Takazudo/zudo-case/engineering/two-way/tw-01/reference/hinge-user-photo.png

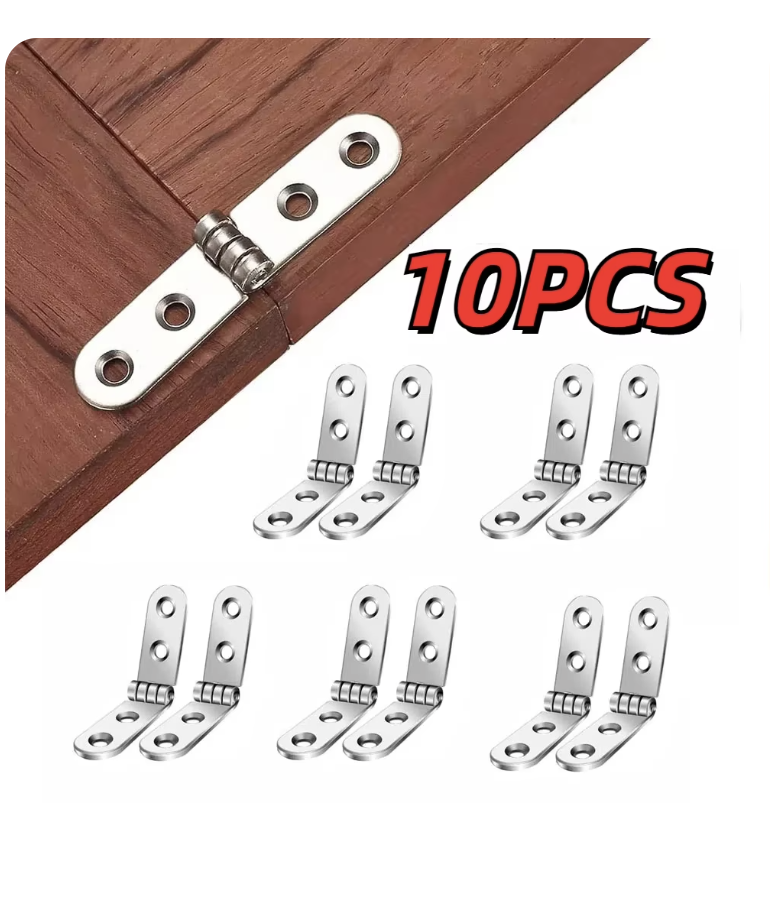
engineering/two-way/tw-01/reference/hinge-user-photo.png
