Takazudo/zudo-case/engineering/two-way/tw-01/previews/trunk-thumb.webp

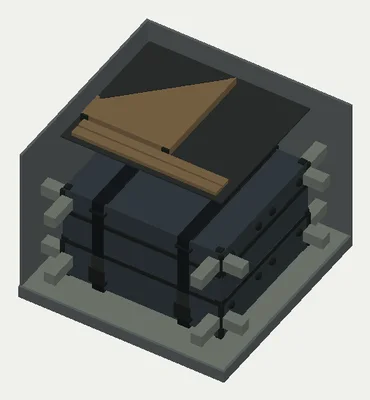
engineering/two-way/tw-01/previews/trunk-thumb.webp
