Takazudo/zudo-case/project/source-notes/user-decisions.md

# 会話中のユーザー指定・測定（抜粋）

これは会話全文のエクスポートではありません。発言順を保った関連抜粋です。個々の発言時刻は付与していません。サイト整理日は2026-09-24です。

## U01 — 製品の優先順位
「このケース考案のために重要な要素は価格と最低限の安全性。」
「可能であれば一枚板の組み合わせ＋ガードが利便性が高く、価格も抑えられそう」

## U02 — 外観、材料、在庫
「この商品自体が嗜好品であるため、ある程度の見た目の良さが必要」
「鉄板については、最初に提示してもらったものだとアルミが望ましい」
「アルマイト加工をした場合は黒にしたい」
「20x20x16 を大量にzudo-block用に所持しており、可能であればこれを使用したい」

## U03 — レールを独立させる
「エンクロージャとの間に5mm高のナイロンワッシャーを使用し、レールだけが分離出来る構造」
これは既存構造の説明。後のU06により新ケースのスペーサーは8mmへ変更。

## U04 — 積層・PCB厚
「3U fixer / 3U fixer padder / rail / 3U fixer padder / 3U fixer」
「PCB 1.6mm depth.」
ネジ頭は一度1mmで仮置きしたが、次の実測で更新。

## U05 — ネジ頭と金具の実測
「1.3-1.4mmであるため、1.4mmであると考慮」
「こちらは実測、2mm。ただしL字ブラケット自体が微妙に曲がってる可能性があるため2mm強ぐらいで考えた方が良い」

## U06 — 8mm案と３機種
「8mm案で。」
「3U3U1Uの40HP版、そして3U3U1Uの60HP版 も合わせて検討する」
「今回のケースで実は最も利便性が高いのは3U3U1U 40HPのケース」
「レールから前後パネルまでの余裕がありすぎること。ここはおそらく8mm程度で十分」

## U07 — 長穴の意図
「ネジ穴を正円としていないのは、穴位置の公差を考慮してのこと」
「ねじをしめるときの固定に頼って素材の誤差を吸収したい考え」
これは採用意図。R6ファイルが丸穴のままというデータ状態とは別。

## U08 — 薄型の本体ガード
「これらパーツはほぼ装飾用途と、ケース自体が他を傷つけないようにするため」
「この黒部分の幅も最低限継ぎ目を守れれば良い」
R3の1.2mm見積画面を提示し、「激安になった」。画面合計2,264円。

## U09 — 蓋は単純に
「our lid is the simple, original 10BOX style lid, but if the user want to take this to outdoors, they use that band things.」
「all right. so we'll do this plan. so, the final case lid style will be the simple original 10box style one.」
M3補助固定・回転ロック・スライドロックは最終案に含めない。

## U10 — 費用の対象
「レール部分は別途作っているのでこの計算に含める必要は無い」

## U11 — 引継ぎ
「zudo-doc based organized doc set」
「作ってもらったらあとはこっちでDLして整えるからその形でヨロシク」
