Takazudo/zudo-case/engineering/r9-fitfix-01/handoff/LOCAL-HANDOFF.md

# ローカルでの引継ぎ — R9-FITFIX-01

基準コミット `7f04c5bda0672ecf2cded79b6e1b48ad141e64b5`。
このセットは #99 / #100 / #101 の**修正コード＋実行済み候補CAD**です。レビュー文章だけのセットではありません。

## 何が終わり、何が残るか

| 作業 | 状態 |
|---|---|
| 下辺Lカバー、角の返しの修正 | 実装・クラウド生成済み |
| 壁厚と横方向の嵌合/接着すきまの分離 | 実装、BREPの厚さプローブで確認 |
| 実ガード上端から蓋座面・天板下面・段差を導出 | 実装・接触面積と公称着脱確認 |
| C1/C2修正＋C4/C5追加 | 生成・STL/STEP再読込済み |
| プレビュー | 同じ生成形状を内蔵。クラウドはWebGL不可のためCanvas簡易描画で操作検証 |
| Python3.12/CadQuery2.7系での再生成 | **ローカル待ち** |
| 現行R9の実DXFと本体穴パターン比較 | 比較ツール作成・合成fixtureテスト済み。実ファイル比較はローカル待ち |
| zudo-doc/current-spec/release-state/sync-r9-ledgerへの統合 | **未適用**。候補を混在させず版を分ける |
| GitHubへのpush、Issue close、製造承認、有償注文 | **未実施** |

## 最初のコマンド

まずzipを展開し、その中の`apply-overlay.py`を使います。既存ファイルは上書きしません。

```sh
python /path/to/zudo-case-fitfix-01/apply-overlay.py /path/to/zudo-case
# 内容・パスを確認後:
python /path/to/zudo-case-fitfix-01/apply-overlay.py /path/to/zudo-case --apply

cd /path/to/zudo-case/engineering/r9-fitfix-01
uv run --locked --project ../r9-prototype-01 python build.py
uv run --locked --project ../r9-prototype-01 python tests/test_geometry.py
uv run --locked --project ../r9-prototype-01 python tools/compare_r9_patterns.py
```

基準のGitHubコピーは接続済みGitHubツールで確認し、重要なR6入力６ファイルはGit blob SHA一致を確認済みです。ただしコンテナからGitHub/PyPI/npmへ直接接続できず、リポジトリ全体のclone・固定環境復元はしていません。cloud-outputのCADを、そのまま固定環境での再生成結果だと記録しないでください。

## 統合方針

`engineering/r9-fitfix-01`を独立した候補版として取り込む方法を推奨します。R9-PROTOTYPE-01の出力/台帳は履歴へ残し、同じ版名のまま差し替えません。別の候補名へ改名して取り込む場合は、ファイル・manifest・プレビュー・台帳の版を一括で合わせてください。

このコードの本体参照は、現在R9も継承している**保存R6の公称部品**を読み取り専用で再構築します。36本の長穴を含む本体５枚はR9の穴ルールで再作成しています。ローカルでは比較ツールで現行R9のDXF一致を確認し、必要なら本体参照を現在のR9ジェネレーターの実Part/配置インスタンスに置き換えてください。再構成した金具と実物の形が一致すると保証したものではありません。

1. 固定環境で生成し、修正前R9と新候補の本体３パターンを比較する。
2. 生成コードをレビューし、ガード主要部の実肉厚、屋根の直接着座、側面接着空間の解釈を確認する。
3. 新候補ディレクトリを読み込めるよう、`sync-r9-ledger`等のR9固定パスをパラメータ化、または新候補専用の入口へ分離する。古いR9のmanifestへ新しいhashだけを入れない。
4. 確認後の`tools/make_ledger_proposal.py --after-local-verification`をJSONへ保存し、candidate_filesの追加・蓋の現行候補指定に使う。候補と製造承認を混同しない。
5. docsの生成表/比較/BOM/プレビューの参照を新候補へ統一。publicのコピー後に公開資産ハッシュとサイズを検査し、旧画像との混在を防ぐ。
6. 既存CIのdocs/tables/ledger/assets/type/build/preview確認に加え、新しい11回帰テストと全体CAD生成を実行する。
7. ローカルで検証した新候補のoutを必要なファイルに絞ってGitへ追加し、コード差分と固定環境の結果をGitHubへ反映し、#99〜#101のコード課題としての完了可否を判断。G03/G04等の現物結果は別のまま。

## 重要な設計判断

**今回の支持面は金属との直接接触です。** 上端ガードの屋根下面はZ=91、本体上端へ載り、その屋根上面Z=92.2が蓋の座面です。以前の「全高93.4を上端Zと見なす」「蓋が0.5浮く」状態をなくしました。

側面の0.30mmの空きは、fit0.15＋adhesive0.15という候補配分です。これは「0.15mmテープを貼ればそのまま全て埋まる」という意味ではありません。実空間を充填して保持できる接着剤、またはテープ/当て材を選び、実測・試験で調整してください。上面/底面へ追加のテープを入れる場合はハードストップの高さが変わるため、パラメータとモデルを修正します。

**幅・奥行が各0.6mm増えます。** 金属本体寸法は変えず、外側ガードが片面0.3mm外へ増え、内側返しも実肉厚を確保します。蓋天板は基本案228.2×332.8×1.5mmです。1.0mm案の専用天板は227.8×332.4×1.5mmです。

部品を厚い旧形状へ戻す変更ではありません。基本案のガード総体積は約39.235cm³、蓋PA12枠は約84.378cm³です。価格は未取得。過去の2,264円は現在見積ではありません。

## 小型試験片を発注する前に

- C1-01〜05: 各１個。C1-06/07は同一形状を各２個として40mmの対を作る。
- C2-01の壁・ガード・天板は、C2-02/03へ再利用可能。比較用の蓋フレームは３種類。
- C4: 実際の床＋壁＋下辺Lカバー。
- C5: ２立板＋上端コーナー。
- PA12とアルミは別ZIP/別材質。`BOM.csv`のorder_quantityを優先し、0の再利用部材を重複発注しない。
- C3の座金受け面とネジ/工具アクセス、接着保持、実ノブ高さ、バンド/たわみは依然として未確認。

どの試験片も製造承認済みを意味しません。ただし試験片は未確定部分を調べるためのものです。全ての現物検証完了を試験片作成の前提にする循環にはしないでください。

## パッチ適用時の補足

`changes.patch`は16ファイルを新規追加するsource-only差分です。`git apply`時にベンダーThree.jsのGLSL文字列について末尾空白の警告が出ることがあります。元のライブラリ表現を保存しており、通常の適用は成功します。`apply-overlay.py`を使う場合はパッチも続けて適用しないでください。
