Takazudo/zudo-case/engineering/r9-prototype-01/out/DIFF-FROM-R6-R8.md

# R9-PROTOTYPE-01 / 7U40 — R6・R8との差分と梱包内容

**状態:** 製作候補・未承認。R6は本体形状の起点、R8は載せ蓋の表示用コンセプトです。ここに記すR9データも製作承認ではありません。

## R6本体からの変更

- R6由来の本体寸法をもとに、独立したアルミ板５枚を維持しています。板厚1.5 mm、A5052、黒アルマイトは候補です。
- ブラケット位置36か所を5.5 × 7.5 mm、±1.0 mm移動の長穴候補として出力しました。位置誤差を調整し、仮締め後に外形・直角を整えて本締めする狙いです。候補の長軸は折曲げ線に直交しますが、方向と移動量は製造確認が残ります。レール固定穴10か所はφ5.5 mmの丸穴を維持します。
- t1.2 mm・被覆5 mmのPA12-HPガードを主候補、t1.0 mmを比較候補として分離しました。ガードは保護用カバーで、構造接合には使いません。接着・保持・現物嵌合は未確認です。
- R6本体の穴位置は名目形状を引き継いでいます。ブラケット実物への照合、公差、ワッシャー、ねじと工具のアクセスは完了していません。

## R8蓋コンセプトからの変更

- 採用したロックなしの構成を具体化するため、直線的に載せて持ち上げる蓋と、アルミ蓋板＋４分割PA12位置決め枠を7U40候補形状として書き出しました。運搬時の保持は別体の外周バンドを想定します。
- R7のM3蓋・本体ロック、フック、回転、スライド、磁石は採用していません。蓋板とPA12枠の組立ねじは別部品ですが、仕様は暫定です。
- R8の表示用形状を製作用ファイルとして再利用したものではありません。R9ジェネレーターで出したSTEP/STL/DXFは候補データで、蓋とガードの実嵌合やノブ・ケーブル空間を検証していません。
- 蓋上がり30 mm、モジュール板2 mm＋ノブ25 mm、ケーブルを外す前提は表示上の仮定です。全モジュールのノブ高さ・配線条件を検証した値ではありません。

## 重要な未確認事項

- 長穴は36か所候補です。現在の10 mm外径ワッシャー案は壁側の複数位置で受け代が不足します。必要外径11.5 mm以上は試す候補で、選定済みではありません。
- ガード保持・接着、公差、黒染色条件、蓋枠の座面、工具アクセス、実ノブ高さ、バンド長・張力・蓋たわみが未確認です。
- 保存済みR9検証は名目CAD/データ整合の確認です。FEA、強度、材料適合、物理嵌合、落下、疲労、運搬試験を示しません。
- G01–G11 は未完了です。サプライヤーへの送付、発注、製造承認を行う状態ではありません。

## ZIPの範囲

- アルミ: ６枚の板のSTEP/DXF、穴テーブル、長穴チェック。
- PA12: ガードt1.2主候補、t1.0比較候補、蓋枠４部品のSTEP/STLと数量表。
- クーポン: C1、C2、C3のファイルと、ZIP内相対パスを記録したcoupon-manifest.json。
- 各ZIPは25 MiB未満で、`READ-BEFORE-ORDER.txt`とSHA-256付きpackage-manifest.jsonを含みます。

## 見積とサイズ

現在の材料・加工・印刷見積はありません。価格欄はnullです。既存在庫ブラケット18個だけは追加現金支出0円として扱い、製品原価は不明のままです。レール、fixer、padderの費用は依頼により除外しました。異寸法の過去R3ガード価格は流用していません。

新たにコミットするファイル別サイズと合計は `SIZE-INVENTORY.json` に記録します。`engineering/r9-prototype-01/.gitignore` が `out/` 全体を除外するため、CADの重複中間STL、hardware-envelope、アセンブリ検査物、プレビューmesh/断面画像はコミットせず、必要な6枚等を各候補ZIPにだけ収録します。
