Takazudo/zudo-case/engineering/r6-body/docs/family-final-review.md

# R6・3ケースの独立レビュー結果

`zudo-case-family-preview` の最終モデルを確認した。元レールSTL、PCB全輪郭、生成メッシュ、PCB STEP、穴配置、ガードカタログ、最終検証結果を照合し、以下の範囲に未解決の不整合は見つからなかった。

| 項目 | 3U60HP | 7U40HP | 7U60HP |
|---|---:|---:|---:|
| 金属外形W×D×H mm | 330.4×154×91 | 229.4×334×91 | 330.4×334×91 |
| 実レール長mm | 305 | 204 | 305 |
| レール本数 | 2 | 6 | 6 |
| fixer〜前後板内面の隙間mm | 8.23407 | 8.122772 | 8.122772 |
| Lブラケット個数 | 16 | 18 | 18 |
| 接合穴のブラケット同軸確認 | 32穴一致 | 36穴一致 | 36穴一致 |
| ケースへのレール固定 | 片側2点 | 片側5点 | 片側5点 |
| ガード個数／種類 | 12個／4種類 | 16個／6種類 | 16個／6種類 |
| t1.2ガードの最大部品寸法mm | 166.4 | 168.2 | 168.2 |

## 元形状と配置

- 元レールの全592三角形を保持している。各変換は回転・移動だけで、逆変換後の頂点最大誤差は7.1×10⁻¹⁵mm以下。
- fixer／padderの元輪郭・切り抜きの全頂点を生成メッシュへ照合した。最大座標誤差は5.7×10⁻¹⁴mm以下。板厚1.6mmと、7Uの各padderの外形基準による配置が維持されている。
- 7Uの6本は、各行で前後の外リップが外側へ向く交互配置。隣接行のレール本体同士にはY方向で**0.330246mm／0.365509mm**の正の隙間がある。元STL全頂点の外接範囲がY方向で分離しているため、本体同士が交差していないことを確認できる。
- 7Uの片側5点のM5取付ボルトを頭径9mm・高さ1.4mmとして独立に再構成し、出力PCB STEPと比較した。全固定点でPCBとの交差体積は0mm³。左側は同じYZ配置と積層の鏡像である。
- 7Uのfixer下端から底部L金具上端までの垂直包絡差は**7.984619mm**。

## 頭径の追加検討を区別

生成側の検証では、実厚2mmのL、内側の接合ネジ頭、ケース固定用頭、ガード、PCBの実体交差はない。L占有厚2.2mm・レール端頭径12mmの追加検討でも、ブラケット側との交差はない。

一方、7Uの隣接するレール端頭を両方D12と仮定すると、軸間11.9960175mmの組で約0.004mmの径方向包絡重複が生じる。この値はケース隙間とは別の、既存レールユニット内の関係。模式表示D9の頭同士は交差しない。D12は現物の保証上限ではなく、追加の検討用寸法として分けて記録されている。

## 底板と脚

底板の8点／10点だけはネジ頭を外側に向け、ワッシャー・ナットを内側へ移している。側面のfixer固定の向きは変更していない。

各ケースの脚は仮のD10×高さ3mmを4個、中心を各外縁から20mm内側に配置。脚と底ネジ中心の最短距離は約22.192mmで、両者は重ならない。

- 脚下面：Z−3mm。
- 底板ネジ頭の最下面：Z−1.4mm。
- 接地面から底ネジ頭までの公称余裕：**1.6mm**。
- 全パーツの最下面は脚のZ−3mmで、それより下へ出るネジ・ナットはない。
- 脚込みの高さはt1.2ガード時**95.2mm**、t1.0時**95.0mm**。ガードだけを含めた外形高さとは異なる。

脚は既製貼付ゴム脚を想定する模式部品で、JLCガードSTLやガード体積には含めていない。

## データの範囲

ガードは全32種類のSTLについて、生成検証で閉じたメッシュ・正の体積・CAD体積との一致が確認されている。各モデルのガード数量と最大寸法は独立にカタログと照合した。

ブラケットの穴中心と曲げ部、模式表示の頭径・ネジ長・ナット、脚の製品選定、ガードの保持方法と嵌合公差には設計前提が残る。上記は公称寸法と配置の確認で、製造公差や荷重を含む完成品の試験ではない。

機械読取用記録：`family-core-independent-checks.json`、`family-final-foot-checks.json`、`expected-7u-rail-gaps.json`。
