Takazudo/zudo-case/engineering/two-way/tw-01/reference/PROVENANCE.md

# TW-01 provenance

Derivative of the verified original F5 source archived at `../../f5-reference/`.
Original ZIP SHA-256: 2060f83d75c93c7e5a29e6fe0751ac1fae101dccba8c7bf08d2a43080f7b4e58.
TW-01 is not byte-identical F5. Historical source receipts belong to F5 only.

Maintained frame data consumes canonical R6 saved rail meshes, PCB outer/cutout vertices and placement records. Input hashes and Shapely/GEOS version are embedded in `source/frame-data.js`.
No geometric fitting or rail topology repair. The display triangles are not a manufacturing definition.
Hardware, strap/stand/hinge envelopes remain provisional. The user's hinge drawing is retained unchanged; its dimensions provide no load rating or mounted folding proof.
