Takazudo/zudo-case/src/content/docs/two-way/rail-frame.mdx

---
title: "元レール・PCBフレーム"
description: "元形状、配置基準、8mm積層、Cの70mm蓋と表示用三角形の範囲。"
sidebar_position: 20
---

import { TwoWayFrameTable } from '../../../components/two-way-table.jsx';

## 両トレーに元のユニット

Aは元の3U/60HPを1組ずつ、Bは同じ3U/60HPを**1 mm離して2組ずつ**使います。B用に6Uの側板を新設・伸長しません。Cは7U fixerを全体のまま、3U＋3U＋1Uの行別padderと使います。

<TwoWayFrameTable />

数量は各トレー分で、2トレーにはその2倍を使います。これは元フレームの数量であり、ケース全体のBOMではありません。

## 固定と座標基準

レールは40HPが204 mm、60HPが305 mm。元の全頂点と全インデックスを保持し、剛体変換だけを適用します。元の重複・非多様体面を勝手に修復しません。

積層は **padder 1.6 + fixer 1.6 + 側面スペーサー8 + 外側座金1 mm**。皿頭高さ1.4 mmの検討値を保持します。実ねじ・ナット・穴加工・工具アクセスの成立は別途確認します。レール付近の隙間を常設ベゼルで埋めません。

正規ソースは `engineering/r6-body/source-data/`。7Uは元Xが奥行V、元Yが列方向Uです。わずかな外形段差・穴中心・padderのずれを維持します。配置は保存済み `placements.json`、空の3Uケース固定軸だけはR6 `build_geometry.py` の明示組立規則を使用します。近い穴や対称位置を推測しません。

## Cの48 mmと70 mm

元7Uフレームは前面から約61.950925 mm後方まで届きます。板厚1.5 mmでは、蓋48 mmの背板余裕は **−15.450925 mm**、蓋70 mmは **＋6.549075 mm**。TW-01のCの初期値は70 mmです。

ビューアーで48 mmを入力すると、フレームを切り縮めず干渉警告を出します。正の数値もモジュール適合や工具アクセスを保証しません。モジュール後方の余裕・元フレーム後端・局所の補強材やバス基板は分けて表示します。

## F5とTW-01の違い

F5のレールは元メッシュそのままですが、PCBの丸穴・長穴は表示用近似でした。TW-01は保存済みの外周と切欠きの全ポリゴン頂点を読み、固定版の変換環境で三角形化します。元KiCadとソース輪郭、表示三角形、仮金具は異なる精度区分です。

[資源とマニフェスト](./resources.mdx)には入力・出力ハッシュと単位を記録します。GLBを製造データとして発注しないでください。
