Takazudo/zudo-case/src/content/docs/handoff/tasks.mdx

---
title: "次に行う作業"
description: "7U40から試作へ進め、共通構造を３機種へ展開する。"
sidebar_position: 20
---

R9-PROTOTYPE-01の[未承認候補](../design/r9-prototype-01.mdx)と[試験手順](../verification/fit-test.mdx)が用意された。次は[空欄の現物測定](../verification/measurements.mdx)を必要な範囲で埋め、C1→C2→C3の判定条件を先に決め、有償試作をユーザー判断で進める。座金受け面（仮OD10mmで壁26穴不適合）、接着保持、実ノブ、バンド荷重、天板たわみが残る。見積文は[未送信RFQ](../manufacturing/r9-rfq-draft.mdx)。下記の表は当初の工程案として読む。

## まず7U40で共通部を詰める

ユーザーが持ち運びで重視している7U40を最初の確認対象とする。ただし共通部の変更は3U60・7U60にも追従させる。これは進行案であり、発注数量を確定したものではない。

| 順番 | 作業 | 成果物 |
|---|---|---|
| 1 | R9候補の版・ハッシュ・警告を確認 | 同一版のCAD、プレビュー、数量表 |
| 2 | 手持ち金具・ネジ・座金を確認 | 代表寸法、長穴が吸収すべき範囲 |
| 3 | R9の短い本体ガードをC1で確認 | PA12・アルミ端・接着層の記録 |
| 4 | R9の上端ガードと蓋をC2で確認 | 段差と天板の現物記録 |
| 5 | 実金具と長穴をC3で確認 | 座金受け面、締結アクセス、CAD修正 |
| 6 | ケース１台を組み、バンドを試す | 実モジュール・ノブ・リュックでの確認 |
| 7 | 最新データで業者比較 | 機種別・数量別・税込税抜が明確な見積 |
| 8 | 検査条件と承認資料を確定 | 承認manifest、製作ZIP |

## ローカルのAIエージェントへの引継ぎ文

```text
AGENTS.md、project/current-spec.json、project/open-issues.jsonを最初に読んでください。
現行方針は真上へ外す載せ蓋＋外周バンドです。
R9-PROTOTYPE-01は7U40の未承認候補。file-table.jsonとvalidation.jsonを確認してください。
座金受け面、ガード接着、蓋と実ノブ、バンド荷重をC1→C2→C3から確認します。
R7のM3補助固定、回転/スライドロック、奥フックは復活させないでください。
ユーザー確認済み寸法を守り、表示上の仮値は現物確認済みと扱わないでください。
7U40の実測と小片の結果を記録し、承認前に発注しないでください。
```

## 作業を引き継ぐ際の境界

今回の依頼はドキュメント作成であり、注文操作や新CADの製作承認は含まない。次の担当が自動的に発注へ進めないよう、リリース状態をfalseのまま残している。

`engineering/r6-body`と`engineering/r8-preview`の元ファイルは保存する。変更は新しい作業ディレクトリーと版で行い、元データとの差分を残す。
