Takazudo/zudo-case/src/content/docs/models/7u60.mdx

---
title: "3U＋3U＋1U・60HP"
description: "本体はR6の名目CAD、載せ蓋はR8プレビュー。7u60の寸法と数量。"
sidebar_position: 30
---

{/* GENERATED: node scripts/sync-reference-tables.mjs / project/current-spec.json */}

## この機種

３機種に共通する金属平板と独立レールの構造を使う。 3U＋3U＋1Uは同じ平面に並ぶ。上下二段のケースではない。

R6の組立形状

## 寸法と数量

| 項目 | 値 |
|---|---|
| 本体アルミ外形 W×D×H | **330.4 × 334 × 91mm** |
| 1.2mmガード込み（脚・外側金具を除く） | 332.8 × 336.4 × 93.4mm |
| ガードと仮脚込み（外側金具を除く） | 332.8 × 336.4 × 95.2mm |
| 実レール長 | 305mm |
| レールユニット外幅 | 311.4mm |
| 全ユニットの前後包絡 | 314.754456mm |
| 前後板の内面までの片側余白 | 8.122772mm |
| 上端ガードまでの片側余白 | 7.122772mm |
| レール本数 | 6 |
| ブラケット | 18 |
| レールと外箱のM5締結 | 10点 |
| 内側8mmスペーサー／外側1mm座金 | 各10個 |
| 板の穴合計 | 46（R6の丸穴。長穴未反映） |

## アルミ本体５枚

| 部品 | サイズmm | 枚数 | 穴数/枚 |
|---|---|---:|---:|
| 底板 | 330.4 × 334 × 1.5 | 1 | 10 |
| 前後板 | 327.4 × 89.5 × 1.5 | 2 | 6 |
| 左右板 | 334 × 89.5 × 1.5 | 2 | 12 |

材質候補A5052、t1.5、黒アルマイト。外形・板厚は現在の名目値。長穴、穴中心、公差、表面の許容状態を確定してから製作承認する。

## ガード1.2mmの内訳

| 部品 | 数量 | 単体の外接寸法mm | 単体体積cm³ |
|---|---:|---|---:|
| 上端L字ガード A | 2 | 166.4 × 168.2 × 6.2 | 3.458 |
| 上端L字ガード B | 2 | 166.4 × 168.2 × 6.2 | 3.458 |
| 前後下辺・半分 | 4 | 166.4 × 6.2 × 6.2 | 2.231 |
| 左右下辺・半分 A | 2 | 6.2 × 167 × 6.2 | 2.202 |
| 左右下辺・半分 B | 2 | 6.2 × 167 × 6.2 | 2.202 |
| 縦辺コーナーガード | 4 | 6.2 × 6.2 × 81 | 1.086 |

合計**16個、35.906cm³**。1.0mm版は**29.297cm³**。STLは１個ずつ、数量を注文画面へ指定する。

<PreviewLink path="/downloads/reference/7u60-r6-guards-t1p2-NOT-RELEASED.zip">1.2mm STL一式</PreviewLink> ／ <PreviewLink path="/downloads/reference/7u60-r6-guards-t1p0-NOT-RELEASED.zip">1.0mm STL一式</PreviewLink> ／ <PreviewLink path="/downloads/reference/7u60-r6-aluminum-NOT-RELEASED.zip">アルミ参考データ</PreviewLink>

## 蓋はR8の表示寸法

天板：**328.6 × 332.2 × 1.5mm**。蓋の外周：332.8 × 336.4mm。蓋付き高さは脚・模式ねじ頭まで**128.8mm**。バンド・側面ナットの突出は別。

前後の段差を差し込み、真上へ外す。30mmのノブ用高さ、2mm厚の段差、差し込み12mm、片側0.7mmの隙間は現在のプレビュー条件で、実物のフィットを保証しない。

バンド一周の幾何概算：**923.2mm**。バックルと重なり代は含めていない。

**この載せ蓋の製作用CADは未更新。** R7のロック用枠・前後M3穴を発注しない。[R8プレビュー](../resources/current-preview.mdx)と[発注前ゲート](../verification/before-order.mdx)を確認する。

## 根拠

R6の engineering/r6-body/engineering/7u60/model-summary.json と [本体サマリー](/evidence/r6-family-summary.json)、[ガードmanifest](/evidence/7u60-t1p2-r6-guard-manifest.json)、[R8パラメータ](/evidence/r8-preview-parameters.json)から表を生成した。今回、新しいCADを検証した値ではない。
