Takazudo/zudo-case/src/content/docs/resources/body-preview.mdx

---
title: "R6・本体とレールのプレビュー"
description: "８mmスペーサーと３機種の名目寸法を確認する。"
sidebar_position: 20
---

## 本体だけ詳しく見る

**<PreviewLink path="/previews/r6-body.html">R6本体プレビューを別タブで開く</PreviewLink>**。約33MBの単一HTML。大きいためここでは自動埋め込みしない。

<PreviewSource />

R6のレール脱着表示

３機種、ガード1.2/1.0mm、分解、レール脱着、識別色、透過、断面、部品選択、STL保存がある。R6に内蔵されている保存用STLはR6形状であり、最終保持公差を入れた新リリースではない。

## このプレビューでは分からないこと

最終の長穴化、ガード保持、R8載せ蓋の製作形状、バンドの実物、電源/配線の最終収まりは未反映。ねじやナットの一部は模式値。

R8を見ると完成形の意図、R6を見ると本体の構造を確認できる。どちらか一方だけを最終発注の根拠にしない。[ファイル対応表](./files.mdx)を参照する。
