Takazudo/zudo-case/src/content/docs/overview/index.mdx

---
title: "はじめに"
description: "現在地と、製作へ進むための読み順。"
sidebar_position: 10
---

現在地と、製作へ進むための読み順。

<CategoryNav category="overview" />
