Takazudo/zudo-case/engineering/r9-fitfix-01/handoff/FIT-RECORD.md

# R9-FITFIX-01 小型試験片の結果記入用

これは未記入の記録用紙です。結果や承認は含みません。先に固定環境での再生成・ファイル比較を済ませ、実際に使った部品IDとファイルSHA-256を記録します。

## 試作ロット

| 項目 | 記入欄 |
|---|---|
| 実施日・担当 | |
| 候補版・ファイルSHA-256 | |
| 造形サービス・材質・黒染め・造形条件 | |
| 金属材質・実板厚・表面処理 | |
| 接着剤／テープ／当て材の品番・実測厚・処理・養生条件 | |
| 使用した締結材の品番 | |

## 試験片別

| 試験片 | 確かめる点 | 観察・測定 | 判定・次の変更 |
|---|---|---|---|
| C1-01〜05 | 側面すきま、屋根の着座、実肉厚、保持方法、比較条件 | | |
| C1-06/07 | ２片の継ぎ目、段差、接触する金属端 | | |
| C2-01〜03 | 蓋の差し込みと抜き差し、支持面、M3組立、0.5/0.7/0.9の比較 | | |
| C4-01 | 底板＋立板に対し下辺Lガードが収まる、接着・固定、金属端の露出 | | |
| C5-01 | ２立板が交わる角にガードが収まる、側面／屋根の当たり、端の安全性 | | |

0.30mmの側面空間は、fit0.15＋adhesive0.15という候補配分です。単に0.15mmテープを貼るだけで固定できるとは扱いません。実際に空間を埋めて保持できる方法を記録してください。上面/下面へテープを追加する場合は座面高さが変わるので、モデルへ戻して修正します。

## １台試作時の追加事項

小型片の成功だけでは、長い部品の反り、全体の組立、長穴/座金、実ノブ/スイッチ高さ、脚の圧縮、バンド締付時の天板たわみ、運搬を確認したことになりません。実荷重・操作回数・試験条件と判定基準を定め、その記録は別途残します。
