Takazudo/zudo-case/src/content/docs/models/index.mdx

---
title: "３機種の仕様"
description: "共通寸法から生成したモデル別の寸法・数量。"
sidebar_position: 20
---

共通寸法から生成したモデル別の寸法・数量。

<CategoryNav category="models" />

## 独立した2WAYの実験設計

[2WAY / TW-01](../two-way/index.mdx)は2つのモジュール入りトレーを使う別系列です。現行R9製作候補や既存3機種の仕様は変更しません。
