Takazudo/zudo-case/src/content/docs/two-way/preview.mdx

---
title: "TW-01 ワークベンチ"
description: "オフラインでも使える日本語の2WAY寸法・姿勢検討ビューアー。"
sidebar_position: 30
---

import { PreviewLink, PreviewFrame, PreviewSource } from '../../../components/preview-links.jsx';

**TW-01 / 実験設計。実機嵌合・強度・運搬・製造は未承認です。** [元資料F5との差分](./rail-frame.mdx)を確認してください。

<PreviewLink path="/previews/two-way/tw-01.html">TW-01を直接開く（別タブで使う場合もこのリンク）</PreviewLink>

<PreviewSource />

<PreviewFrame path="/previews/two-way/tw-01.html" title="TW-01 2WAY実験設計ワークベンチ" height={920} />

## 操作

A/B/Cを選び、演奏・収納・レール・接合部・トランクを切り替えます。「その他の検討姿勢」にスタンド収納・カラー部品・蝶番があります。姿勢の変更は入力した物理寸法を初期化しません。

ドラッグまたは矢印キーで回転、ホイールまたは＋−でズーム、Rで全体表示。「拡大」からEscapeで戻り、操作元へフォーカスが戻ります。PNGは選択姿勢・版・描画方式付きで保存します。

設定はTW-01の独立schemaで保存します。元F5 schema-5も明示変換して読み込みます。入力全体を検査してから置換し、破損・不正・未知schemaでは前状態を保ちます。取り込んだ派生寸法・承認フラグ・外部URLは信用しません。F4は構造が異なるため非対応です。

## 表示の限界

WebGLを使えない場合はSoftware 3Dへ切り替わります。描画方式はビューアー上部に表示します。モードやスクリーンショットは物理検証の証明ではありません。前面72/58 mmは配線プロファイルの仮定です。

収納包絡とトランク内寸、元フレーム後端とモジュール深さを区別してください。正の隙間も耐荷重・安全な閉鎖・連続開閉を保証しません。Cの48 mm蓋など干渉する入力も元形状を保持して表示します。
