Takazudo/zudo-case/src/content/docs/models/comparison.mdx

---
title: "３機種の比較"
description: "共通値と、機種によって増える板・金具・ガードを一覧にする。"
sidebar_position: 40
---

{/* GENERATED: node scripts/sync-reference-tables.mjs / project/current-spec.json */}

## 本体比較（7U40は現行候補）

| 機種 | アルミ外形mm | ガード込みmm | 金具 | ケース固定M5 | ガード個数 | 1.2mm体積cm³ | R9候補 |
|---|---|---|---:|---:|---:|---:|---|
| 3U・60HP | 330.4 × 154 × 91 | 332.8 × 156.4 × 93.4 | 16 | 4 | 12 | 27.333 | — |
| 3U＋3U＋1U・40HP | 229.4 × 334 × 91 | 232.4 × 337 × 93.4 | 18 | 10 | 16 | 39.235 | R9-FITFIX-01・未承認 |
| 3U＋3U＋1U・60HP | 330.4 × 334 × 91 | 332.8 × 336.4 × 93.4 | 18 | 10 | 16 | 35.906 | — |

7u40の現行候補は[R9-FITFIX-01](../design/r9-fitfix-01.mdx)です。上表の7U40ガード寸法・体積は同候補の生成値です。現物の嵌合・保持・運搬確認と製造判断が残り、未承認です。3u60と7u60の数値はR6/R8基準です。

単位mm。ガード込みは脚・外側ナット・蓋・バンドを除く。３機種ともアルミの高さは91mm、レールの側面離隔は8mm、前後の全ユニットからの余白は約8mm。

## 共通部と差分

40HPは実STL長204mm、60HPは305mm。HPの比で引き延ばしていない。3U→7Uは前後方向を長くし、fixerを7Uへ交換、3U padder２個と1U padder１個を各側へ配置する。

3Uは16個の金具と４点の外箱固定、7Uは18個と10点。長い左右板の底辺には中央金具を追加する。ガードの分割数も12→16個へ変わる。

[3U60](./3u60.mdx) ／ [7U40](./7u40.mdx) ／ [7U60](./7u60.mdx)

## 蓋と運搬

全機種でR8の載せ蓋＋バンド２本を採用。蓋高さ30mm、閉じたモデルの高さ128.8mmは共通の表示条件だが、ノブ高さ・締付時の天板のたわみを確認して最終化する。

R8の天板サイズは各機種ページに示した。機種間で同じ部品として注文できるかは、完成したCADのファイルと数量を照合して決める。似た外形だけで同一品へまとめない。

出典：[R6サマリー](/evidence/r6-family-summary.json)、[R8パラメータ](/evidence/r8-preview-parameters.json)。
