Takazudo/zudo-case/src/content/docs/decisions/index.mdx

---
title: "判断履歴"
description: "採用・不採用と、変更理由を残す。"
sidebar_position: 70
---

採用・不採用と、変更理由を残す。

<CategoryNav category="decisions" />
