Takazudo/zudo-case/src/content/docs/handoff/index.mdx

---
title: "ローカルへの引継ぎ"
description: "zudo-docの初期化、更新手順、次の作業。"
sidebar_position: 80
---

zudo-docの初期化、更新手順、次の作業。

<CategoryNav category="handoff" />
