Takazudo/zudo-case/src/content/docs/resources/index.mdx

---
title: "データとプレビュー"
description: "現行プレビュー、版別のCAD、根拠ファイル。"
sidebar_position: 60
---

現行プレビュー、版別のCAD、根拠ファイル。

<CategoryNav category="resources" />
