Takazudo/zudo-case/engineering/r9-prototype-01/out/preview/sections/guards-adhesiveLayer.png

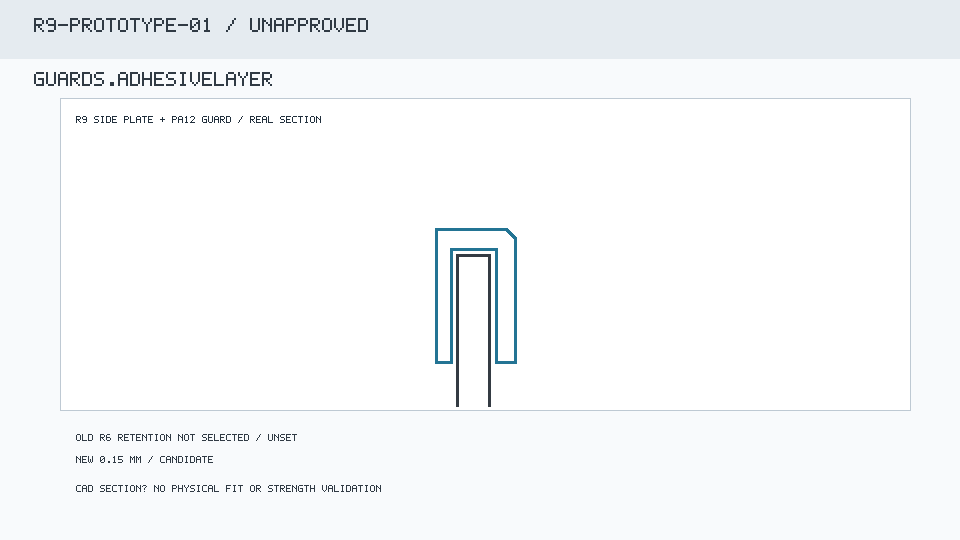
engineering/r9-prototype-01/out/preview/sections/guards-adhesiveLayer.png
