Takazudo/zudo-case/engineering/r9-prototype-01/out/preview/sections/lid-knob_envelope_height.png

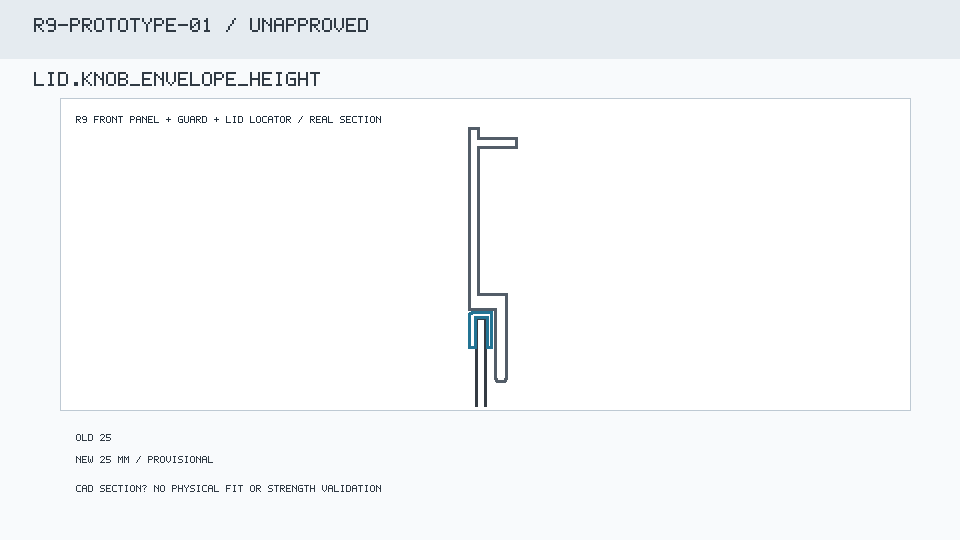
engineering/r9-prototype-01/out/preview/sections/lid-knob_envelope_height.png
