Takazudo/zudo-case/engineering/r9-prototype-01/out/preview/sections/slots-bearing_overlap.png

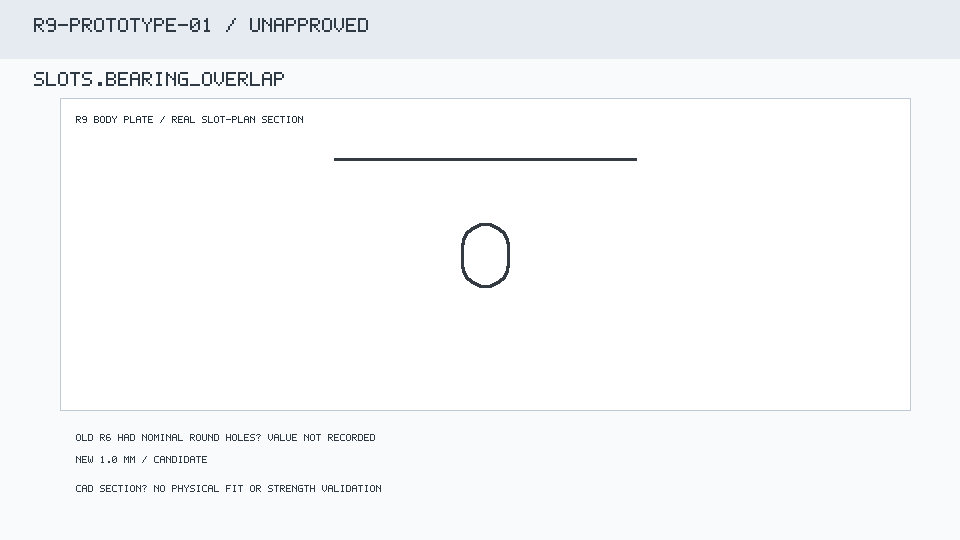
engineering/r9-prototype-01/out/preview/sections/slots-bearing_overlap.png
