Takazudo/zudo-case/engineering/r9-prototype-01/preview/shots/r9-prototype-01-daily.png

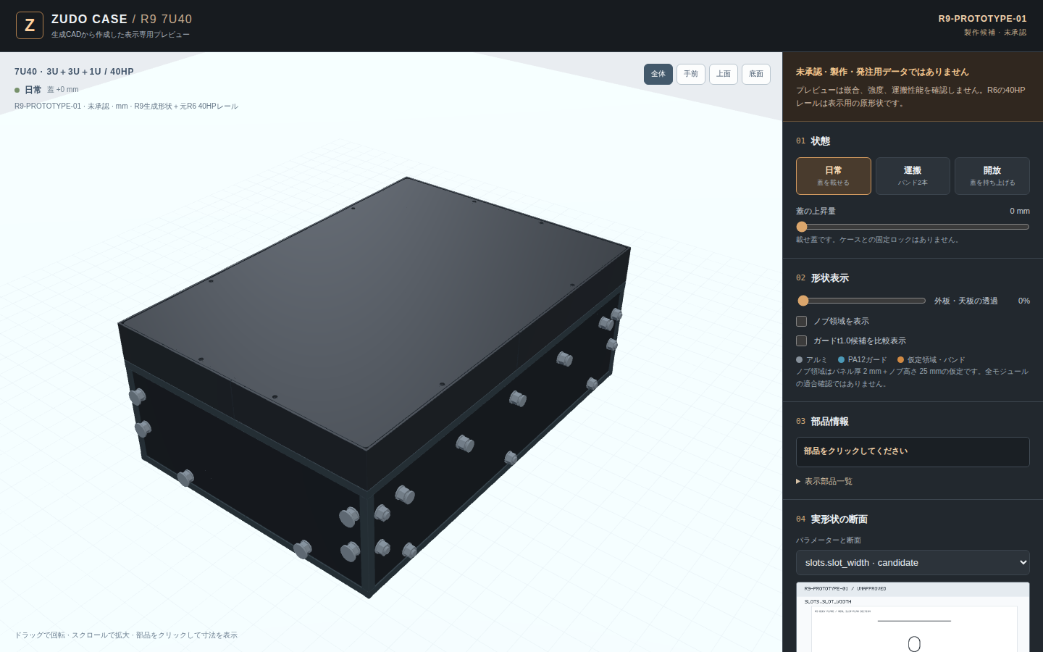
engineering/r9-prototype-01/preview/shots/r9-prototype-01-daily.png
