Takazudo/zudo-case/engineering/r9-prototype-01/preview/shots/r9-prototype-01-open-mobile.png

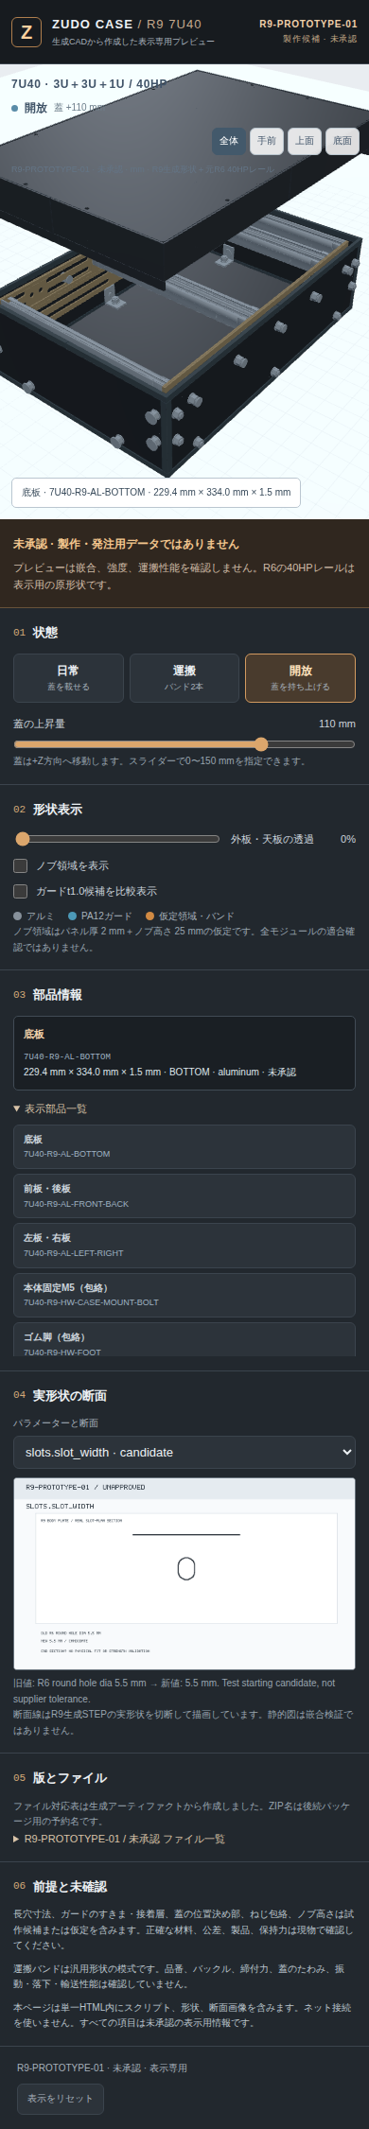
engineering/r9-prototype-01/preview/shots/r9-prototype-01-open-mobile.png
