Takazudo/zudo-case/engineering/two-way/f5-reference/previews/closed-thumb.webp

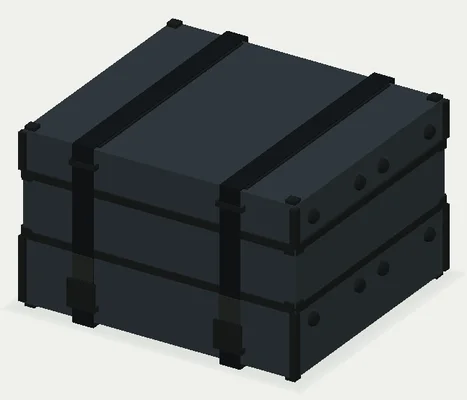
engineering/two-way/f5-reference/previews/closed-thumb.webp
