Takazudo/zudo-case/engineering/two-way/f5-reference/previews/frame-thumb.webp

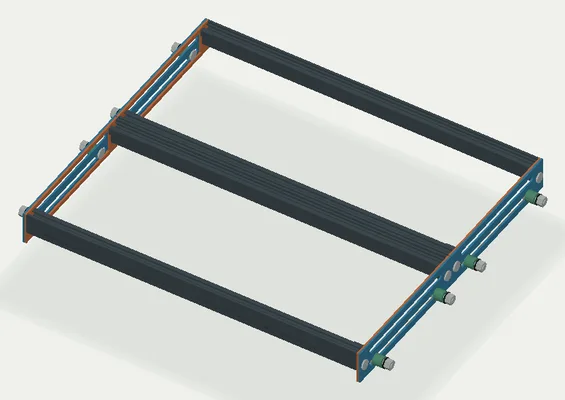
engineering/two-way/f5-reference/previews/frame-thumb.webp
