Takazudo/zudo-case/engineering/two-way/f5-reference/reference/hinge-user-dimensions.png

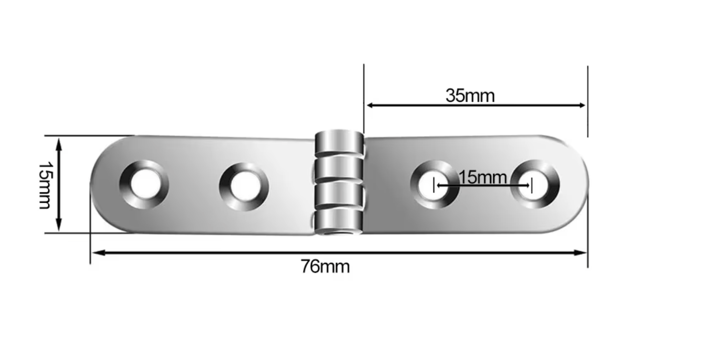
engineering/two-way/f5-reference/reference/hinge-user-dimensions.png
