Takazudo/zudo-case/engineering/two-way/tw-01/evidence/docs-390.png

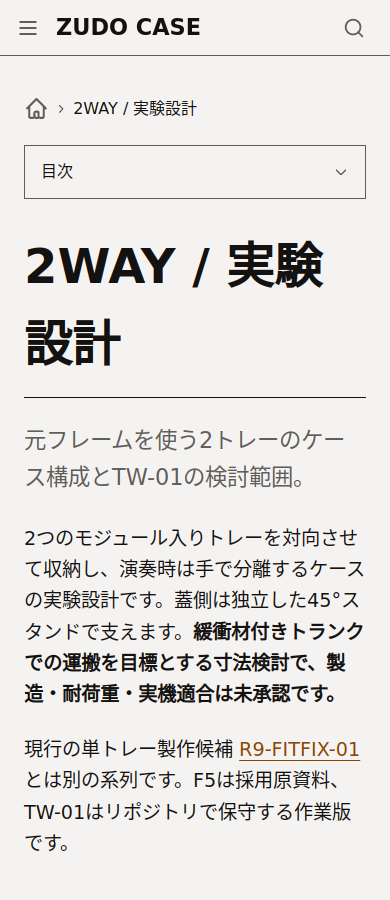
engineering/two-way/tw-01/evidence/docs-390.png
