Takazudo/zudo-case/engineering/two-way/tw-01/evidence/software-390.png

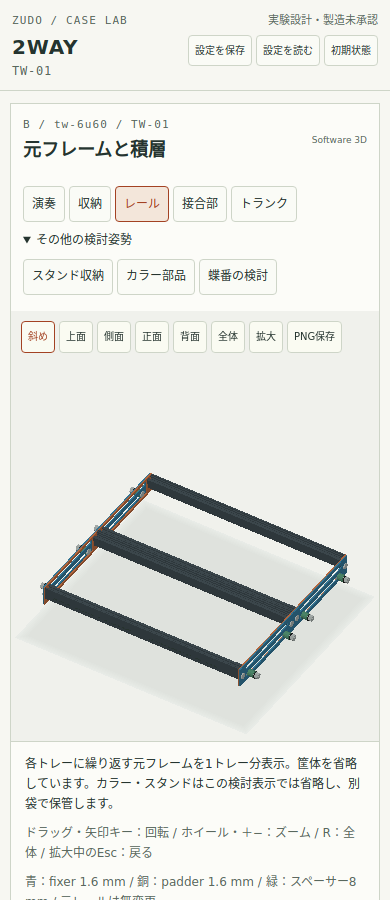
engineering/two-way/tw-01/evidence/software-390.png
