Takazudo/zudo-case/engineering/two-way/tw-01/evidence/webgl-B-play.png

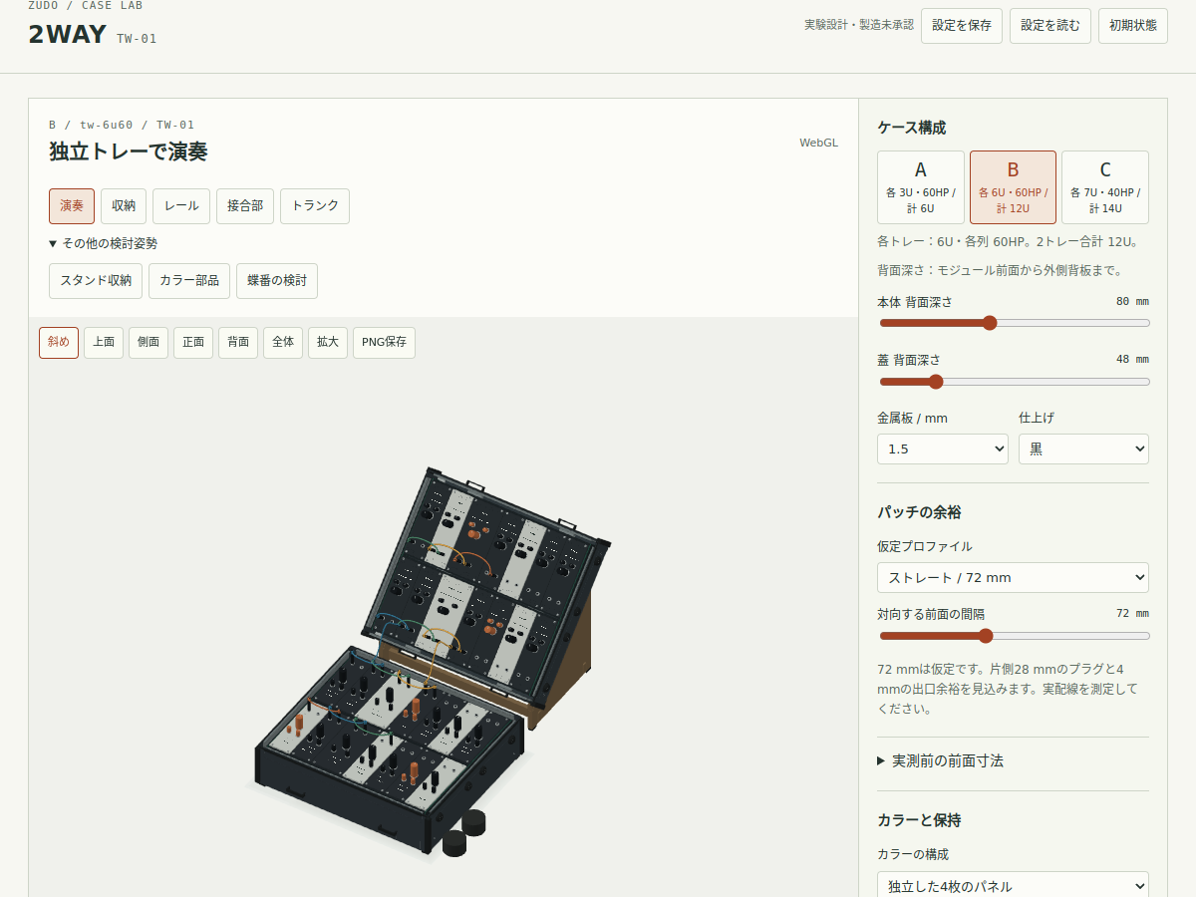
engineering/two-way/tw-01/evidence/webgl-B-play.png
