Takazudo/zudo-case/engineering/two-way/tw-01/evidence/webgl-C-invalid48.png

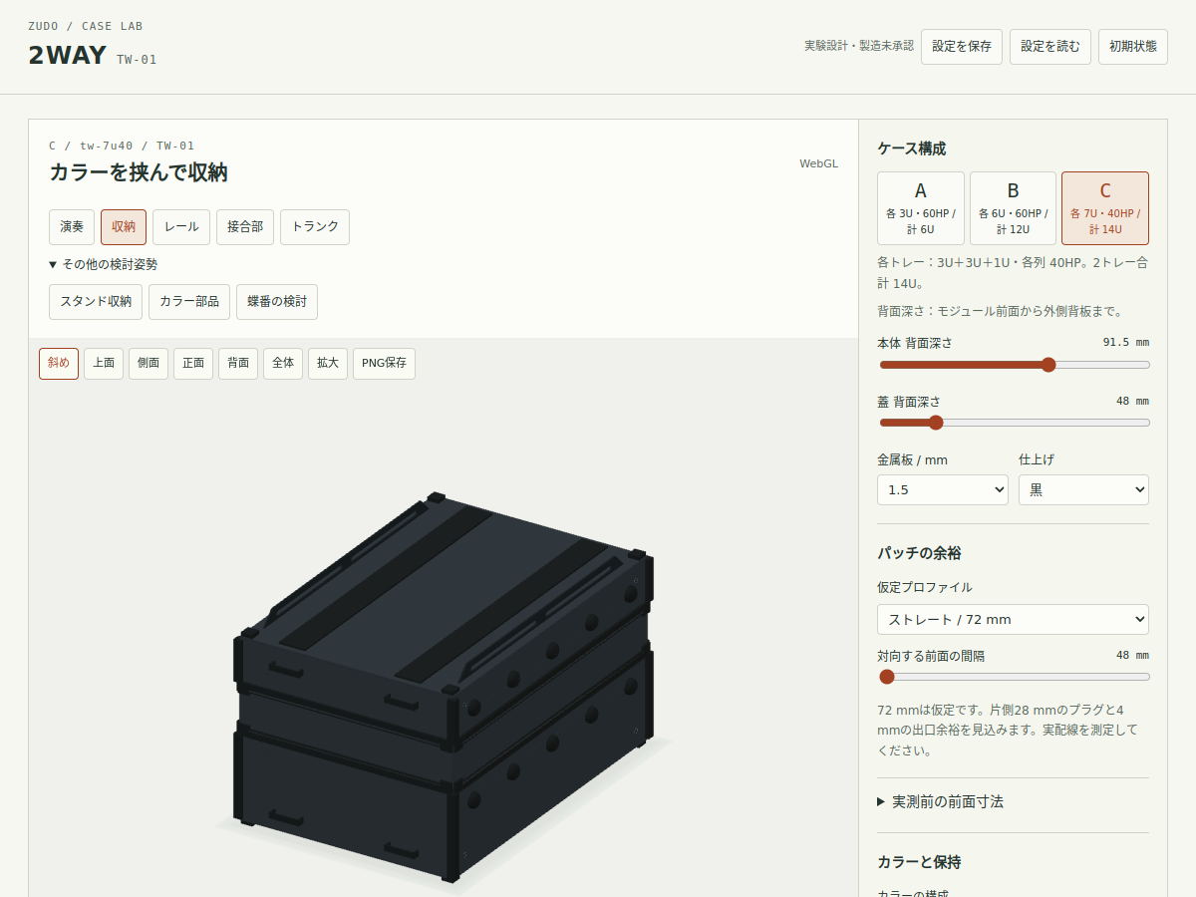
engineering/two-way/tw-01/evidence/webgl-C-invalid48.png
