Takazudo/zudo-case/public/assets/evidence/r2-jlc-quote-incomplete-quantity.png

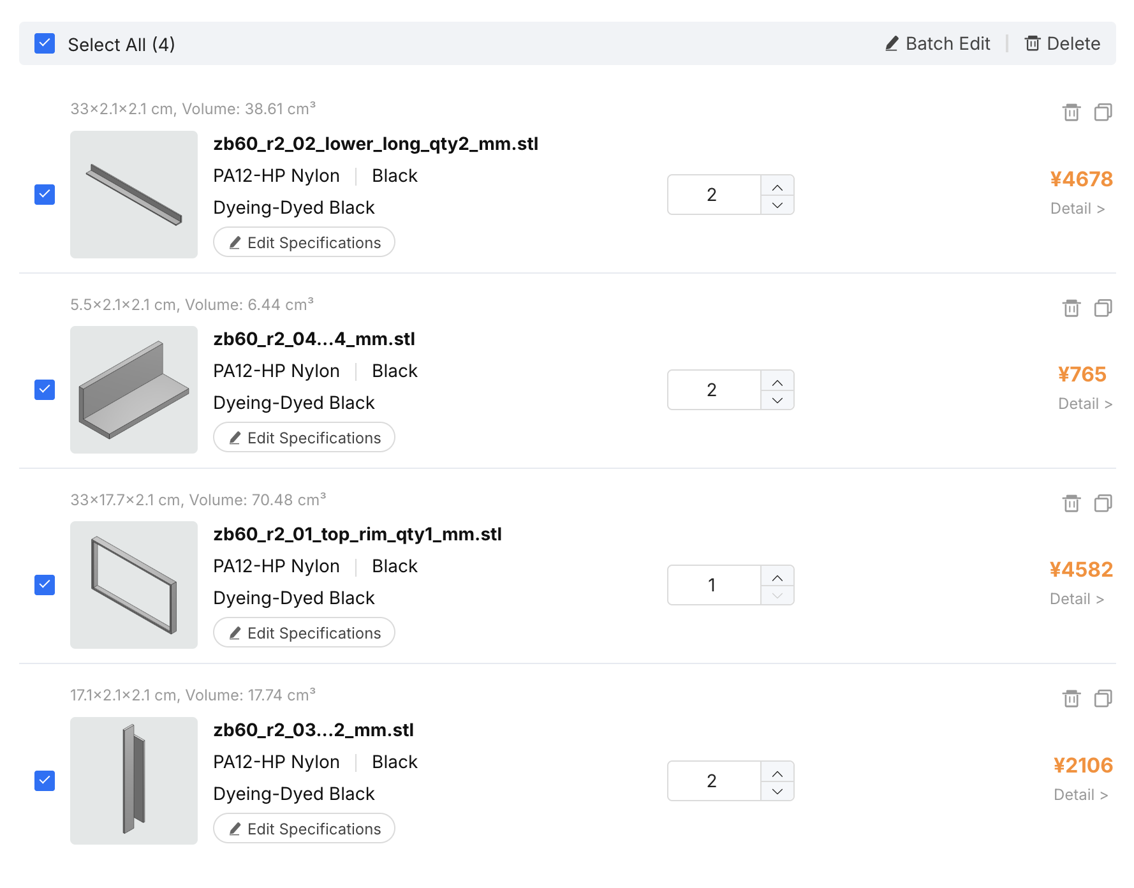
public/assets/evidence/r2-jlc-quote-incomplete-quantity.png
