Takazudo/zudo-case/public/assets/evidence/r3-jlc-quote.png

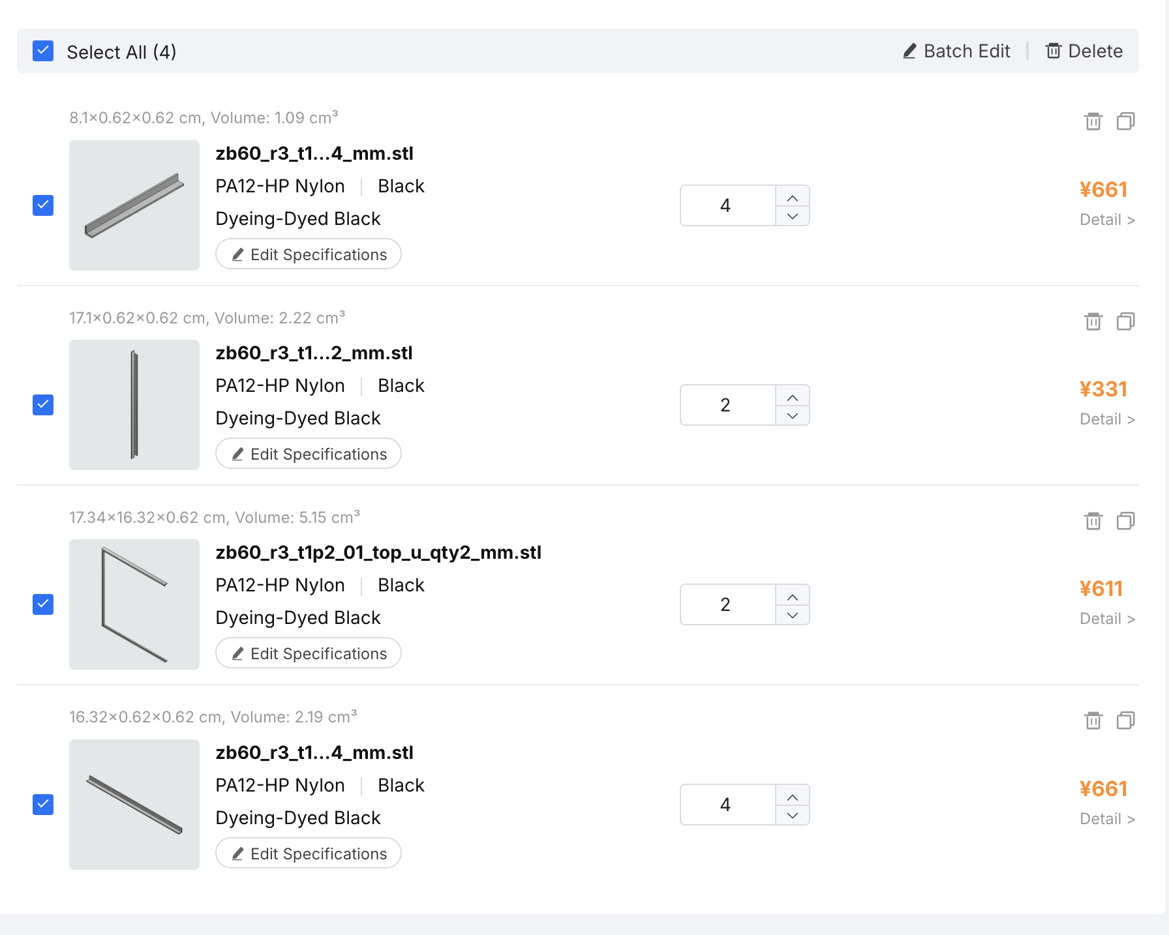
public/assets/evidence/r3-jlc-quote.png
