Takazudo/zudo-case/public/assets/images/r6/3u60-rail.png

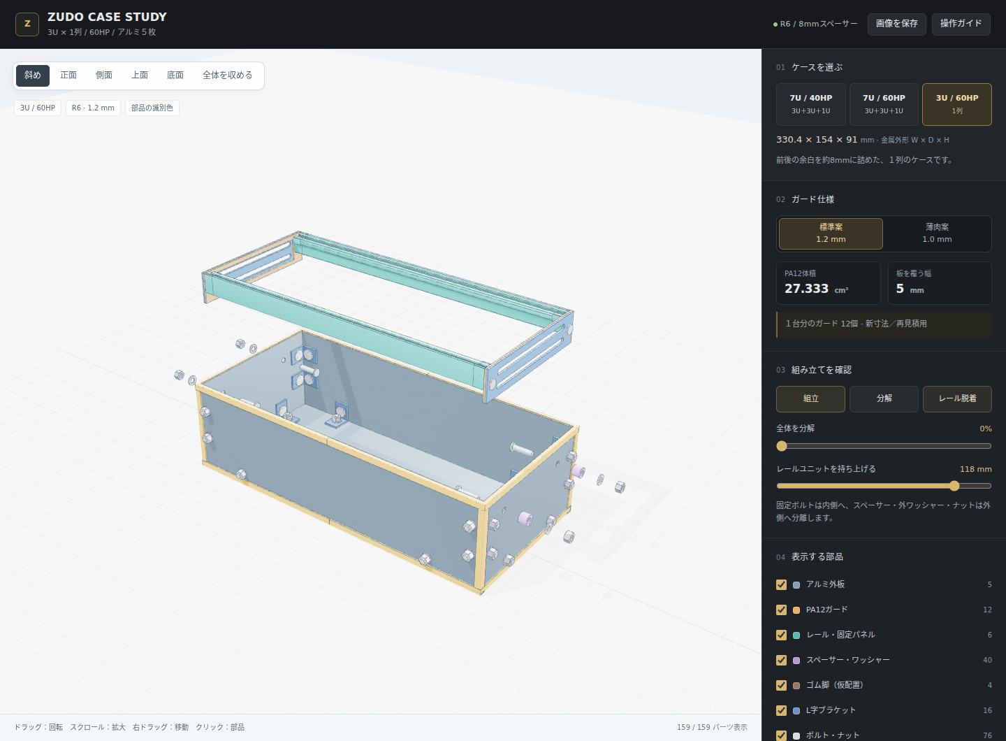
public/assets/images/r6/3u60-rail.png
