Takazudo/zudo-case/public/assets/images/r6/7u40-rail.png

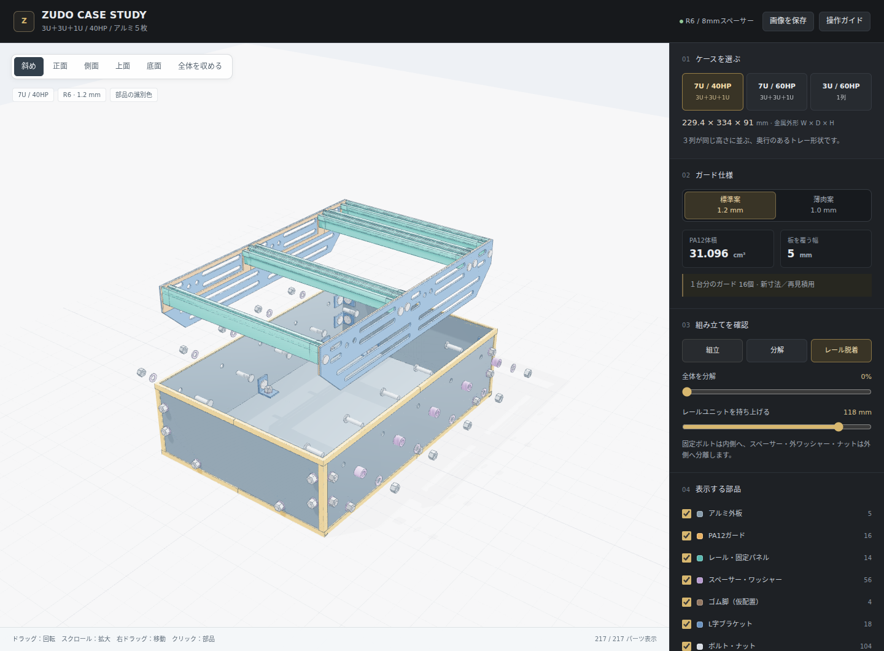
public/assets/images/r6/7u40-rail.png
