Takazudo/zudo-case/public/assets/images/r6/7u-layout.png

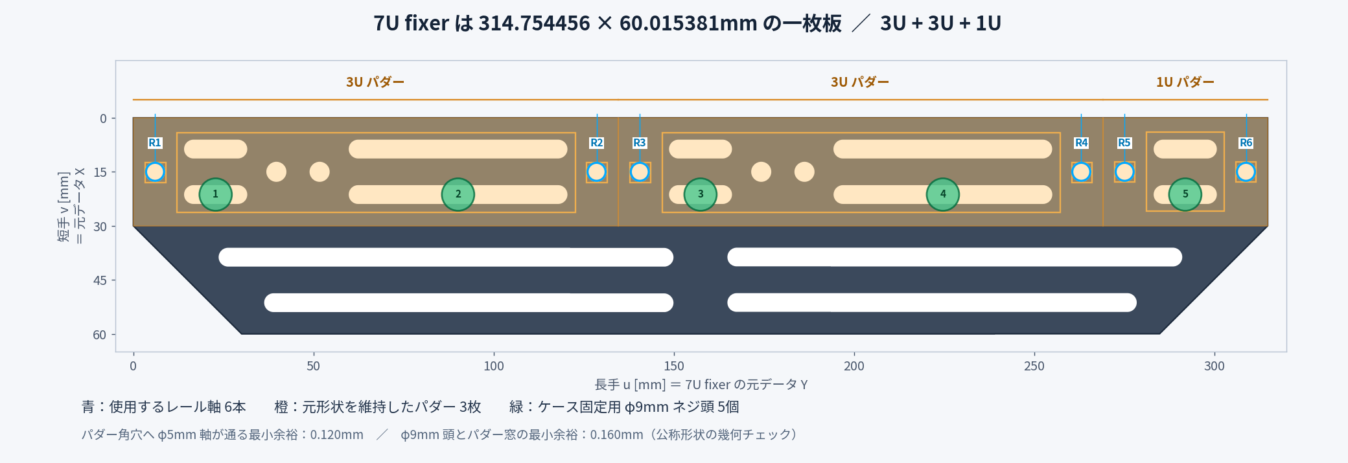
public/assets/images/r6/7u-layout.png
