Takazudo/zudo-case/public/assets/images/r8/7u40-daily.png

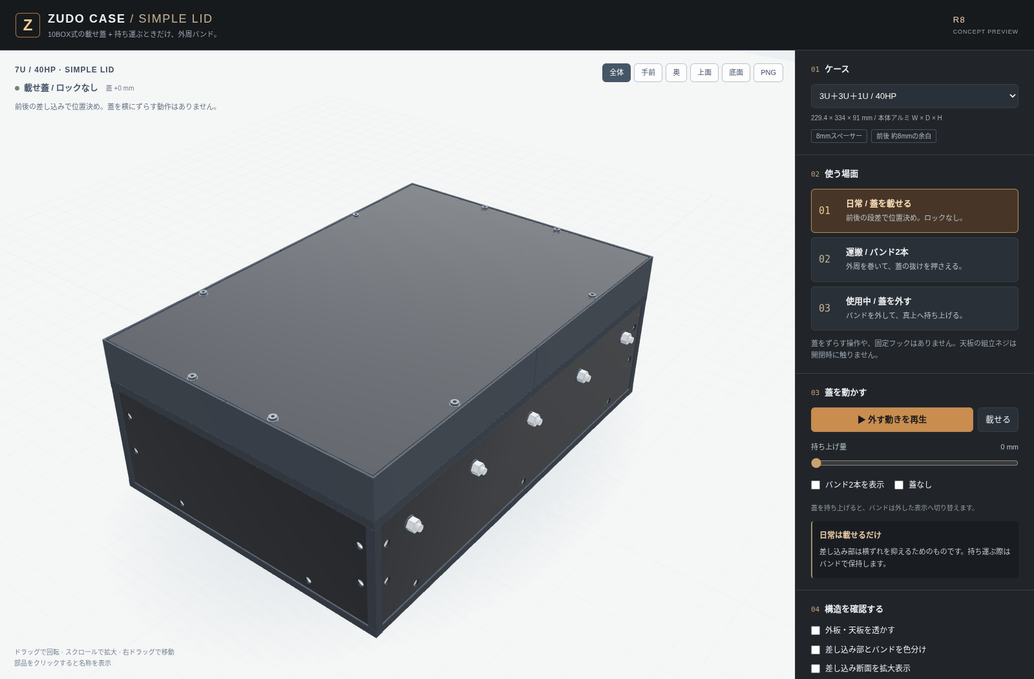
public/assets/images/r8/7u40-daily.png
