Takazudo/zudo-case/public/assets/images/r8/7u40-open.png

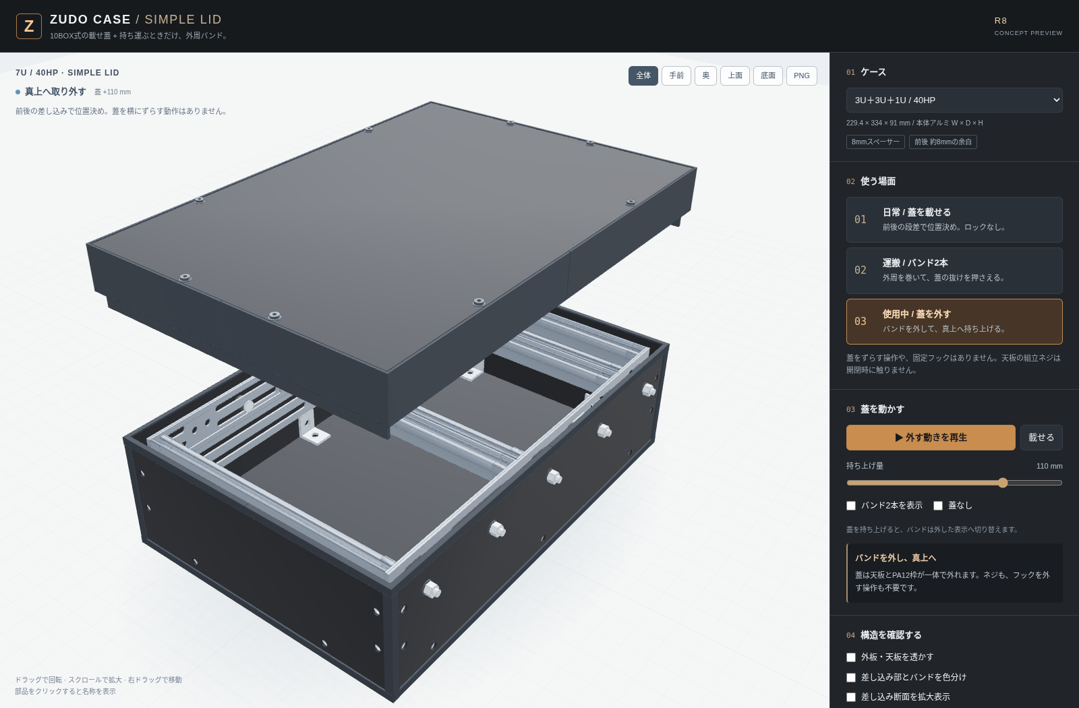
public/assets/images/r8/7u40-open.png
