Takazudo/zudo-case/public/assets/images/r8/locator-section.png

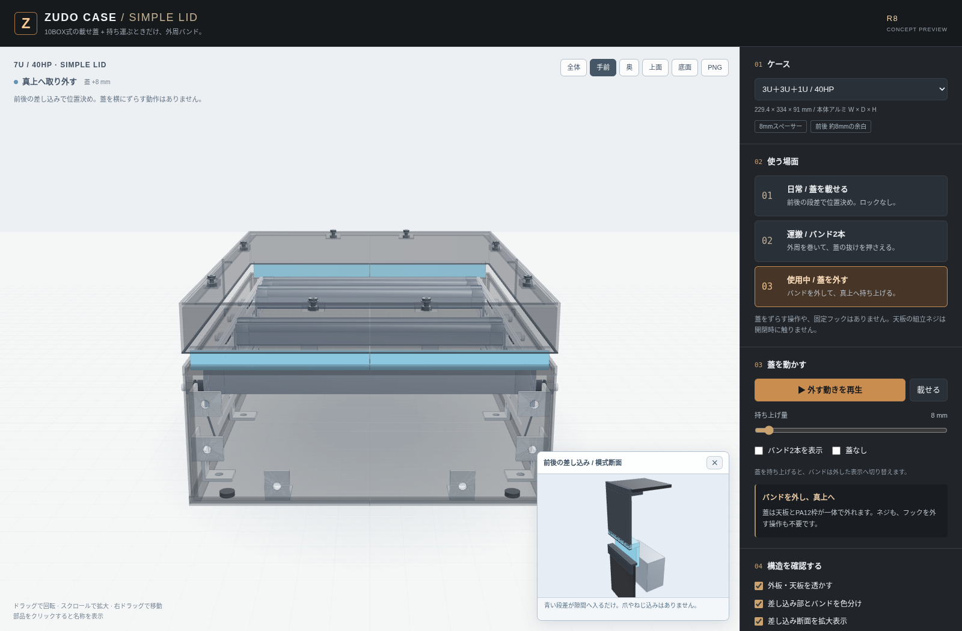
public/assets/images/r8/locator-section.png
