Takazudo/zudo-case/public/assets/images/r8/mobile.png

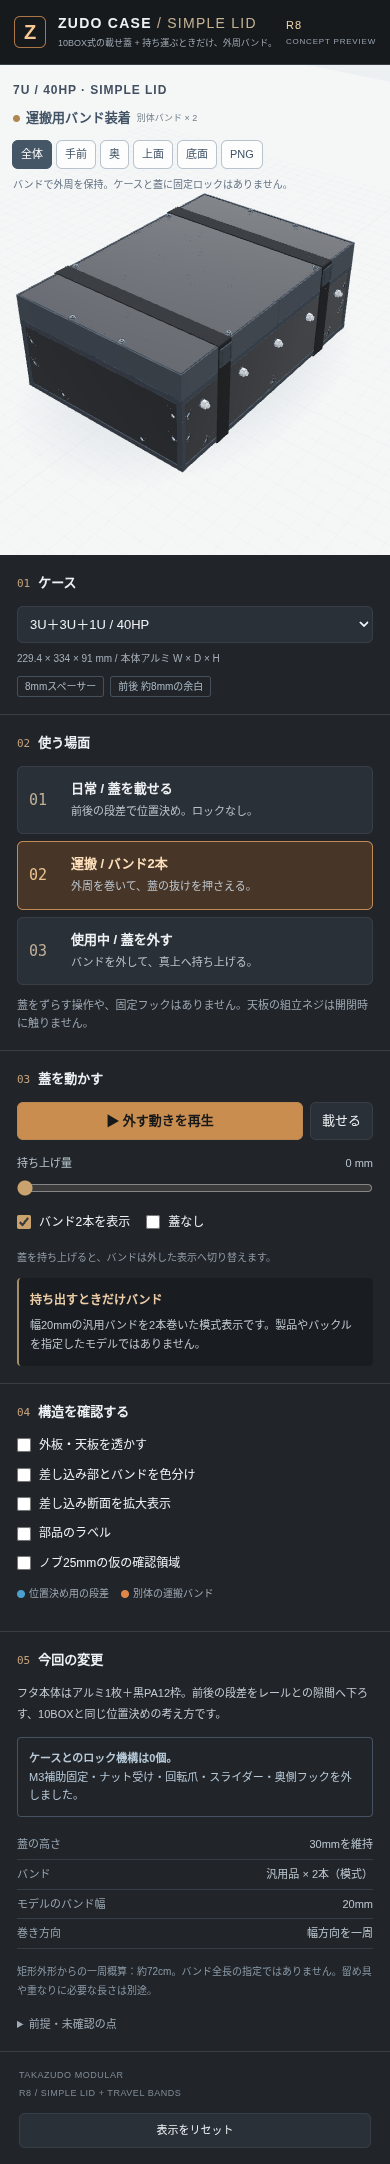
public/assets/images/r8/mobile.png
