Takazudo/zudo-case/src/content/docs/manufacturing/bom.mdx

---
title: "ケース側BOM"
description: "レールユニットの費用を除き、本体・蓋・バンドを分けて管理する。"
sidebar_position: 10
---

{/* GENERATED: node scripts/sync-reference-tables.mjs / project/current-spec.json */}

## ケース１台分の部品

以下の表はR6のhardwareCountsとR8の構成を基準に生成し、7u40のR9候補を注記したもの。予備率、破損、予備金具は含めていない。**発注承認済みBOMではなく、数量確認の起点**。

| 部品 | 3U60 | 7U40 | 7U60 | 仕様／状態 |
|---|---:|---:|---:|---|
| 本体アルミ板 | 5 | 5 | 5 | 3u60: t1.5、黒アルマイト候補；7u40: R9候補・未承認；7u60: t1.5、黒アルマイト候補 |
| L字ブラケット | 16 | 18 | 18 | 在庫20×20×16mm、厚2mm |
| 板接合用M5ネジ | 32 | 36 | 36 | 底面は頭を外向き |
| 板接合用ナット | 32 | 36 | 36 | 品番・必要ねじ長は別確認 |
| 板接合用座金 | 32 | 36 | 36 | モデル上の数量。実部品の厚さと受け面確認 |
| ユニット→ケースM5 | 4 | 10 | 10 | 頭1.4mm、軸長未確定 |
| 同ロックナット | 4 | 10 | 10 | 外側 |
| 内側8mmスペーサー | 4 | 10 | 10 | 内外径は模式値を含む |
| 外側1mmナイロン座金 | 4 | 10 | 10 | ユニット固定用 |
| ゴム脚 | 4 | 4 | 4 | φ10×高さ3mmは仮 |
| 本体PA12ガード | 12 | 16 | 16 | 3u60: 1.2mm基本、黒染め候補；7u40: R9の1.2mm候補あり。保持・黒染め未確認；7u60: 1.2mm基本、黒染め候補 |
| 蓋アルミ板 | 1 | 1 | 1 | 3u60: R8表示寸法、製作図未更新；7u40: R9で出力、嵌合未検証・未承認；7u60: R8表示寸法、製作図未更新 |
| 蓋PA12枠 | 4 | 4 | 4 | 3u60: R8の表示分割。発注数量は再CAD後に確定；7u40: R9で4部品を出力、保持未確認・未承認；7u60: R8の表示分割。発注数量は再CAD後に確定 |
| 天板の組立M3 | 8 | 8 | 8 | R7からの表示上の数量。長さ・ナット座を再確認 |
| 外周バンド | 2 | 2 | 2 | 品番未選定、開閉用のねじロックなし |

7U40の現行候補の材質別ZIP・試験片の数量は[R9-FITFIX-01](../design/r9-fitfix-01.mdx)を参照。1.2mm/1.0mmの蓋は専用で、C2の再利用部材（order_quantity=0）は重複発注しません。

## レール費用の除外

レール、fixer、padder、レール端固定ネジ、モジュール用ナット等のレールユニットの製作費は計算に入れない。数量の参考として、3Uはレール２本/fixer２枚/padder２枚、7Uはレール６本/fixer２枚/padder６枚をモデルに含む。

## まだ数量を確定しないもの

蓋組立用のナット・座金、ガード保持の接着材や爪、当たり材、バンド位置決め、梱包などは最終設計/品番が未確定。R7にあった蓋→本体のM3４本、ナット受けと圧縮スペーサー４個は最終方式には不要。

## 在庫と費用

手持ちL字金具は追加支払0円でも、製品原価には使用数×実仕入単価を入れる。その他の小物も画面上の形状から品番を推測して買わない。ケース側のM5で使う8mmスペーサーと外側座金はレール費用除外とは別に計上する。

出典：[R6サマリー](/evidence/r6-family-summary.json)、各機種のmodel-summary.json、<a href="/evidence/r8-original-readme.md">R8 README</a>。
