Takazudo/zudo-case/src/content/docs/manufacturing/fit-test-order.mdx

---
title: "小型試験片の見積・発注準備"
description: "R9-FITFIX-01の材質別数量、未送信文案、乾式試験の進め方。"
sidebar_position: 27
---

**小型試験片の見積用セットを準備済み。未送信・未発注。** ケース全体の製造承認とは別に、嵌合を調べる試験片の数量と添付をまとめた。

<PreviewLink path="/downloads/candidate/fit-test-order-pack-DRAFT.zip">見積準備セットをダウンロード（文案・数量・材質別CAD ZIP・試験手順）</PreviewLink>

## 用意した１セット

| 区分 | 依頼条件 | 種類 | 実際の個数 |
|---|---|---:|---:|
| C1/C2/C4/C5・PA12 | MJF PA12-HP、黒染め依頼 | 13 | 15 |
| 共用治具・対向板のアルミ | A5052、t1.5、バリ取り、黒アルマイト依頼 | 7 | 7 |
| C3の別見積オプション | 同じアルミ条件、底と壁を３組 | 6 | 6 |

C1-06/07だけPA12各２個、他は各１個。STLは１個の形状なので注文画面で数量を指定する。アルミのSTEP/DXFは同じ１枚の別形式で、重複注文しない。C2-02/03では01の壁・ガード・天板を使い回す。

C3は元のR9-PROTOTYPE-01からハッシュ照合して抽出した追加試験片。C3-01は5.5×7.5mm長穴、02は5.5×8.5mm長穴、03はφ5.5mm丸穴の対照。ガード修正版と同じ版名に付け替えず、別ZIP・別価格にした。丸穴を採用へ戻すものではない。

## 業者への依頼案

PA12の候補先はJLC3DP。アルミはJLCCNCまたは指定板金業者。ZIP内の英語文案は加工可否と見積の依頼用で、まだ送っていない。送り先を含む送料・税、納期、材質と仕上げの部品別受入確認、C3追加費用が必要。

2026-09-30に[JLC3DPの材質条件](https://jlc3dp.com/help/article/pa12-hp-nylon)でMJF、肉厚1mm、100mm以下で±0.3mmの掲載を確認した。これは個別部品の製造承認ではない。1.0mm比較片、細い識別文字、黒染めと寸法への影響を依頼文で確認する。

[JLCCNCの板金条件](https://jlccnc.com/sheet-metal-fabrication)には5052、1.5mm板、アルマイトが掲載される。一方、10.5×20mm等の小片の保持・バリ取り・黒アルマイトが可能かは業者回答待ち。キャリアや寸法変更が必要なら、形状を勝手に修正せず提案を受けて確認する。

既存の適合するアルミ端材があれば乾式予備試験に使える。ただし仕上げや板厚が異なる結果を、製品条件の嵌合・接着結果に読み替えない。

## 到着後に行うこと

まず全比較片を乾式で測定・着座・着脱する。C1の片側空間は0.15〜0.40mm、C2は0.5/0.7/0.9mmの候補なので、公開公差より小さい差がある。実測値と挙動を合わせて判断し、比較が不明瞭なら複製を追加する。公称寸法のID順だけで合否を決めない。

C4/C5は直角治具で金属板の実配置を保持して確認する。ガードを治具代わりに押し込んで板位置を変えない。C3では実在庫金具・実締結材・実工具を使い、可動範囲、座金受け面、締付後のずれを記録する。

接着は全ての乾式比較の後。実測空間を充填し、黒染めPA12とアルマイトの両面に適した製品を選ぶ。0.15mmテープを自動的に選定しない。M3/M5のねじ長・ナット・座金も実寸から選ぶ。複数接着剤での破壊試験用の追加個数は、このセットに含まない。

詳しい手順と未記入記録票をZIPに含めた。[試験片記録票](../verification/coupon-record.mdx)と[候補プレビュー](../design/r9-fitfix-01.mdx)を併用する。

## 支払前に残るもの

- 業者のファイル別加工可否、材質・仕上げ・最終公差の回答。
- 送り先に基づく税送料込み金額、納期、C3を追加するか。
- 対象ZIPと個数を含む、有償試験注文の承認。

接着剤の最終選定や全体の運搬試験の完了を、乾式試験片を作る前提にはしない。小型片の結果をもとに１台試作を検討し、長部品の反り・実ノブ・バンドと運搬はそこで確認する。
