Takazudo/zudo-case/src/content/docs/manufacturing/aluminum-order.mdx

---
title: "アルミ板の見積・発注条件"
description: "黒アルマイトまで材料込みで比較し、長穴と仕上げを図面へ結び付ける。"
sidebar_position: 20
---

7U40の現行候補は[未承認R9アルミZIP](../design/r9-prototype-01.mdx)。１/10/50セットの比較条件と送信前に埋める項目は[未送信RFQ文案](./r9-rfq-draft.mdx)にまとめた。現行の業者見積と製作承認はない。下記R6丸穴ZIPと古い送信文は履歴資料として読む。

## 調達候補

これまでの第一候補は**JLCCNCの板金加工へ、材料＋外形＋穴＋バリ処理＋黒アルマイトをまとめて依頼する**方法。比較先としてタカチB2Fと国内板金会社、素材価格の基準として横山テクノの切板を挙げていた。

ただし、この３機種の最終図に対する業者見積はまだない。候補のサービスページは[調達先一覧](./bands-suppliers.mdx)にまとめた。今回、新しい価格・納期・対応可能公差を取得していない。

## 同じ条件で見積もる項目

| 項目 | 現状の指定／確認事項 |
|---|---|
| 数量 | 試作１台、比較用10台／50台。各機種を分ける |
| 材質 | A5052が候補。A1100Pへの無断置換はしない |
| 厚さ | 1.5mm |
| 外形 | 機種別の底１、前後２、左右２。蓋は追加１ |
| 加工 | 直線外形、取付穴、長穴。曲げ加工なし |
| 穴 | M5は通し穴/長穴。タップ穴と区別 |
| 外観 | 黒アルマイト。黒PA12との組合せを現物確認 |
| 端面 | バリ取り。手が触れる端の仕上げ条件を合意 |
| 表面 | 許容傷、色差、吊り跡、切断面/穴内面の仕上がりを確認 |
| 費用 | 材料、加工、表面処理、送料、税、検査、梱包を分ける |

長穴はユーザーが公差吸収を目的に要求している。R6の丸穴DXFをそのまま最終図としない。またR7の蓋補助固定用M3穴は、最終載せ蓋方式には不要。

## 業者へ渡すパッケージの形

承認図の版番号、単位mm、板ごとの数量、部品名、STEP、DXF、説明PDF等を同じセットにする。STLは金属外形の唯一のマスターにしない。どの形式を業者が要求するかを確認する。

本資料の`reference/*-r6-aluminum-NOT-RELEASED.zip`は、**寸法と形状の相談用**。長穴・穴中心が未確定なので製作承認の指示は付けない。

## 送信文のたたき台

```text
添付は黒アルマイト仕上げの平板アルミケースの見積検討用です。
材質候補A5052、板厚1.5mm、曲げなしです。
部品ごとの必要数量と図面版は添付の部品表に記載しています。

外形切断、通し穴/長穴、バリ取り、黒アルマイト、梱包・送料について、
試作1台分と10台/50台分の単価・初期費用・納期を分けてご提示ください。
切断端・穴内面の仕上がり、表面の許容傷、公差の標準条件も確認したいです。

現段階は見積・製作性確認です。製造開始の承認は別途連絡します。
```

[発注前ゲート](../verification/before-order.mdx)と[見積の記録方法](./costs.mdx)を併用する。
