Takazudo/zudo-case/src/content/docs/manufacturing/costs.mdx

---
title: "見積・概算・未取得費用"
description: "実額を確認できるのは旧R3ガード。現在の総原価は未確定。"
sidebar_position: 40
---

## 実際の見積画面

R3・1.2mm、本体ガード12個をJLC3DPへ投入したユーザーの画面では、PA12-HP Nylon／黒染めで次の金額が表示された。

| 部品 | 数量 | 行の金額 |
|---|---:|---:|
| 縦辺 | 4 | 661円 |
| 左右下辺 | 2 | 331円 |
| 上端U字 | 2 | 611円 |
| 前後下辺・半分 | 4 | 661円 |
| **合計** | **12** | **2,264円** |

R3で数量を揃えた見積画面

この2,264円は旧形状の表示合計であり、R6の３機種、R8の蓋、運搬バンド、送料を含まない。税の扱いはこの画面だけでは確定できない。表示額を勝手に税込・税抜へ置き換えない。

[R2画面](/assets/evidence/r2-jlc-quote-incomplete-quantity.png)は縦辺が２個で不足していた。約12,131円という画面合計を、数量一致の比較に使わない。

## 過去に提示した切板価格

以下は**過去回答が報告した数値**で、業者見積書や保存済み注文HTMLが今回の資料にはない。旧324×171×91mm級の寸法、穴加工なし、送料別。新寸法や長穴加工込みの確定価格ではない。

| 仕様 | 1台分 | 10台時／台 | 50台時／台 |
|---|---:|---:|---:|
| A5052・無処理1.5mm切板５枚（横山テクノ） | 3,280円 | 約3,231円 | 約3,069円 |
| A1100P・黒アルマイト1.5mm５枚（タカチB2F） | 8,294円 | 7,007円 | 6,589円 |

過去回答では税込と記載していた。A5052とA1100Pは別材質であり、２行の差額を「同じ板のアルマイト工賃」としない。既出のアルマイト差額約1,600〜2,000円も、別商品仕様の比較である。

## 直近に提示された本体予算の履歴

| モデル | 過去回答の１台予算 |
|---|---:|
| 3U60 | 11,000〜13,000円 |
| 7U40 | 14,000〜17,000円 |
| 7U60 | 17,000〜21,000円 |

**これは過去の助手の予測で、見積ではない。** 面積比によるアルミ推定とガード体積比などを使い、穴加工込みという説明もあったが、穴加工の実額を取得していない。税・在庫金具・小物の扱いも再整理が必要なので、この範囲を発注上限や販売原価へ確定しない。

過去の10台／50台予測も、板単価の傾向を横展開したものであり、３機種の数量見積を取ったわけではない。

## 今回の最終方式で取り直す合計

`加工済み本体アルミ５枚 + 天板１枚 + 本体PA12 + 載せ蓋PA12 + 締結小物 + ゴム脚/当たり材 + バンド２本 + 送料・税等`

既存在庫のL字金具は追加支払では0円でも、製品原価では使用個数×仕入単価を足す。組立工賃、梱包、検査、失敗・予備率をどこまで含むかを明記する。レールユニットの製作費は依頼どおり除外する。

**R9 7U40の蓋候補CADはあるが現行見積がないため、蓋付き総原価は未確定。** 未取得費用を0円で集計しない。

## 価格台帳

機械可読な台帳は`project/quote-records.json`。値を更新する場合、版、数量、税送料、日時、画面/見積書、ファイルハッシュをセットで記録する。現段階の現在額（全体・蓋・バンド）は`null`。相見積を保存しても採用前は現在額を`null`にし、対応する範囲も`null`または省略とする。採用時は`current_*_scope`へ機種・版・数量・`price_basis`（１台あたりの`per_unit`／対象数量合計の`lot_total`）・税送料条件と`quote_ids`を記し、条件が一致する選択見積だけを合算する。条件の換算は行わず、異なる条件は別見積として比較する。複数選択には部品・数量の非重複を説明する`coverage_note`が必要。同じ`rows[].part`ラベルは拒否するが、意味上の非重複までは検査で証明できない。[登録と選択の手順](../handoff/maintenance.mdx)を参照する。

[見積依頼の条件](./aluminum-order.mdx)／[最新STL投入の方法](./print-order.mdx)。
