Takazudo/zudo-case/src/content/docs/verification/before-order.mdx

---
title: "発注前ゲート"
description: "発注の直前に、仕様・図面・実物の一致を確認する。"
sidebar_position: 10
---

## 現在の承認状態

**量産製作を承認したファイルは0件。** 見積依頼と製造開始の承認は分ける。試作のために未確定データを送る場合も、その範囲と目的を明記する。

| ID | 未完了の項目 | 完了の証拠 |
|---|---|---|
| G01 | R8載せ蓋の再CAD化 | 単純な段差のSTL/STEP、蓋板DXF、旧ロック部除去、版とハッシュ |
| G02 | 本体長穴 | 向き・寸法・基準穴・調整範囲、代表金具での組立結果 |
| G03 | 本体ガードの嵌合・保持 | 実材料の短い試験片と、採用したクリアランス/保持条件 |
| G04 | 蓋の差し込み・バンド | まっすぐ開閉でき、締付でノブに当たらず、ずれ・抜けを許容範囲に収める |
| G05 | 実際のノブ/スイッチの高さ | 搭載モジュールの最大高さと蓋下面の距離 |
| G06 | 締結材の品番・寸法 | 頭径、軸長、座金、ナットの整合。干渉と掛かりを確認 |
| G07 | 金属材・加工・黒仕上げ | 仕様付き見積、仕上げサンプル、確認した公差 |
| G08 | 脚・内装 | 圧縮時の接地、電源・配線・基板の金属接触対策 |
| G09 | バンド選定 | 使用可能長さ、２本の位置、バックル/横滑り/突出の確認 |
| G10 | 最新原価 | 同じ版・数量で取得したアルミ、樹脂、小物、バンド、税送料 |
| G11 | 組立・搬送・最終承認 | 試験条件、結果、確認者、承認日、製作パッケージ |

## 順序

まずG01〜G03で図と嵌合を決め、G05〜G07を合わせる。次に本体＋蓋＋実モジュールでG04/G08/G09を確認し、最終図でG10を取る。G11の承認前に「完成」「量産可」を表示しない。

これは進行の提案であり、各ゲートの実施日・担当者はまだ決めていない。`project/open-issues.json`に結果・担当・資料を追記して使う。

試作に進むときは[嵌合試験](./fit-test.mdx)、全体確認は[組立・運搬試験](./assemble-test.mdx)へ。
