Takazudo/zudo-case/engineering/order-map/verification/order-map-C1-390.png

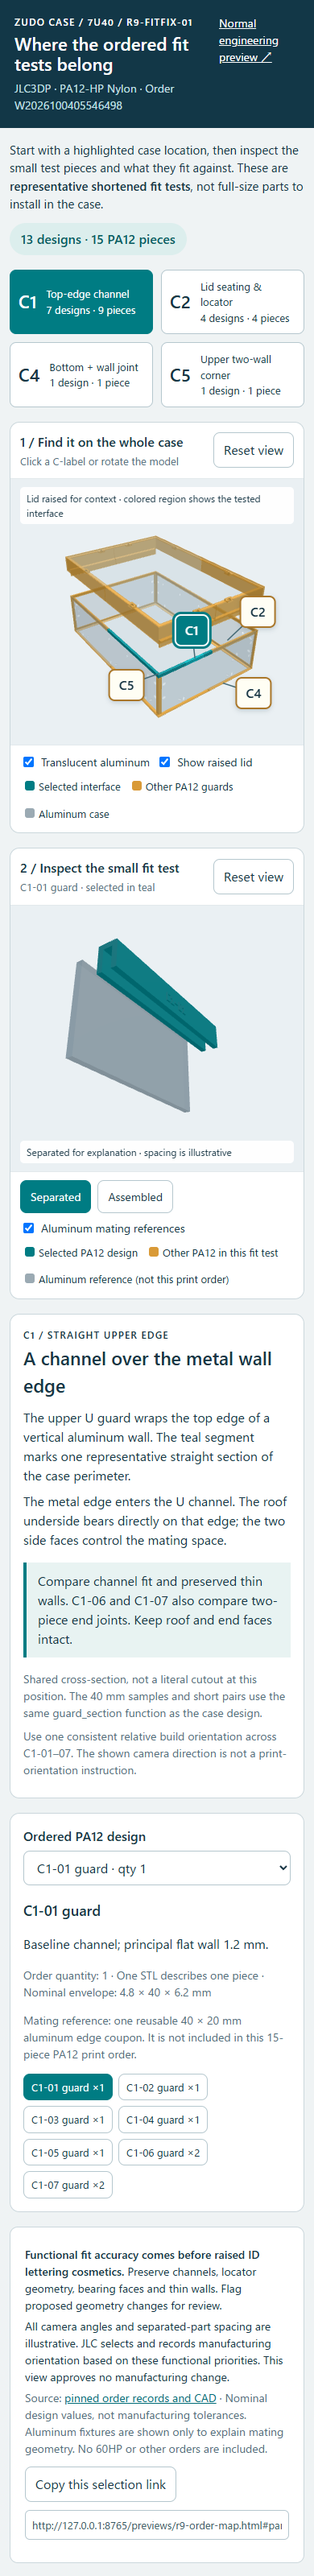
engineering/order-map/verification/order-map-C1-390.png
