Takazudo/zudo-case/engineering/order-map/verification/order-map-C1-1440.png

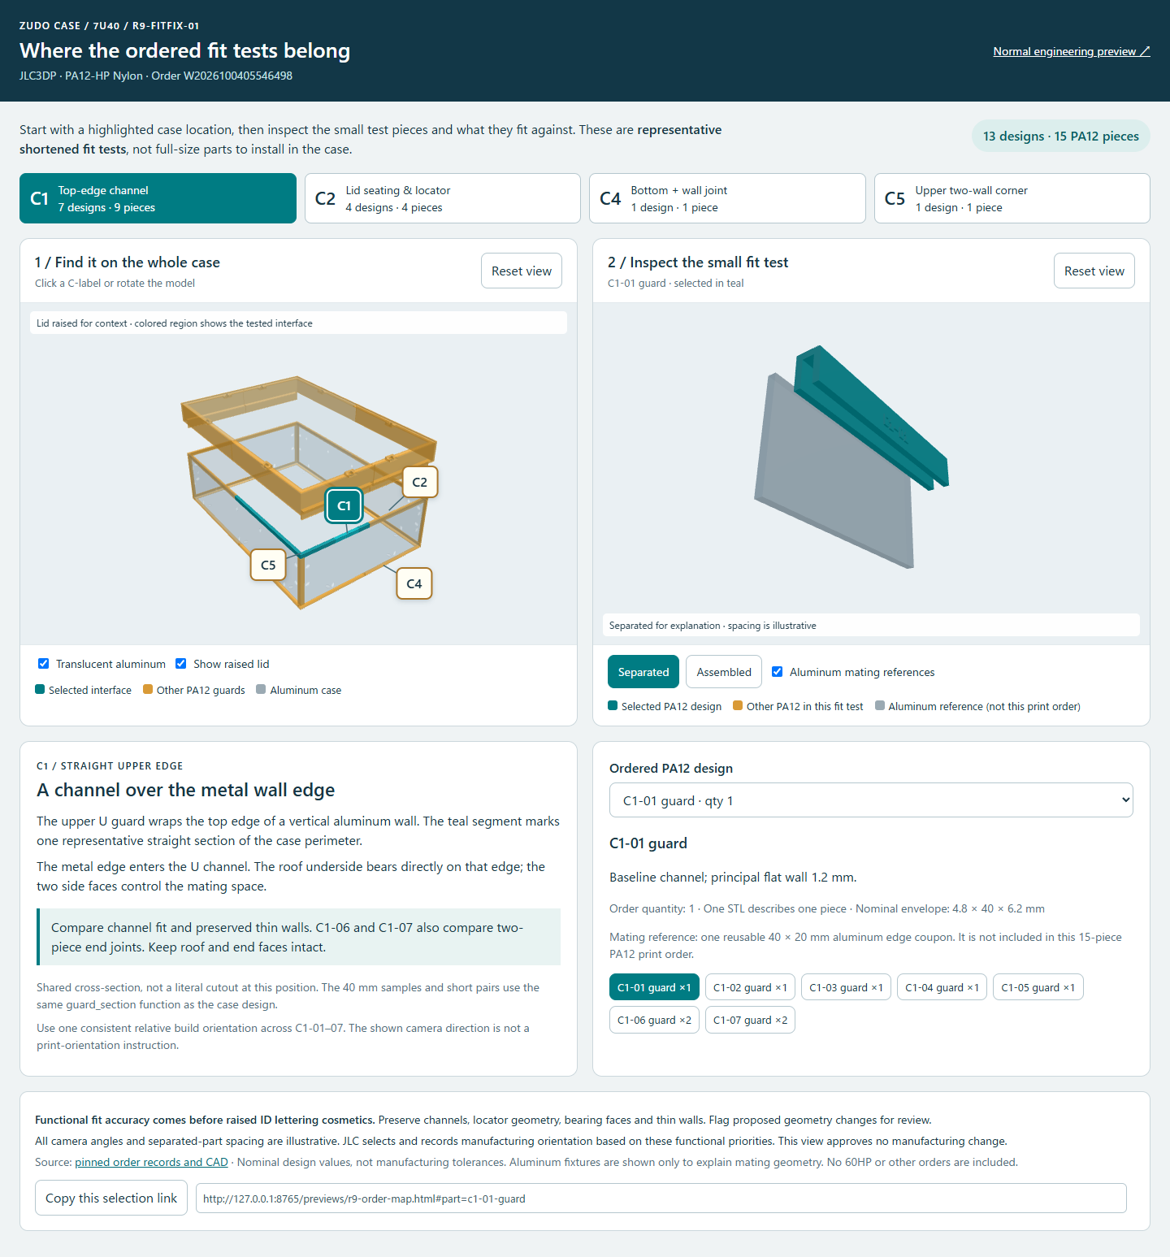
engineering/order-map/verification/order-map-C1-1440.png
