Takazudo/zudo-case/engineering/r6-body/engineering/7u60/guards/7u60_r6_t1p0_04_lower_depth_half_a_qty2_mm.step

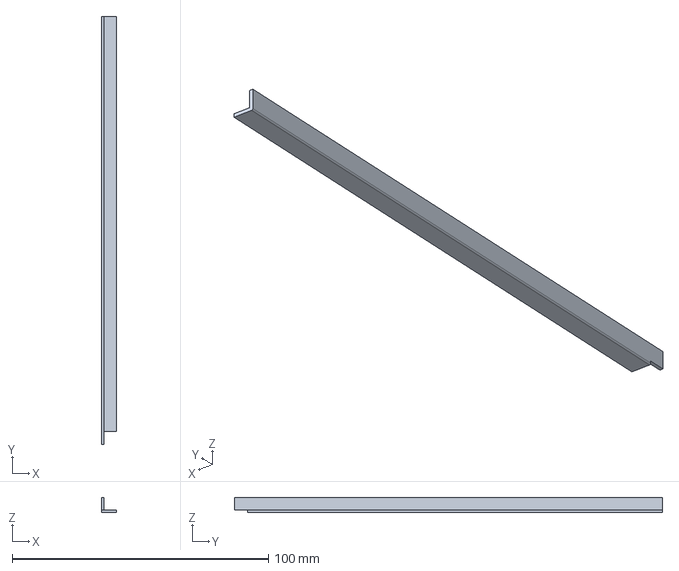
[picture p46: CAD file, 2026-09-24]
engineering/r6-body/engineering/7u60/guards/7u60_r6_t1p0_04_lower_depth_half_a_qty2_mm.step
6.00 x 167.0 x 6.00 mm
