Takazudo/zudo-case/engineering/r6-body/engineering/7u60/pcbs/7u60_r6_fixer-1_source_outline_mm.step

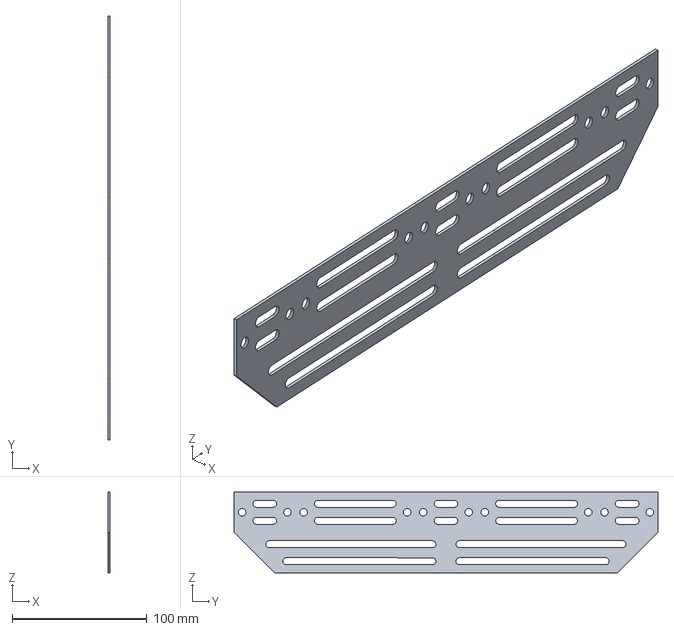
[picture p47: CAD file, 2026-09-24]
engineering/r6-body/engineering/7u60/pcbs/7u60_r6_fixer-1_source_outline_mm.step
1.60 x 314.8 x 60.0 mm
