Takazudo/zudo-case/engineering/r6-body/source-data/rail40/nuts-v2-40hp-single.stl

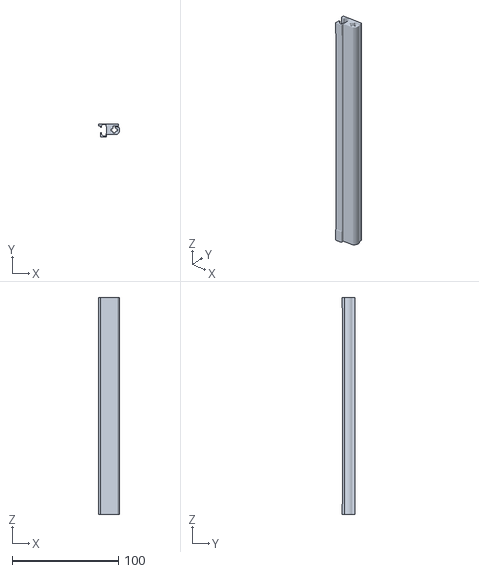
[picture p48: CAD file, 2026-09-24]
engineering/r6-body/source-data/rail40/nuts-v2-40hp-single.stl
20.1 x 12.6 x 204.0
