Takazudo/zudo-case/engineering/r6-body/source-data/rail60/nuts-v2-60hp-single.stl

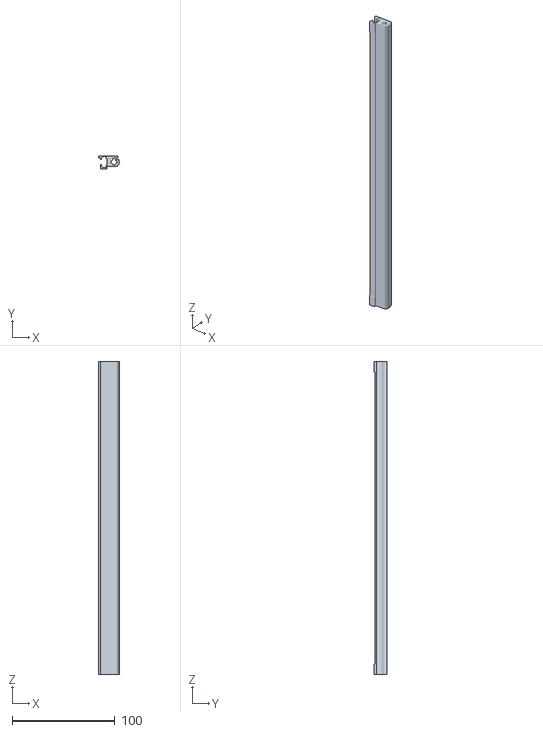
[picture p49: CAD file, 2026-09-24]
engineering/r6-body/source-data/rail60/nuts-v2-60hp-single.stl
20.1 x 12.6 x 305.0
