Takazudo/zudo-case/engineering/r6-body/stl/7u40/t1p0/7u40_r6_t1p0_02_top_corner_b_qty2_mm.stl

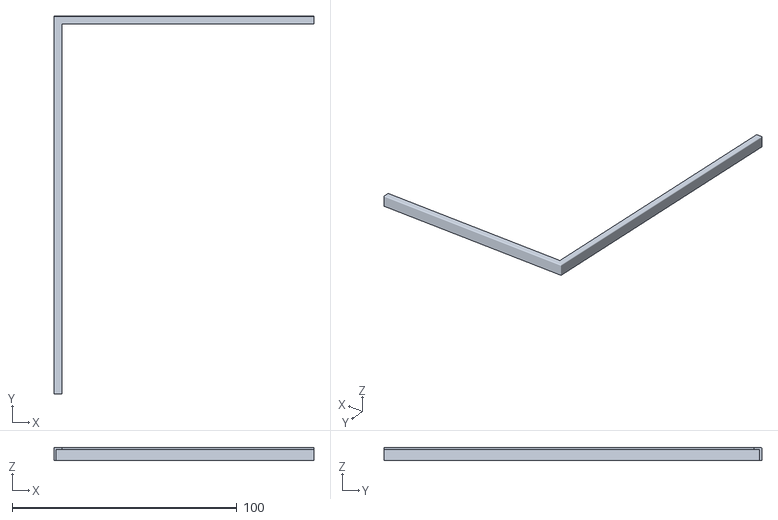
[picture p50: CAD file, 2026-09-24]
engineering/r6-body/stl/7u40/t1p0/7u40_r6_t1p0_02_top_corner_b_qty2_mm.stl
115.7 x 168.0 x 6.00
