Takazudo/zudo-case/engineering/r6-body/stl/7u40/t1p2/7u40_r6_t1p2_03_lower_width_half_qty4_mm.stl

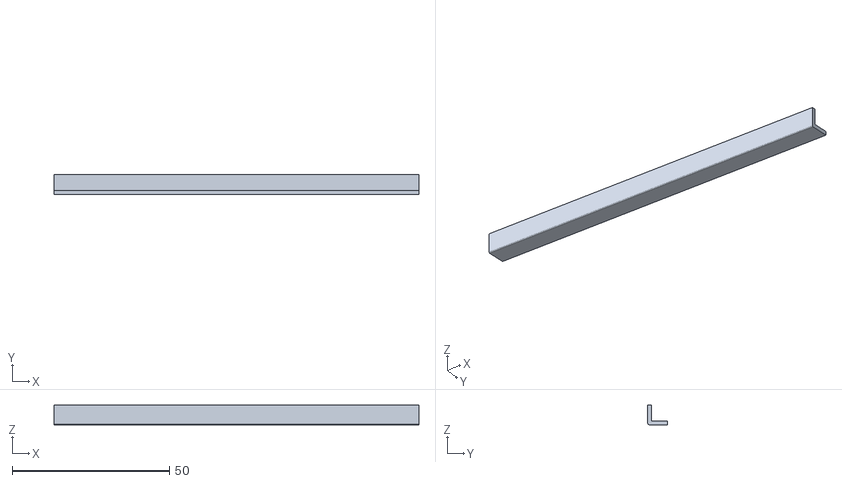
[picture p51: CAD file, 2026-09-24]
engineering/r6-body/stl/7u40/t1p2/7u40_r6_t1p2_03_lower_width_half_qty4_mm.stl
115.9 x 6.20 x 6.20
