Takazudo/zudo-case/engineering/r6-body/stl/7u60/t1p2/7u60_r6_t1p2_02_top_corner_b_qty2_mm.stl

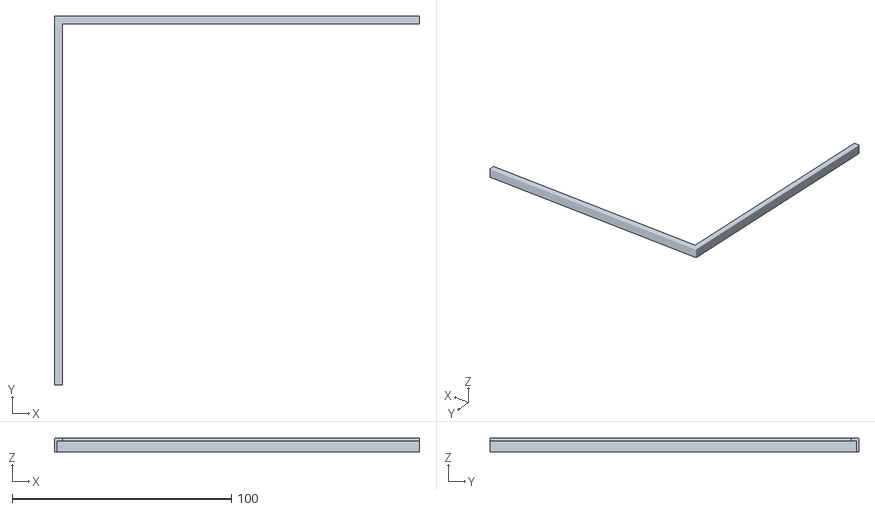
[picture p52: CAD file, 2026-09-24]
engineering/r6-body/stl/7u60/t1p2/7u60_r6_t1p2_02_top_corner_b_qty2_mm.stl
166.4 x 168.2 x 6.20
