Takazudo/zudo-case/engineering/r9-anodizing-01/out/reference-stl/7u40-r9a-c4-01-wall-qty1-mm.stl

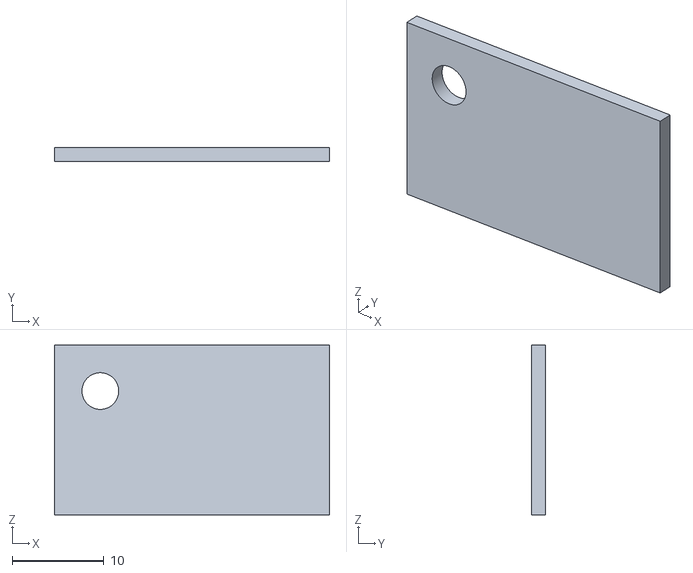
[picture p53: CAD file, 2026-10-06]
engineering/r9-anodizing-01/out/reference-stl/7u40-r9a-c4-01-wall-qty1-mm.stl
30.0 x 1.50 x 18.5
