Takazudo/zudo-case/engineering/r9-anodizing-01/out/step/7u40-r9a-c5-01-left-qty1-mm.step

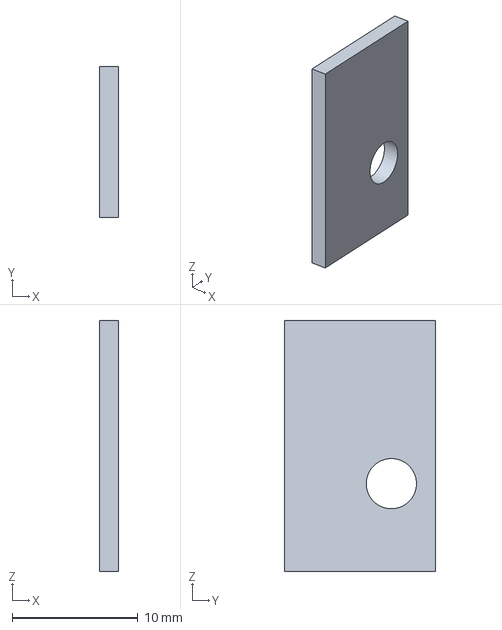
[picture p54: CAD file, 2026-10-06]
engineering/r9-anodizing-01/out/step/7u40-r9a-c5-01-left-qty1-mm.step
1.50 x 12.0 x 20.0 mm
