Takazudo/zudo-case/engineering/r9-fitfix-01/out/aluminum/t1p0/7u40-r9f-lid-plate-qty1-mm.step

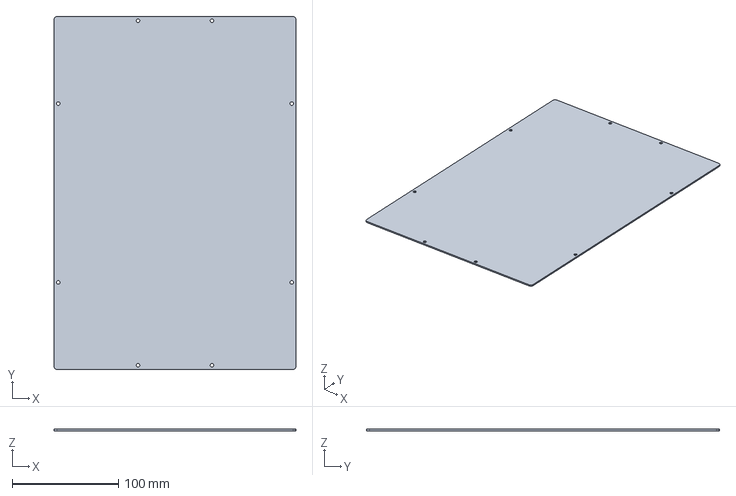
[picture p55: CAD file, 2026-09-30]
engineering/r9-fitfix-01/out/aluminum/t1p0/7u40-r9f-lid-plate-qty1-mm.step
227.8 x 332.4 x 1.50 mm
