Takazudo/zudo-case/engineering/r9-fitfix-01/out/coupons/c1-02/7u40-r9f-c1-02-guard-qty1-mm.step

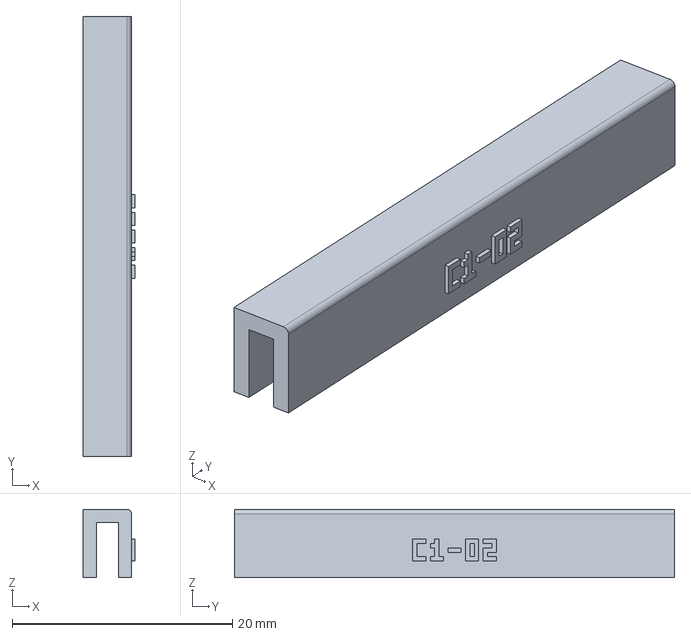
[picture p57: CAD file, 2026-09-30]
engineering/r9-fitfix-01/out/coupons/c1-02/7u40-r9f-c1-02-guard-qty1-mm.step
4.70 x 40.0 x 6.20 mm
