Takazudo/zudo-case/engineering/r9-fitfix-01/out/coupons/c1-03/7u40-r9f-c1-03-guard-qty1-mm.step

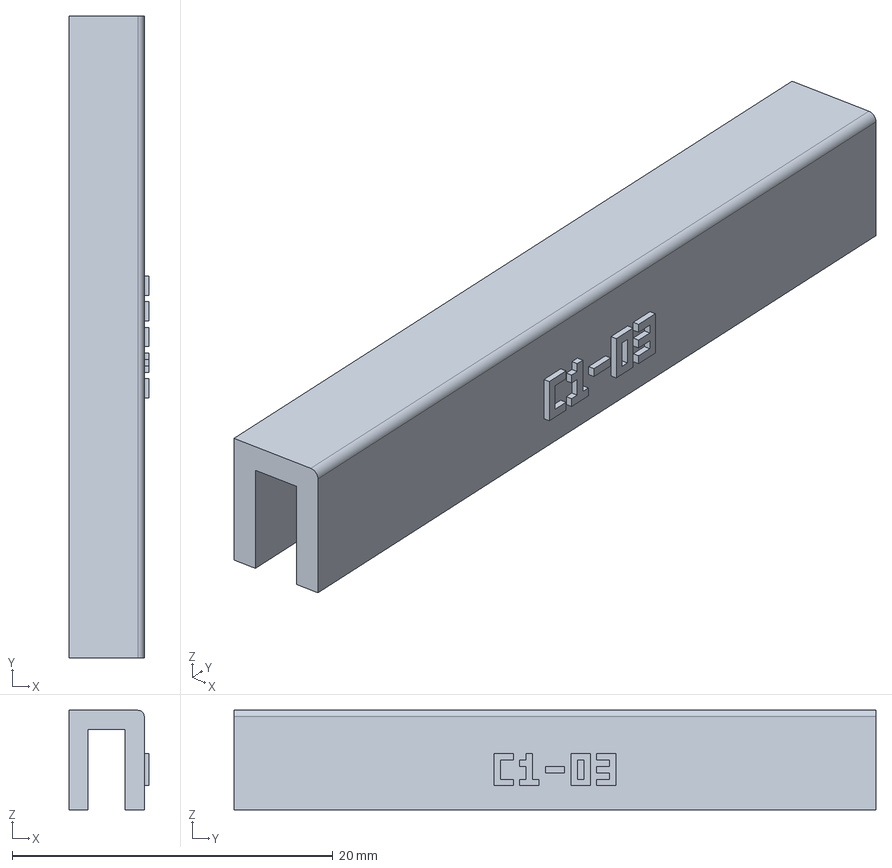
[picture p58: CAD file, 2026-09-30]
engineering/r9-fitfix-01/out/coupons/c1-03/7u40-r9f-c1-03-guard-qty1-mm.step
5.00 x 40.0 x 6.20 mm
