Takazudo/zudo-case/engineering/r9-fitfix-01/out/coupons/c1-05/7u40-r9f-c1-05-guard-qty1-mm.step

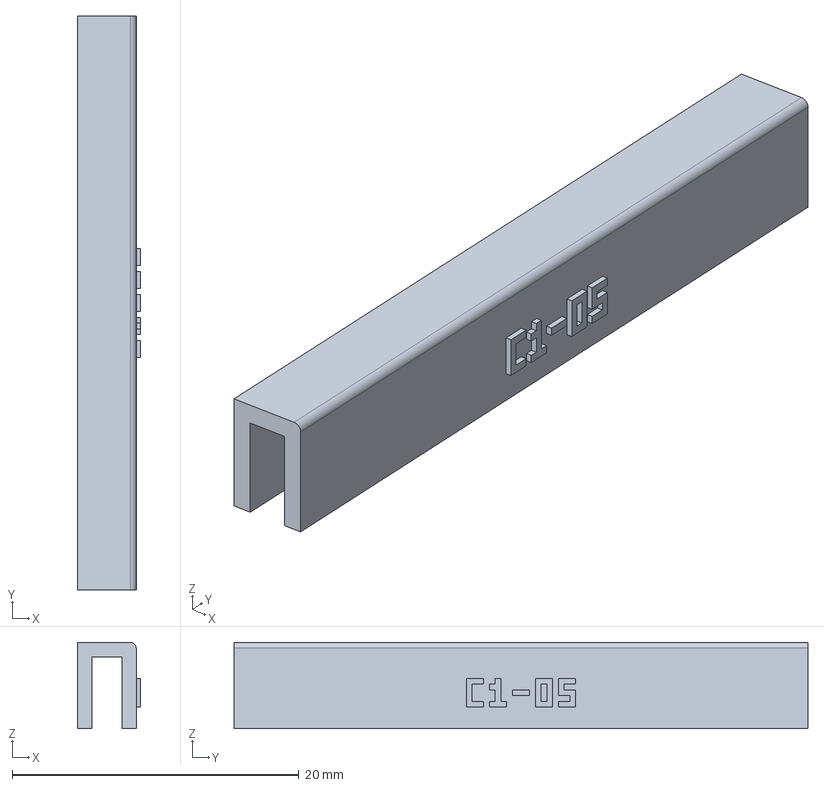
[picture p60: CAD file, 2026-09-30]
engineering/r9-fitfix-01/out/coupons/c1-05/7u40-r9f-c1-05-guard-qty1-mm.step
4.40 x 40.0 x 6.00 mm
