Takazudo/zudo-case/engineering/r9-fitfix-01/out/coupons/c1-06/7u40-r9f-c1-06-guard-qty2-mm.step

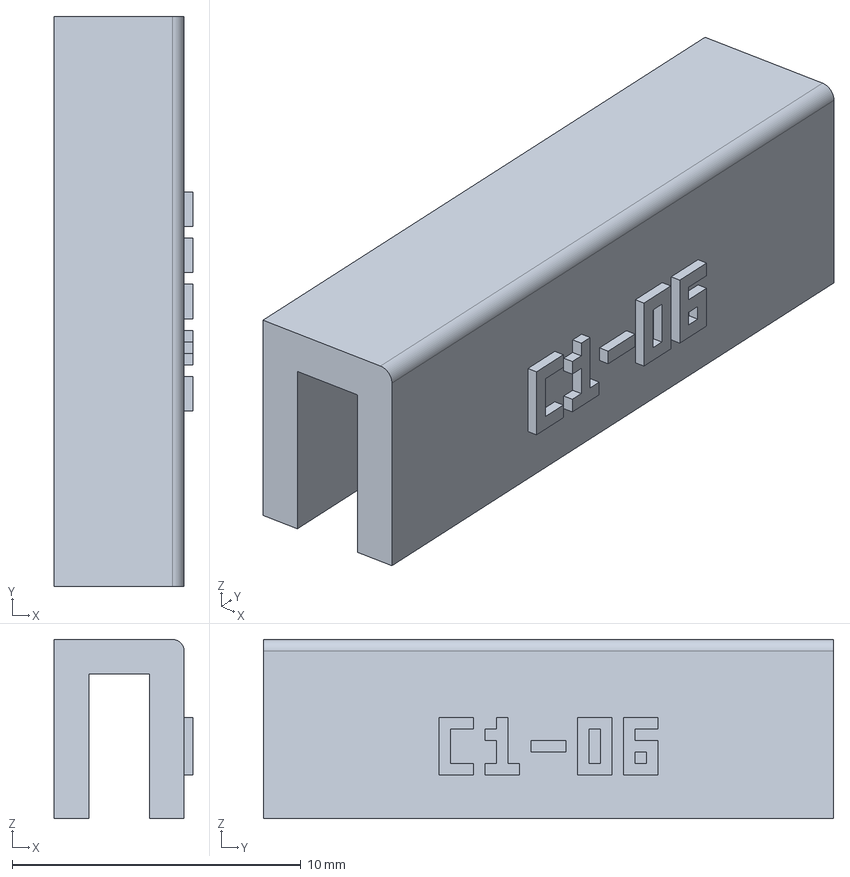
[picture p61: CAD file, 2026-09-30]
engineering/r9-fitfix-01/out/coupons/c1-06/7u40-r9f-c1-06-guard-qty2-mm.step
4.80 x 19.8 x 6.20 mm
