Takazudo/zudo-case/engineering/r9-fitfix-01/out/coupons/c1-07/7u40-r9f-c1-07-guard-qty2-mm.step

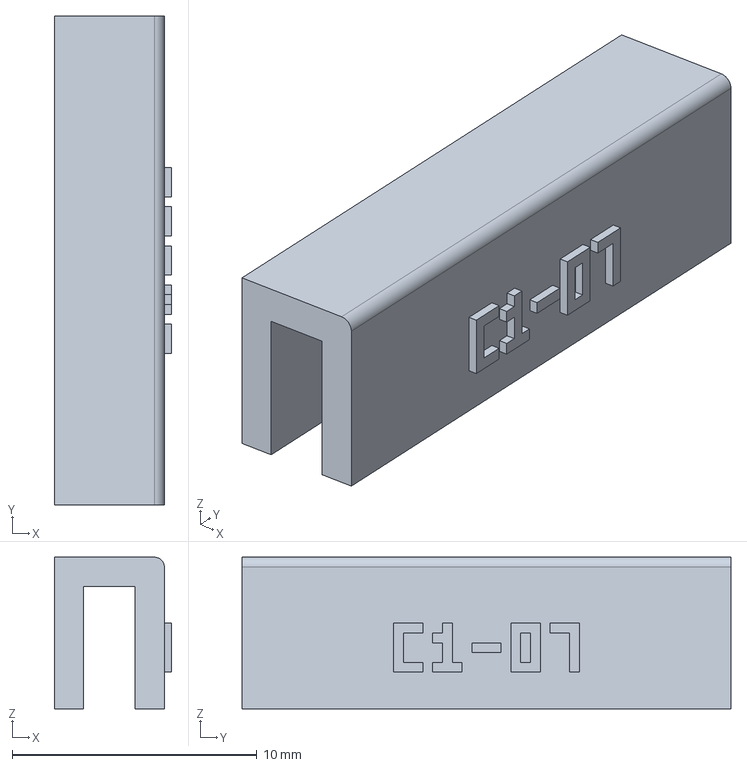
[picture p62: CAD file, 2026-09-30]
engineering/r9-fitfix-01/out/coupons/c1-07/7u40-r9f-c1-07-guard-qty2-mm.step
4.80 x 20.0 x 6.20 mm
