Takazudo/zudo-case/engineering/r9-fitfix-01/out/coupons/c1-metal/7u40-r9f-c1-metal-edge-qty1-mm.step

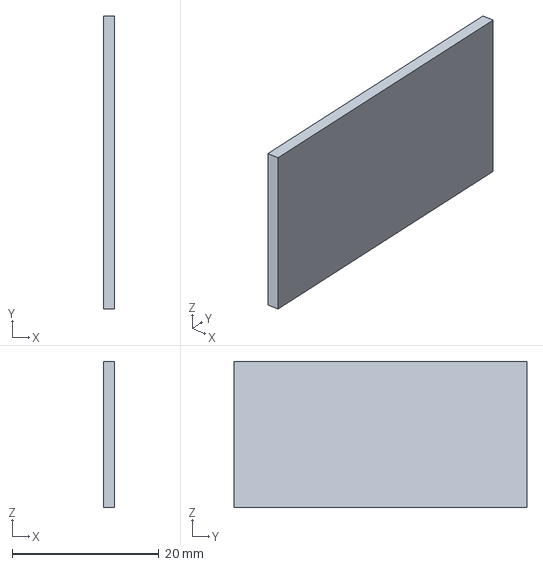
[picture p63: CAD file, 2026-09-30]
engineering/r9-fitfix-01/out/coupons/c1-metal/7u40-r9f-c1-metal-edge-qty1-mm.step
1.50 x 40.0 x 20.0 mm
