Takazudo/zudo-case/engineering/r9-fitfix-01/out/coupons/c2-01/7u40-r9f-c2-01-wall-qty1-mm.step

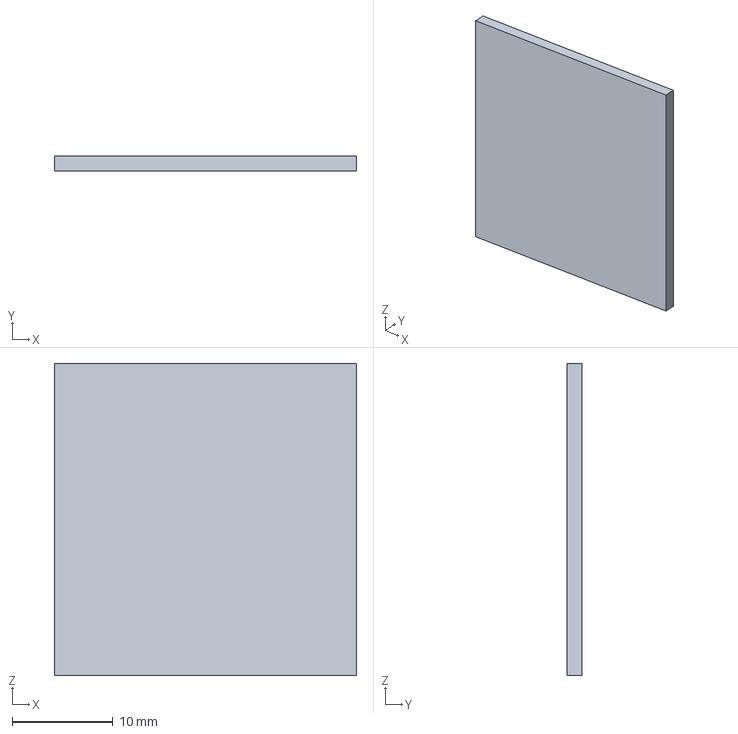
[picture p64: CAD file, 2026-09-30]
engineering/r9-fitfix-01/out/coupons/c2-01/7u40-r9f-c2-01-wall-qty1-mm.step
30.0 x 1.50 x 31.0 mm
