Takazudo/zudo-case/engineering/r9-fitfix-01/out/coupons/c2-02/7u40-r9f-c2-02-plate-qty1-mm.step

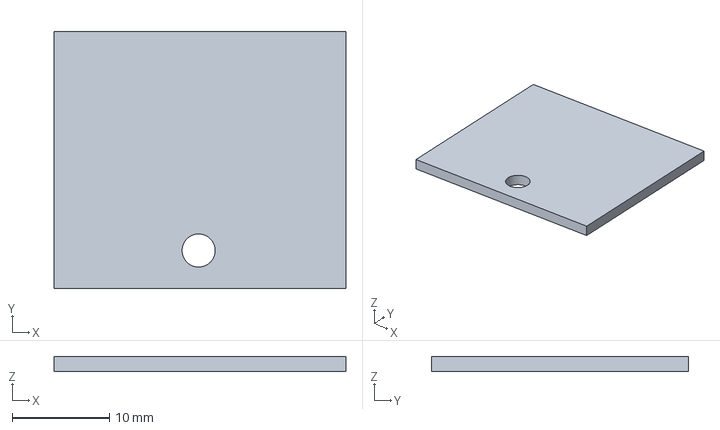
[picture p65: CAD file, 2026-09-30]
engineering/r9-fitfix-01/out/coupons/c2-02/7u40-r9f-c2-02-plate-qty1-mm.step
30.0 x 26.4 x 1.50 mm
