Takazudo/zudo-case/engineering/r9-fitfix-01/out/coupons/c4-01/7u40-r9f-c4-01-wall-qty1-mm.step

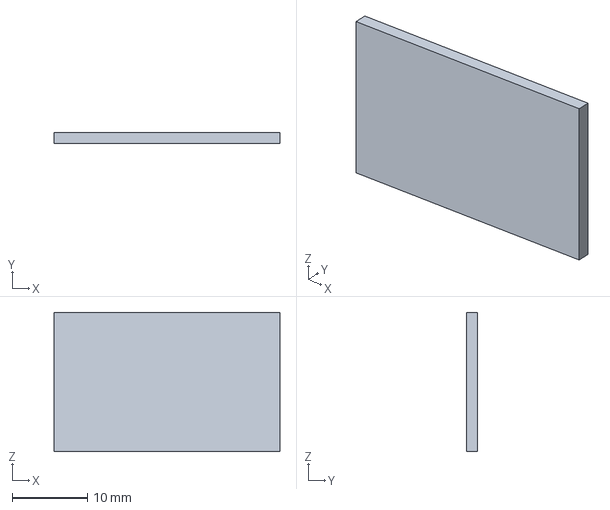
[picture p66: CAD file, 2026-09-30]
engineering/r9-fitfix-01/out/coupons/c4-01/7u40-r9f-c4-01-wall-qty1-mm.step
30.0 x 1.50 x 18.5 mm
