Takazudo/zudo-case/engineering/r9-fitfix-01/out/coupons/c5-01/7u40-r9f-c5-01-left-qty1-mm.step

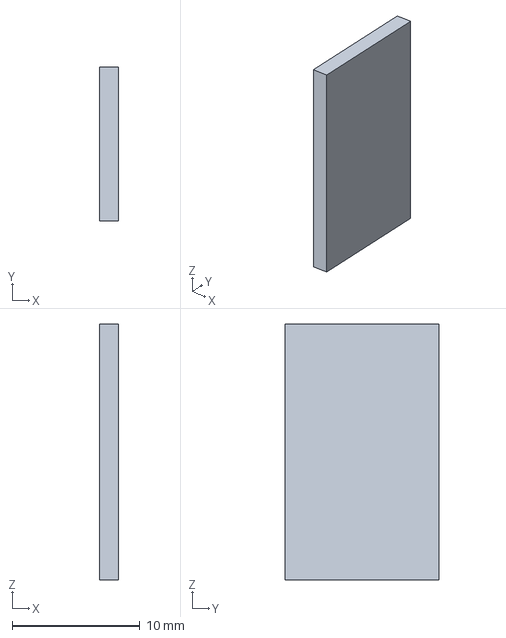
[picture p67: CAD file, 2026-09-30]
engineering/r9-fitfix-01/out/coupons/c5-01/7u40-r9f-c5-01-left-qty1-mm.step
1.50 x 12.0 x 20.0 mm
