Takazudo/zudo-case/engineering/r9-fitfix-01/out/pa12/t1p0/guards/7u40-r9f-t1p0-lower-width-half-qty4-mm.step

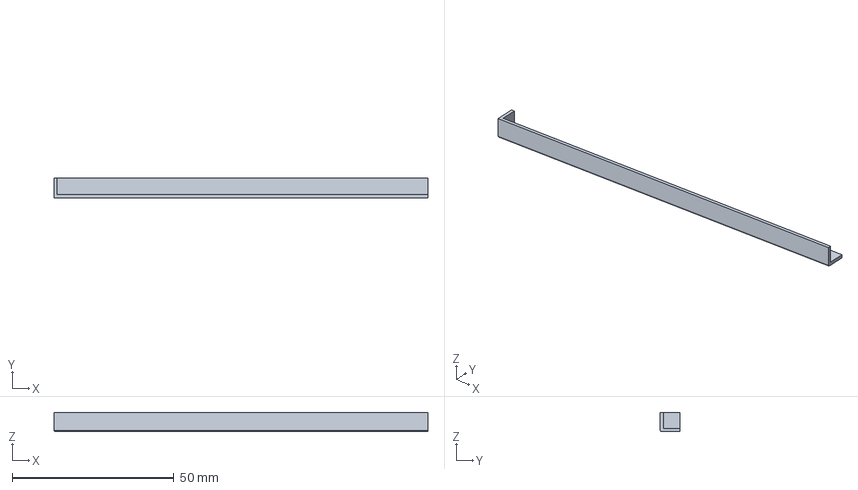
[picture p68: CAD file, 2026-09-30]
engineering/r9-fitfix-01/out/pa12/t1p0/guards/7u40-r9f-t1p0-lower-width-half-qty4-mm.step
115.8 x 6.05 x 6.00 mm
