Takazudo/zudo-case/engineering/r9-fitfix-01/out/pa12/t1p0/lid/7u40-r9f-lid-frame-fr-qty1-mm.step

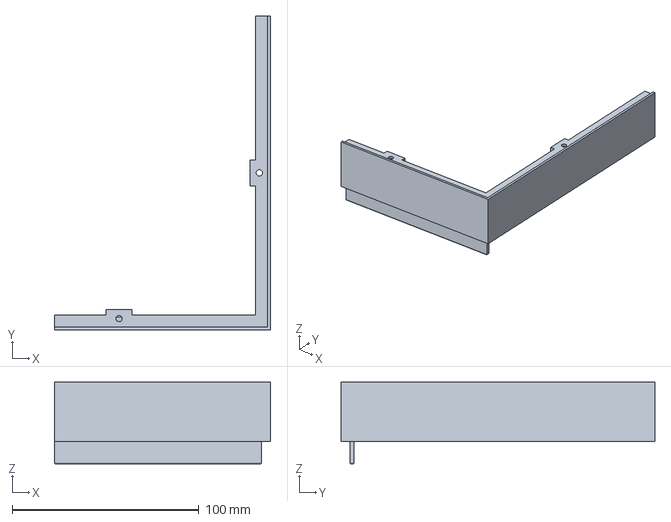
[picture p69: CAD file, 2026-09-30]
engineering/r9-fitfix-01/out/pa12/t1p0/lid/7u40-r9f-lid-frame-fr-qty1-mm.step
115.8 x 168.1 x 43.8 mm
