Takazudo/zudo-case/engineering/r9-fitfix-01/out/pa12/t1p2/guards/7u40-r9f-t1p2-top-a-qty2-mm.step

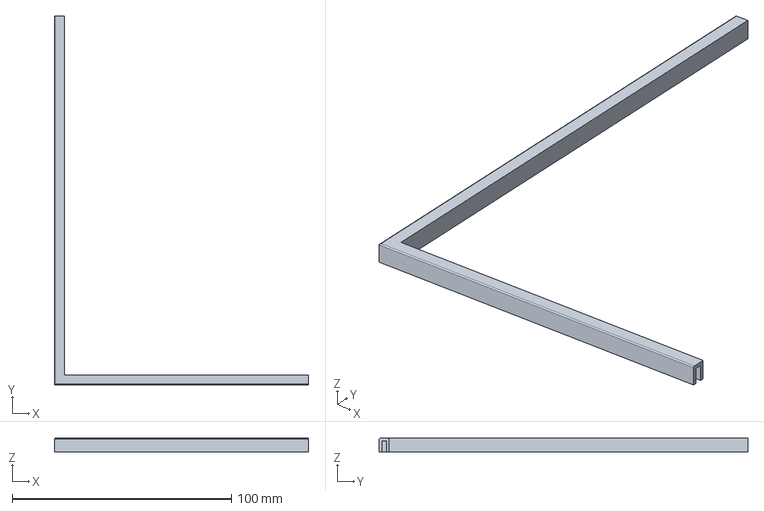
[picture p70: CAD file, 2026-09-30]
engineering/r9-fitfix-01/out/pa12/t1p2/guards/7u40-r9f-t1p2-top-a-qty2-mm.step
116.0 x 168.2 x 6.20 mm
