Takazudo/zudo-case/engineering/r9-prototype-01/out/aluminum/7u40-r9-al-left-right-qty2-mm.step

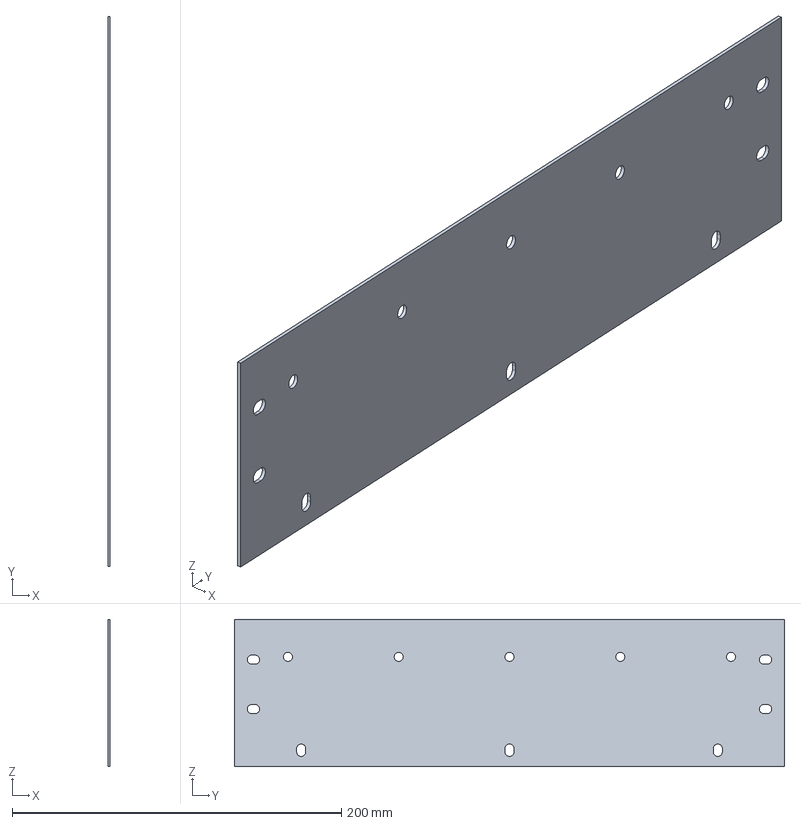
[picture p71: CAD file, 2026-09-30]
engineering/r9-prototype-01/out/aluminum/7u40-r9-al-left-right-qty2-mm.step
1.50 x 334.0 x 89.5 mm
