Takazudo/zudo-case/engineering/r9-prototype-01/out/coupons/c2/c2-01/7u40-r9-cpn-c2-01-guard-qty1-mm.step

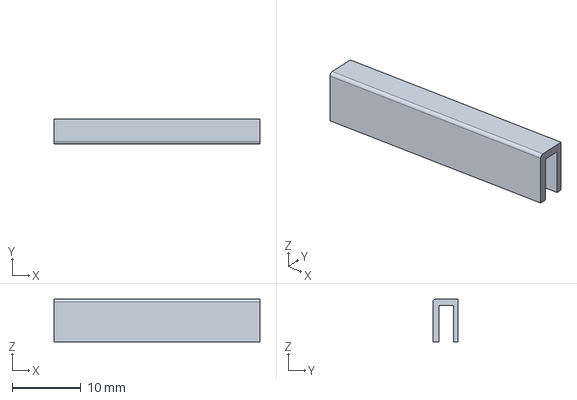
[picture p73: CAD file, 2026-09-30]
engineering/r9-prototype-01/out/coupons/c2/c2-01/7u40-r9-cpn-c2-01-guard-qty1-mm.step
30.0 x 3.70 x 6.20 mm
