Takazudo/zudo-case/engineering/r9-prototype-01/out/coupons/c2/c2-02/7u40-r9-cpn-c2-02-lid-frame-qty1-mm.step

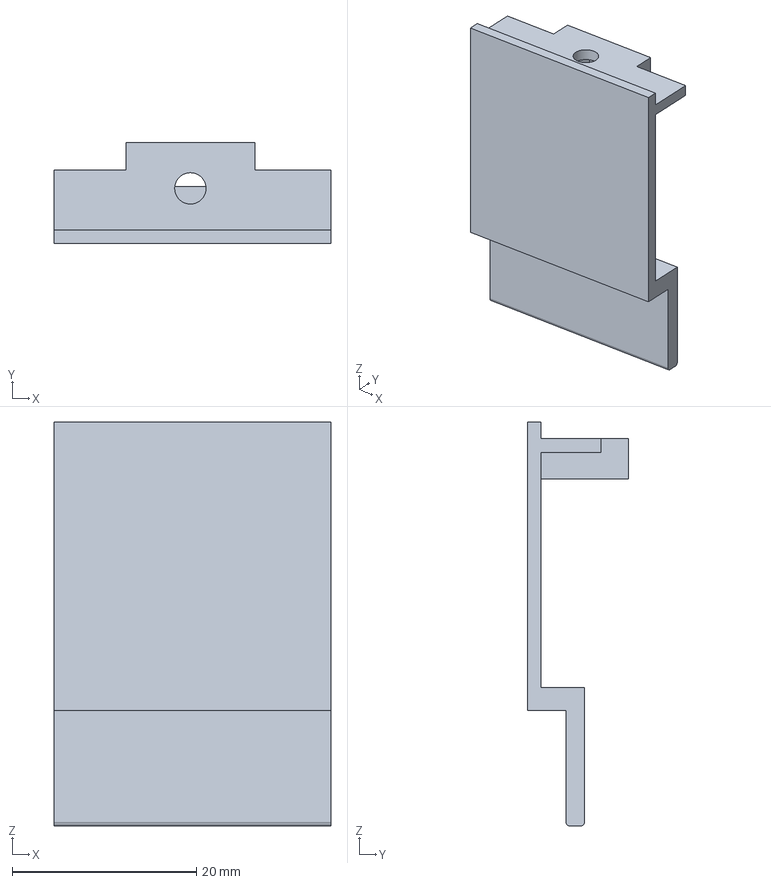
[picture p74: CAD file, 2026-09-30]
engineering/r9-prototype-01/out/coupons/c2/c2-02/7u40-r9-cpn-c2-02-lid-frame-qty1-mm.step
30.0 x 11.0 x 43.8 mm
