Takazudo/zudo-case/engineering/r9-prototype-01/out/coupons/c2/c2-03/7u40-r9-cpn-c2-03-rail-envelope-qty1-mm.step

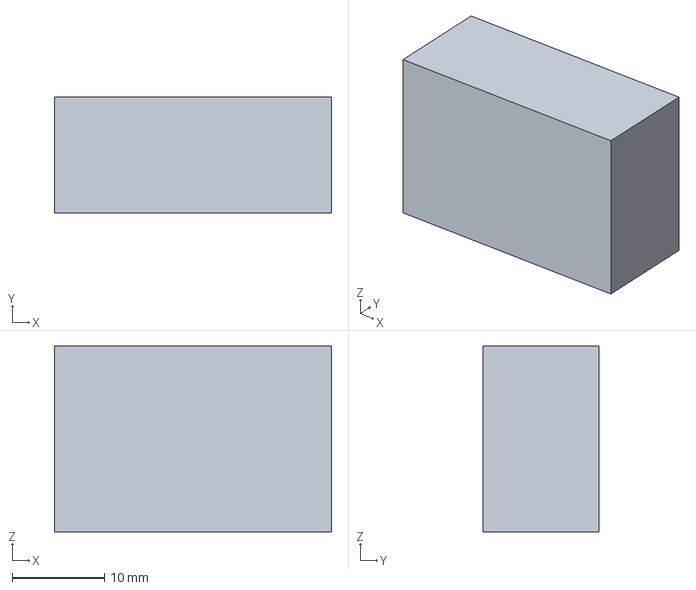
[picture p75: CAD file, 2026-09-30]
engineering/r9-prototype-01/out/coupons/c2/c2-03/7u40-r9-cpn-c2-03-rail-envelope-qty1-mm.step
30.0 x 12.6 x 20.1 mm
