Takazudo/zudo-case/engineering/r9-prototype-01/out/hardware-envelopes/7u40-r9-hw-rail-unit-envelope-qty6-mm.step

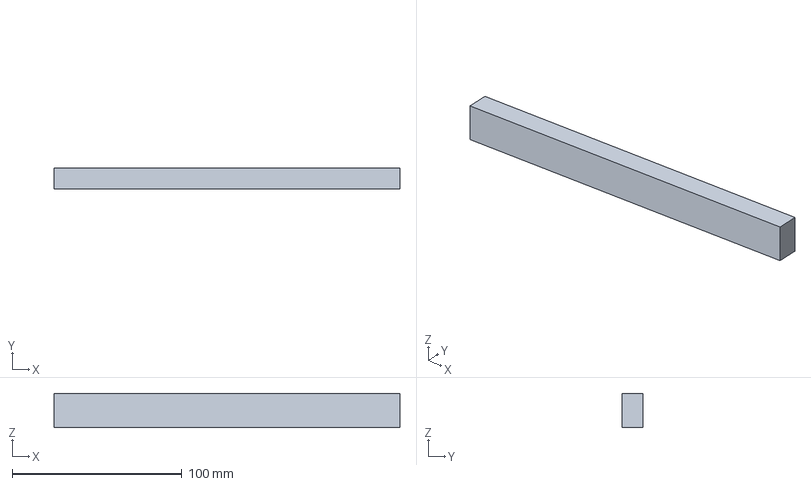
[picture p76: CAD file, 2026-09-30]
engineering/r9-prototype-01/out/hardware-envelopes/7u40-r9-hw-rail-unit-envelope-qty6-mm.step
204.0 x 12.6 x 20.1 mm
