Takazudo/zudo-case/engineering/r9-prototype-01/out/pa12/guards/t1p0/7u40-r9-pa12-guard-t1p0-lower-depth-b-qty2-mm.step

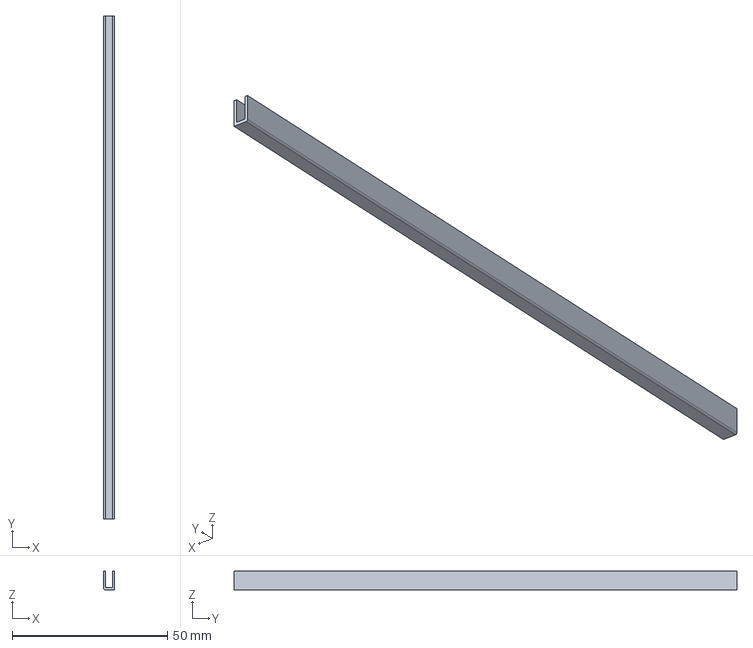
[picture p77: CAD file, 2026-09-30]
engineering/r9-prototype-01/out/pa12/guards/t1p0/7u40-r9-pa12-guard-t1p0-lower-depth-b-qty2-mm.step
3.50 x 161.8 x 6.00 mm
