Takazudo/zudo-case/engineering/r9-prototype-01/out/pa12/lid/7u40-r9-pa12-lid-frame-br-qty1-mm.step

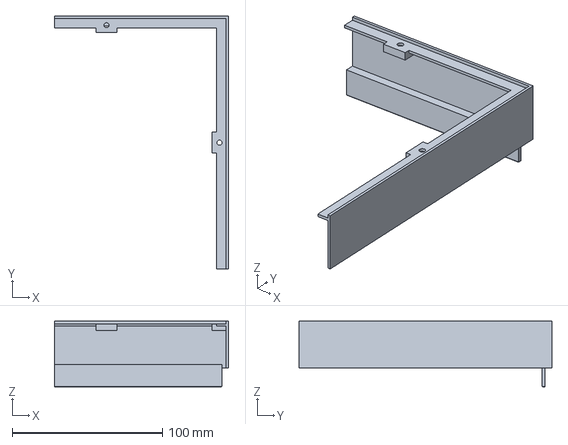
[picture p78: CAD file, 2026-09-30]
engineering/r9-prototype-01/out/pa12/lid/7u40-r9-pa12-lid-frame-br-qty1-mm.step
115.7 x 168.0 x 43.8 mm
