Takazudo/zudo-case/engineering/r6-body/engineering/3u60/aluminum/3u60_r6_aluminum_front_back_qty2_mm.step

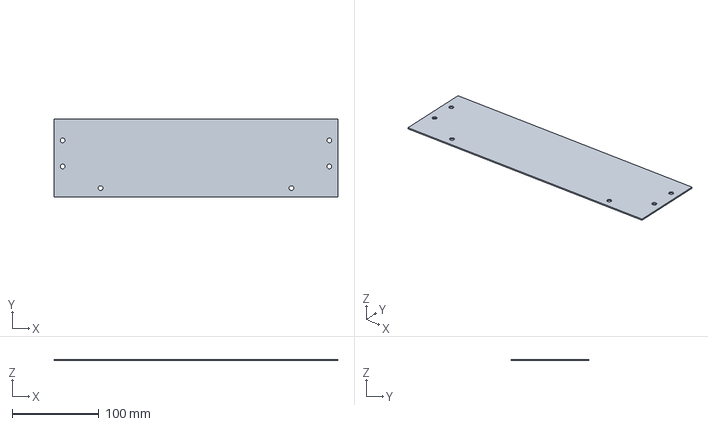
[picture p79: CAD file, 2026-09-24]
engineering/r6-body/engineering/3u60/aluminum/3u60_r6_aluminum_front_back_qty2_mm.step
327.4 x 89.5 x 1.50 mm
