Takazudo/zudo-case/engineering/r6-body/engineering/3u60/pcbs/3u60_r6_padder-1-row0_source_outline_mm.step

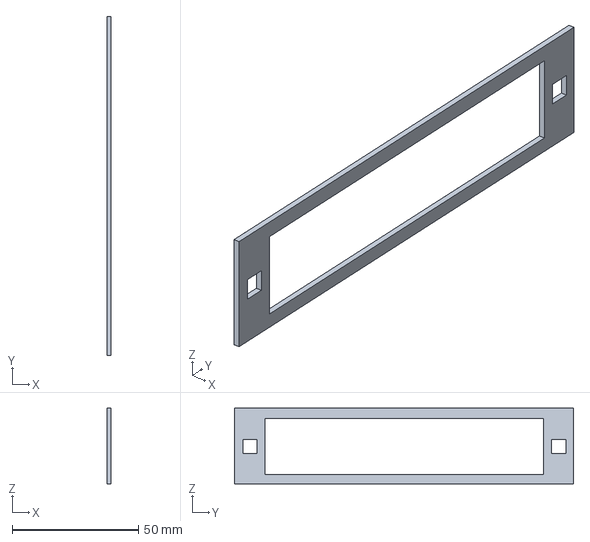
[picture p80: CAD file, 2026-09-24]
engineering/r6-body/engineering/3u60/pcbs/3u60_r6_padder-1-row0_source_outline_mm.step
1.60 x 134.5 x 30.0 mm
