Takazudo/zudo-case/engineering/r6-body/engineering/7u40/guards/7u40_r6_t1p2_02_top_corner_b_qty2_mm.step

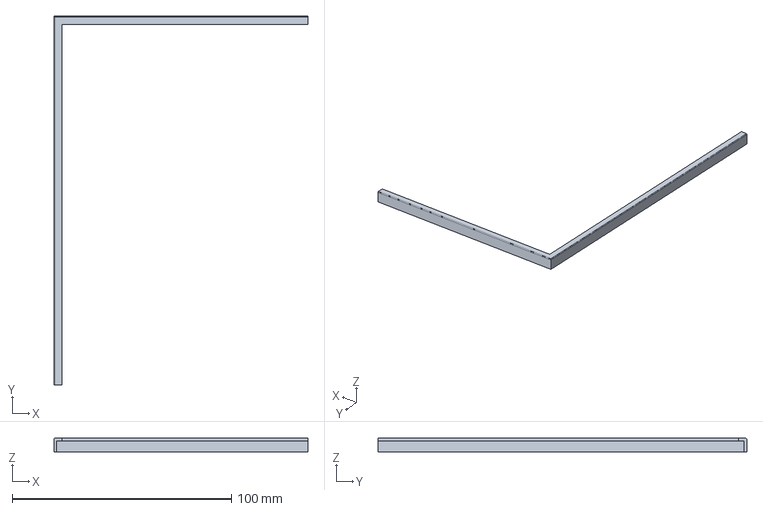
[picture p81: CAD file, 2026-09-24]
engineering/r6-body/engineering/7u40/guards/7u40_r6_t1p2_02_top_corner_b_qty2_mm.step
115.9 x 168.2 x 6.20 mm
