Takazudo/zudo-case/engineering/r6-body/engineering/7u60/guards/7u60_r6_t1p0_01_top_corner_a_qty2_mm.step

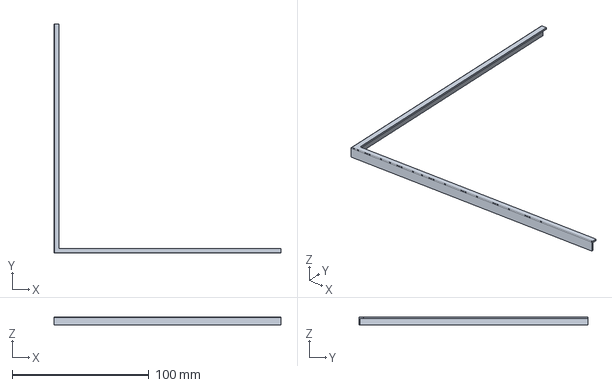
[picture p82: CAD file, 2026-09-24]
engineering/r6-body/engineering/7u60/guards/7u60_r6_t1p0_01_top_corner_a_qty2_mm.step
166.2 x 168.0 x 6.00 mm
