Takazudo/zudo-case/engineering/r6-body/stl/3u60/t1p2/3u60_r6_t1p2_02_lower_width_half_qty4_mm.stl

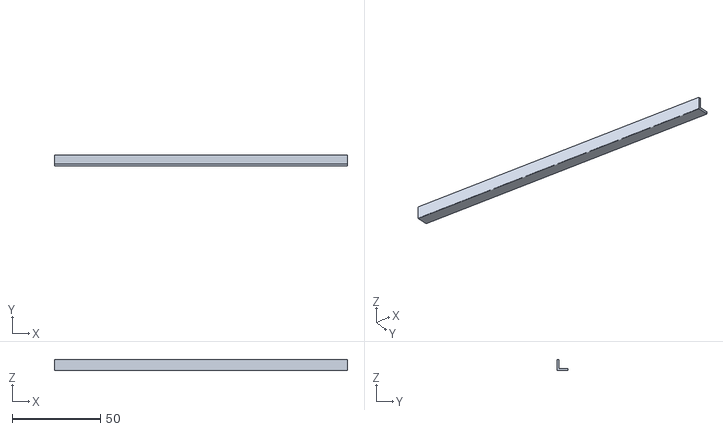
[picture p83: CAD file, 2026-09-24]
engineering/r6-body/stl/3u60/t1p2/3u60_r6_t1p2_02_lower_width_half_qty4_mm.stl
166.4 x 6.20 x 6.20
