Takazudo/zudo-case/engineering/r6-body/stl/7u40/t1p0/7u40_r6_t1p0_03_lower_width_half_qty4_mm.stl

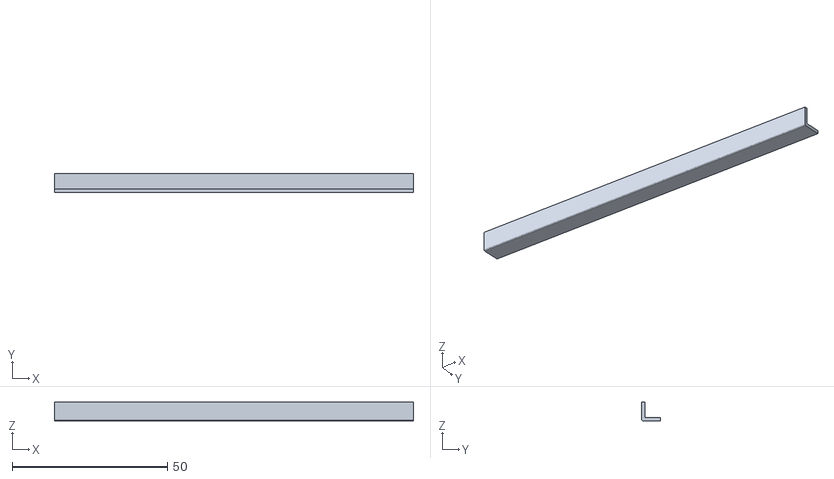
[picture p84: CAD file, 2026-09-24]
engineering/r6-body/stl/7u40/t1p0/7u40_r6_t1p0_03_lower_width_half_qty4_mm.stl
115.7 x 6.00 x 6.00
