Takazudo/zudo-case/engineering/r9-fitfix-01/out/coupons/c2-01/7u40-r9f-c2-01-guard-qty1-mm.step

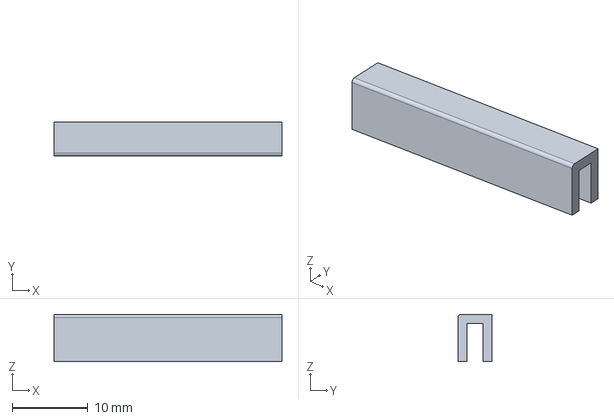
[picture p86: CAD file, 2026-09-30]
engineering/r9-fitfix-01/out/coupons/c2-01/7u40-r9f-c2-01-guard-qty1-mm.step
30.0 x 4.50 x 6.20 mm
