Takazudo/zudo-case/engineering/r9-fitfix-01/out/coupons/c4-01/7u40-r9f-c4-01-lower-guard-qty1-mm.step

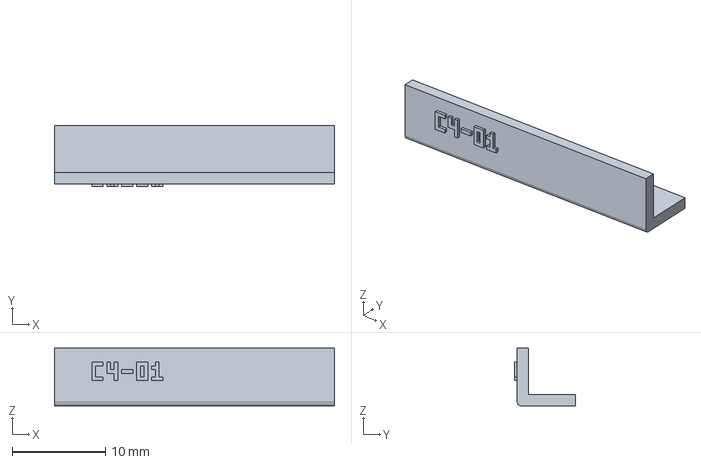
[picture p87: CAD file, 2026-09-30]
engineering/r9-fitfix-01/out/coupons/c4-01/7u40-r9f-c4-01-lower-guard-qty1-mm.step
30.0 x 6.55 x 6.20 mm
