Takazudo/zudo-case/engineering/r9-fitfix-01/out/coupons/c5-01/7u40-r9f-c5-01-front-qty1-mm.step

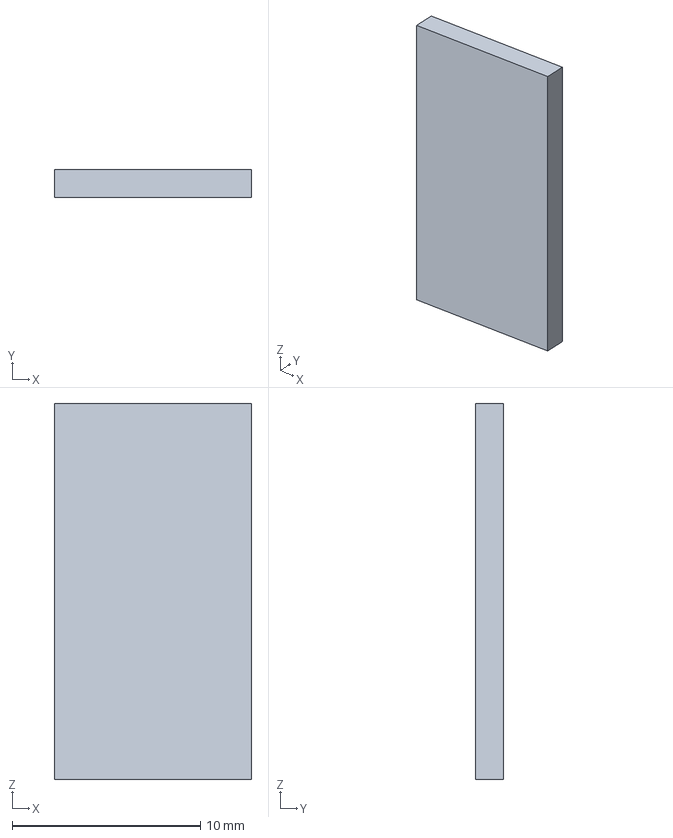
[picture p88: CAD file, 2026-09-30]
engineering/r9-fitfix-01/out/coupons/c5-01/7u40-r9f-c5-01-front-qty1-mm.step
10.5 x 1.50 x 20.0 mm
