Takazudo/zudo-case/engineering/r9-fitfix-01/out/pa12/t1p0/guards/7u40-r9f-t1p0-top-b-qty2-mm.step

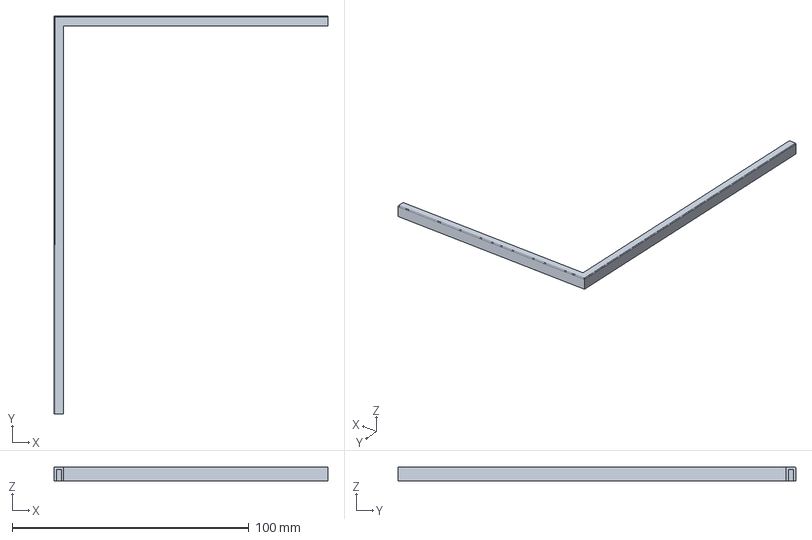
[picture p89: CAD file, 2026-09-30]
engineering/r9-fitfix-01/out/pa12/t1p0/guards/7u40-r9f-t1p0-top-b-qty2-mm.step
115.8 x 168.1 x 6.00 mm
