Takazudo/zudo-case/engineering/r9-fitfix-01/out/pa12/t1p2/guards/7u40-r9f-t1p2-lower-depth-b-qty2-mm.step

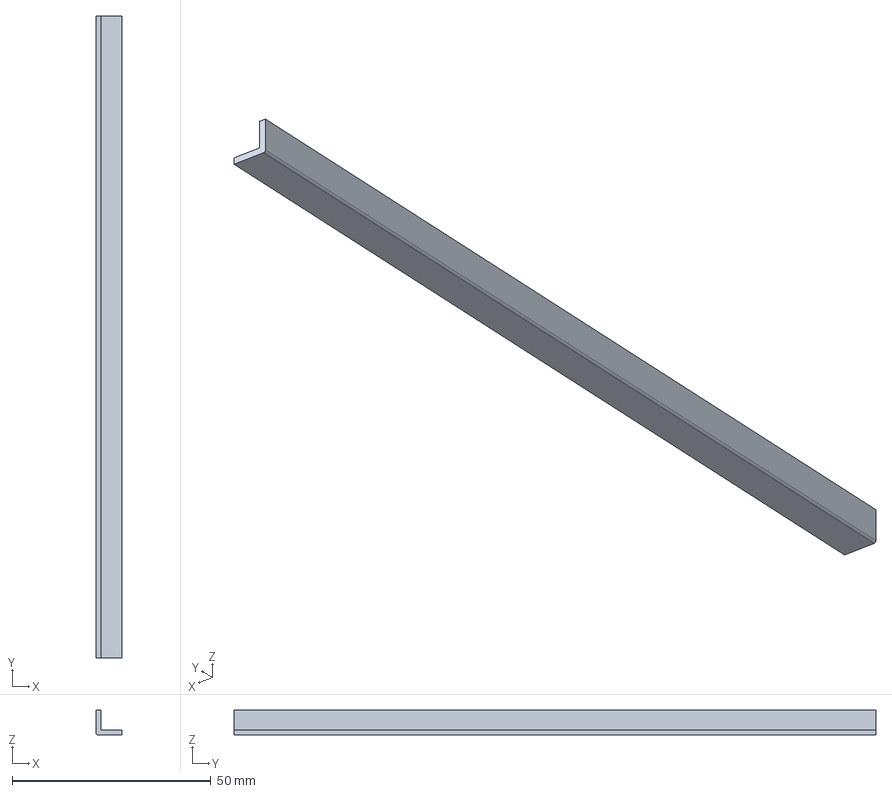
[picture p90: CAD file, 2026-09-30]
engineering/r9-fitfix-01/out/pa12/t1p2/guards/7u40-r9f-t1p2-lower-depth-b-qty2-mm.step
6.50 x 161.5 x 6.20 mm
