Takazudo/zudo-case/engineering/r9-prototype-01/out/coupons/7u40-r9-cpn-c1-03-qty1-mm.step

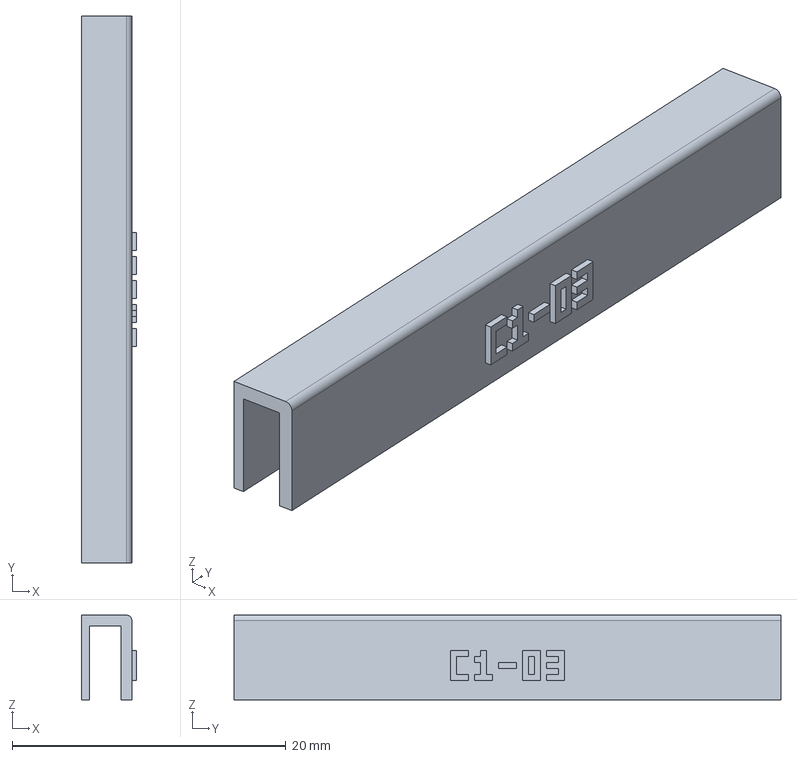
[picture p91: CAD file, 2026-09-30]
engineering/r9-prototype-01/out/coupons/7u40-r9-cpn-c1-03-qty1-mm.step
4.05 x 40.0 x 6.20 mm
