Takazudo/zudo-case/engineering/r9-prototype-01/out/pa12/guards/t1p0/7u40-r9-pa12-guard-t1p0-vertical-corner-qty4-mm.step

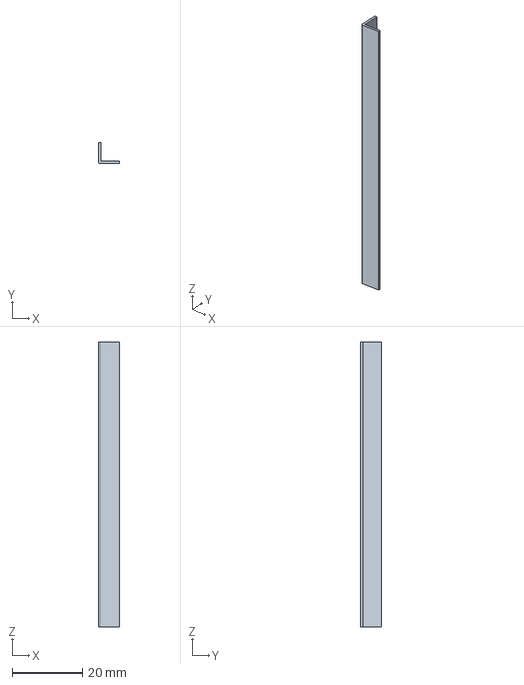
[picture p93: CAD file, 2026-09-30]
engineering/r9-prototype-01/out/pa12/guards/t1p0/7u40-r9-pa12-guard-t1p0-vertical-corner-qty4-mm.step
6.00 x 6.00 x 81.0 mm
