Takazudo/zudo-case/engineering/r9-prototype-01/out/pa12/guards/t1p2/7u40-r9-pa12-guard-t1p2-top-b-qty2-mm.step

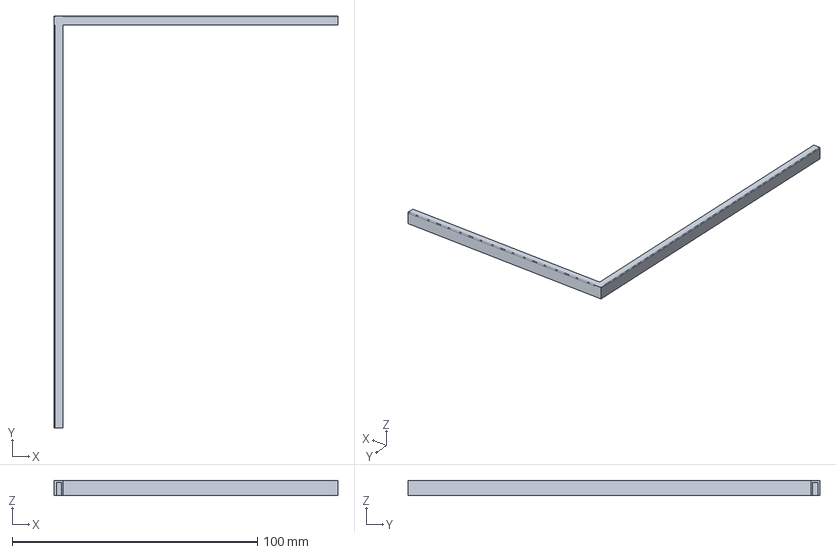
[picture p94: CAD file, 2026-09-30]
engineering/r9-prototype-01/out/pa12/guards/t1p2/7u40-r9-pa12-guard-t1p2-top-b-qty2-mm.step
115.7 x 167.9 x 6.20 mm
