Takazudo/zudo-case/engineering/r6-body/engineering/3u60/aluminum/3u60_r6_aluminum_bottom_qty1_mm.step

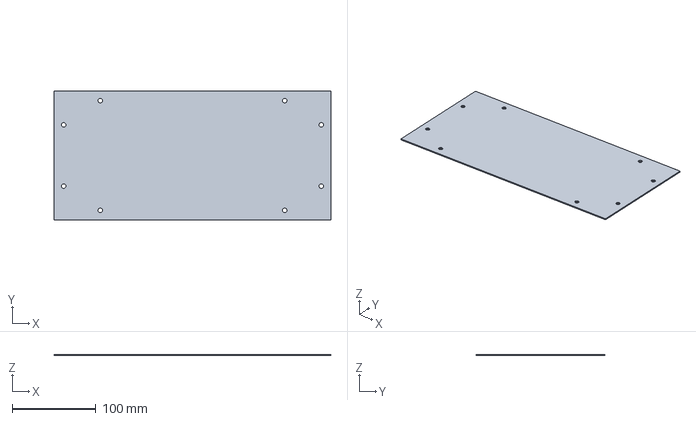
[picture p95: CAD file, 2026-09-24]
engineering/r6-body/engineering/3u60/aluminum/3u60_r6_aluminum_bottom_qty1_mm.step
330.4 x 154.0 x 1.50 mm
