Takazudo/zudo-case/engineering/r6-body/engineering/3u60/guards/3u60_r6_t1p0_01_top_u_qty2_mm.step

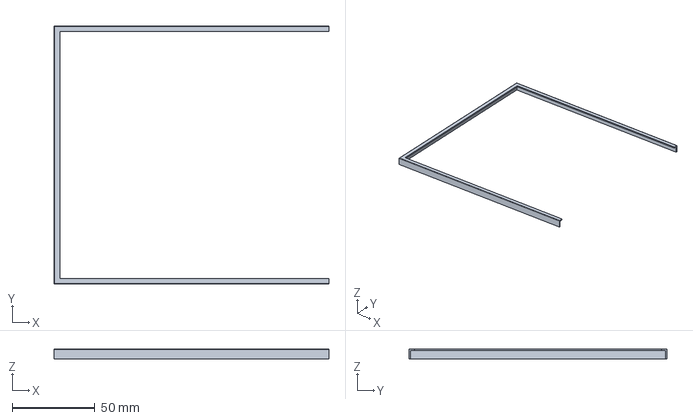
[picture p96: CAD file, 2026-09-24]
engineering/r6-body/engineering/3u60/guards/3u60_r6_t1p0_01_top_u_qty2_mm.step
166.2 x 156.0 x 6.00 mm
