Takazudo/zudo-case/engineering/r6-body/stl/3u60/t1p0/3u60_r6_t1p0_02_lower_width_half_qty4_mm.stl

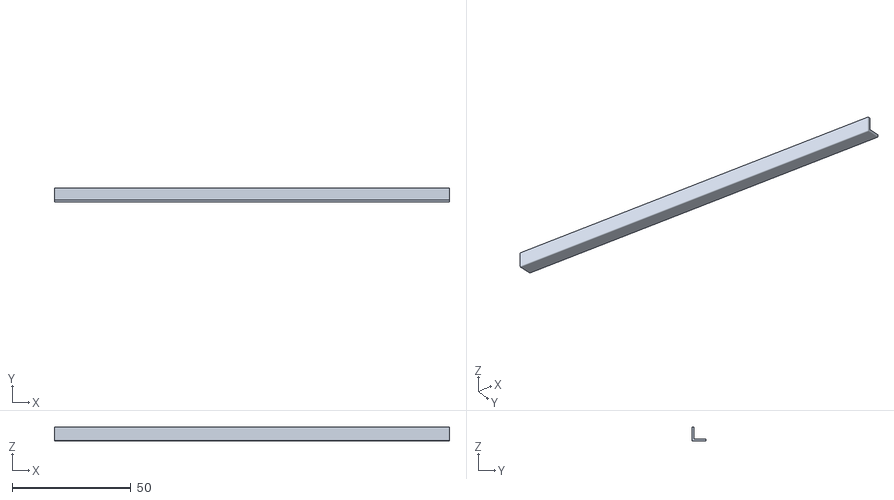
[picture p97: CAD file, 2026-09-24]
engineering/r6-body/stl/3u60/t1p0/3u60_r6_t1p0_02_lower_width_half_qty4_mm.stl
166.2 x 6.00 x 6.00
