Takazudo/zudo-case/engineering/r9-fitfix-01/out/coupons/c5-01/7u40-r9f-c5-01-upper-guard-qty1-mm.step

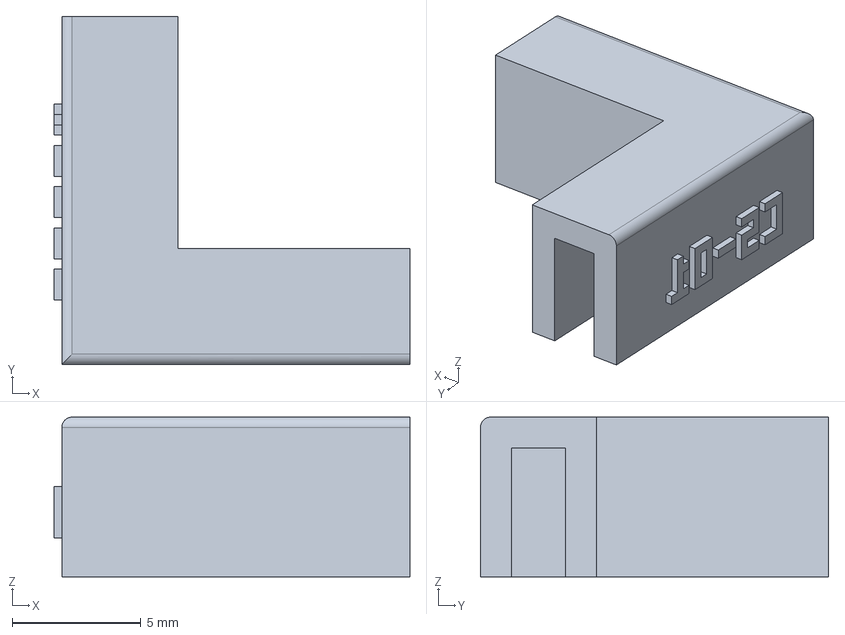
[picture p99: CAD file, 2026-09-30]
engineering/r9-fitfix-01/out/coupons/c5-01/7u40-r9f-c5-01-upper-guard-qty1-mm.step
13.8 x 13.5 x 6.20 mm
