Takazudo/zudo-case/engineering/r9-fitfix-01/out/pa12/t1p0/guards/7u40-r9f-t1p0-lower-depth-b-qty2-mm.step

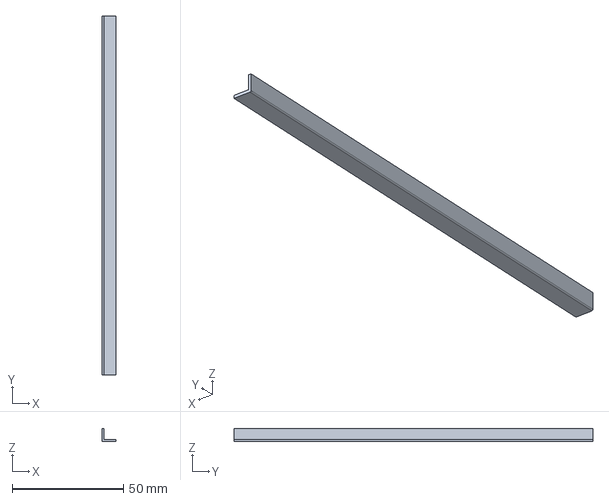
[picture p100: CAD file, 2026-09-30]
engineering/r9-fitfix-01/out/pa12/t1p0/guards/7u40-r9f-t1p0-lower-depth-b-qty2-mm.step
6.30 x 161.5 x 6.00 mm
