Takazudo/zudo-case/engineering/r6-body/stl/3u60/t1p2/3u60_r6_t1p2_01_top_u_qty2_mm.stl

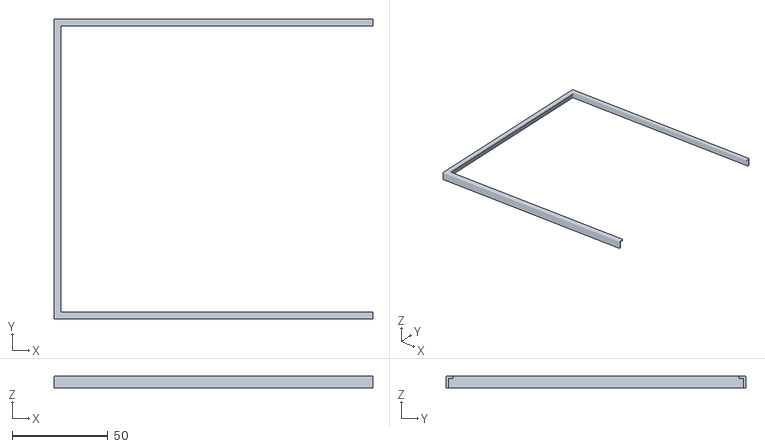
[picture p101: CAD file, 2026-09-24]
engineering/r6-body/stl/3u60/t1p2/3u60_r6_t1p2_01_top_u_qty2_mm.stl
166.4 x 156.4 x 6.20
