Takazudo/zudo-case/engineering/r9-fitfix-01/out/coupons/c2-03/7u40-r9f-c2-03-frame-qty1-mm.step

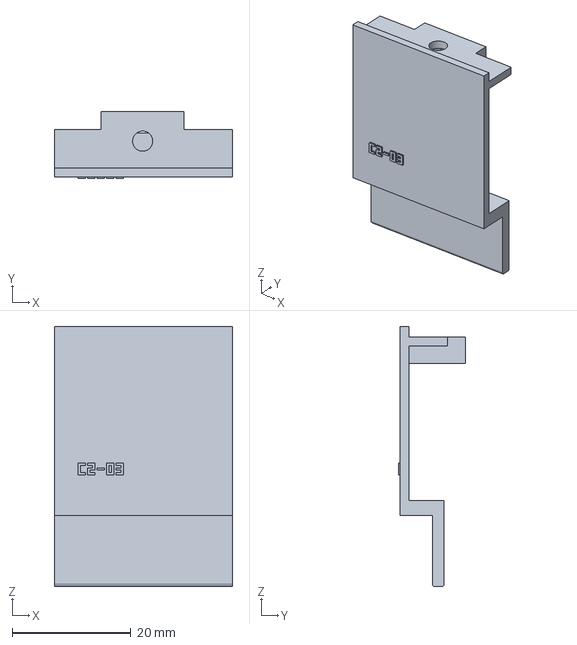
[picture p102: CAD file, 2026-09-30]
engineering/r9-fitfix-01/out/coupons/c2-03/7u40-r9f-c2-03-frame-qty1-mm.step
30.0 x 11.3 x 43.8 mm
