Takazudo/zudo-case/engineering/r9-prototype-01/out/hardware-envelopes/7u40-r9-hw-panel-bracket-qty18-mm.step

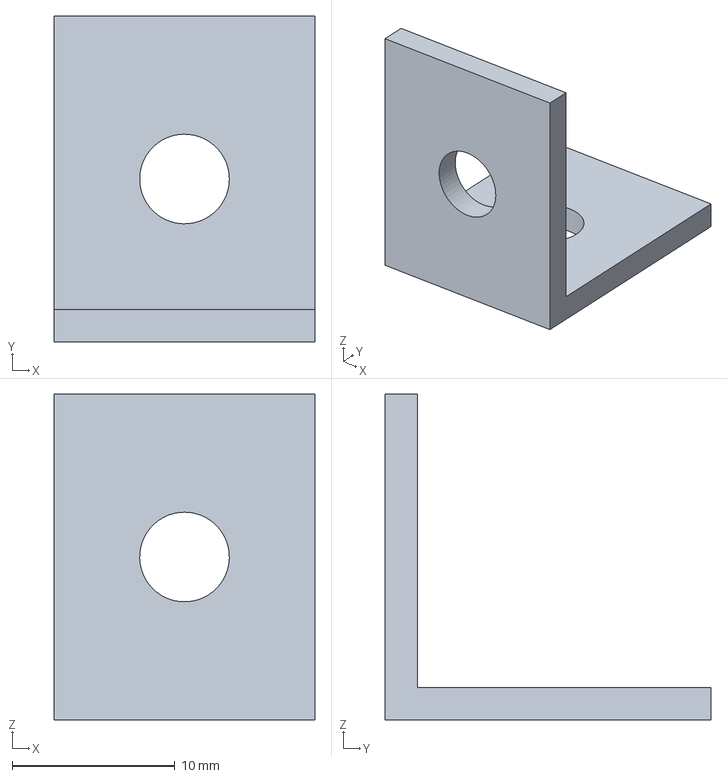
[picture p104: CAD file, 2026-09-30]
engineering/r9-prototype-01/out/hardware-envelopes/7u40-r9-hw-panel-bracket-qty18-mm.step
16.0 x 20.0 x 20.0 mm
