Takazudo/zudo-case/src/content/docs/manufacturing/index.mdx

---
title: "製作・見積"
description: "BOM、発注条件、価格根拠を分けて管理する。"
sidebar_position: 40
---

BOM、発注条件、価格根拠を分けて管理する。

<CategoryNav category="manufacturing" />
