Takazudo/zudo-case/public/assets/images/r6/3u60-assembled.png

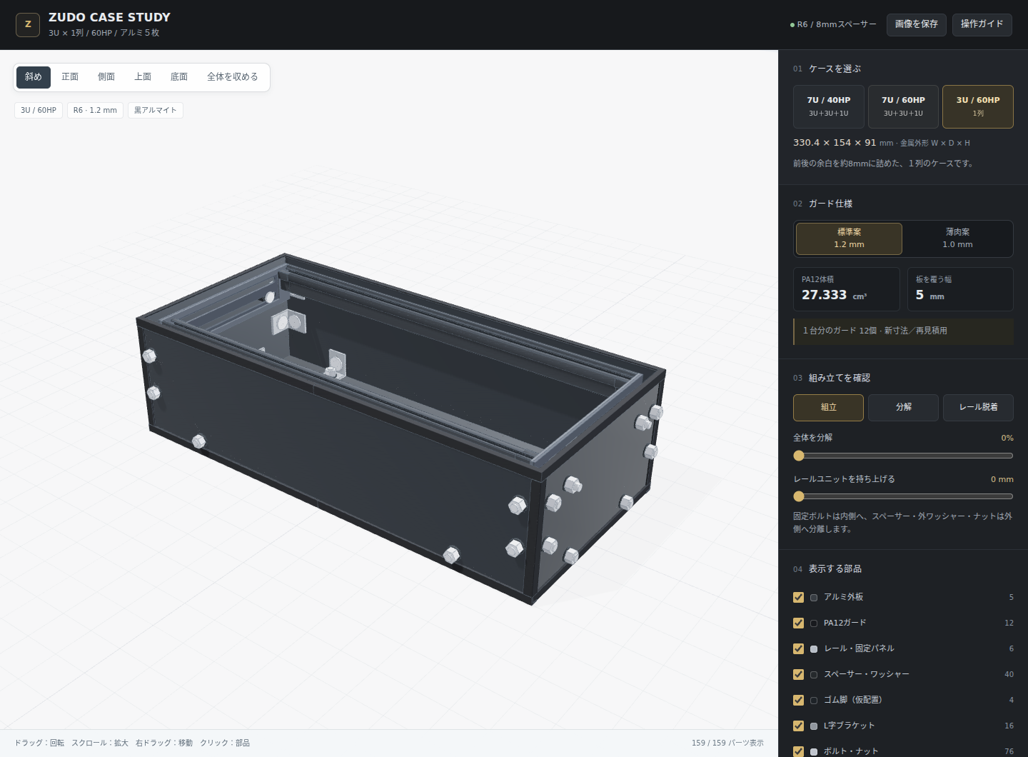
public/assets/images/r6/3u60-assembled.png
