Takazudo/zudo-case/public/assets/images/r6/7u40-assembled.png

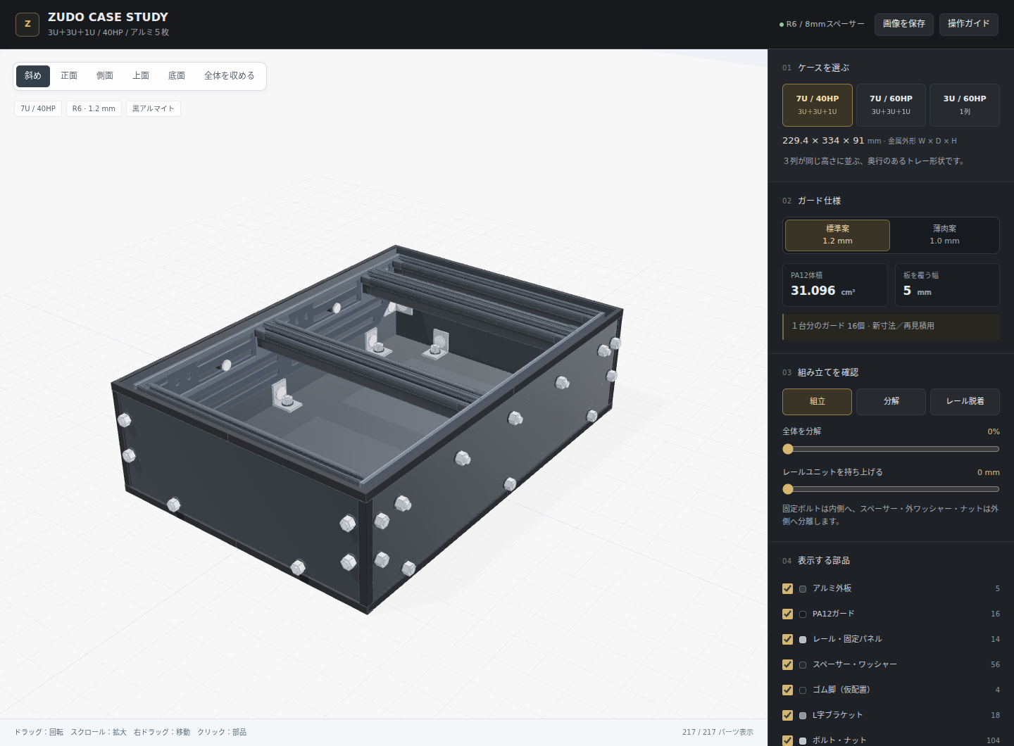
public/assets/images/r6/7u40-assembled.png
