Takazudo/zudo-case/public/assets/images/r6/7u60-assembled.png

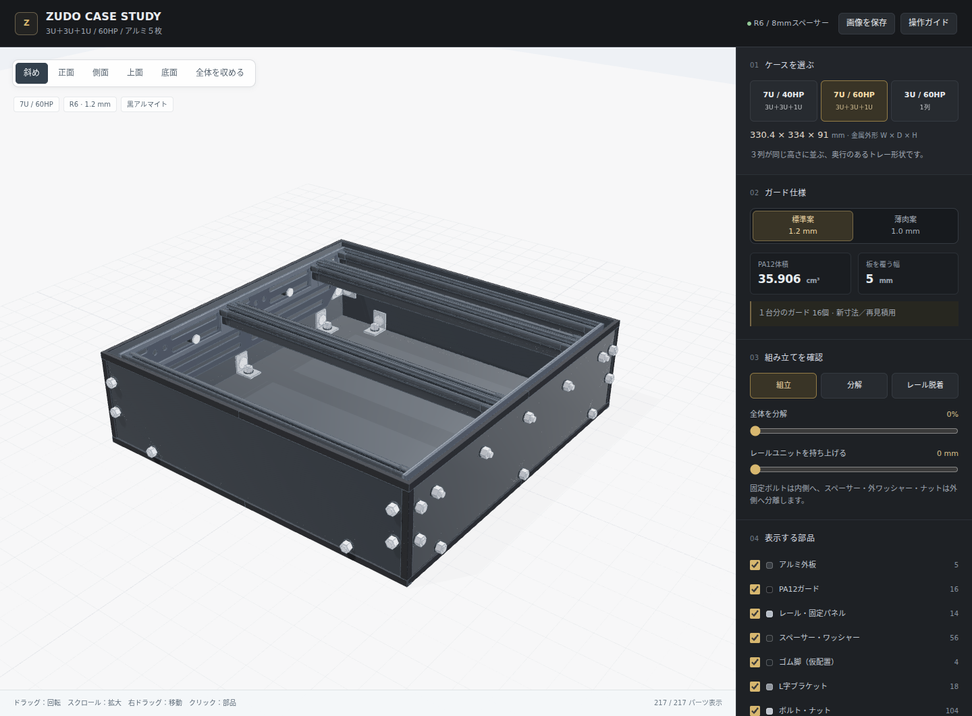
public/assets/images/r6/7u60-assembled.png
