Takazudo/zudo-case/src/content/docs/verification/coupon-record.mdx

---
title: "試験片の空欄記録票"
description: "C1・C2・C3の実物結果を版と一緒に残す未記入書式。"
sidebar_position: 45
---

これは**未記入テンプレート**であり、合格や発注承認の記録ではない。[手順](./fit-test.mdx)で判定条件を先に決める。

| 項目 | 記録 |
|---|---|
| 試験日／実施者／測定器 |  |
| 機種／候補版／生成コミット |  |
| 試験片ID／STL・STEP・DXF名／SHA-256 |  |
| 造形業者／材料／黒染め／ロット |  |
| アルミ材質／実厚／アルマイト前後 |  |
| 接着材品番／貼付厚／硬化条件 |  |
| 比較する独立パラメータ |  |
| **実施前に決めた**合否条件・操作回数 |  |

| 試験片ID | CADすきま | 実測すきま | 無理なく取付 | ガタ | 保持・抜去 | 傷・露出 | 備考／写真 |
|---|---|---|---|---|---|---|---|
|  |  |  |  |  |  |  |  |
|  |  |  |  |  |  |  |  |
|  |  |  |  |  |  |  |  |

FDM予備確認とPA12-HP黒染めの結果、アルマイト前と後、短片保持と全長反り、蓋段差嵌合とノブ/バンドたわみを分けて記録する。

結果要約：＿＿＿＿　採用／再試験候補：＿＿＿＿　CADへ戻す変更：＿＿＿＿　対応G項目と未完理由：＿＿＿＿

短片だけでG04/G11を閉じない。

## R9-FITFIX-01の追加記録

[現行候補](../design/r9-fitfix-01.mdx)のC4は床＋壁の下辺Lガード、C5は２立板の上端角。部品ID・SHA-256、実板厚、接着材品番と実測厚、屋根の着座、保持、金属端の露出を記録する。空欄テンプレートは `engineering/r9-fitfix-01/handoff/FIT-RECORD.md`。結果はまだない。
