Takazudo/zudo-case/src/content/docs/verification/fit-test.mdx

---
title: "小さい試験片から確認する"
description: "保持と公差の未確定部分を、全体注文の前に切り分ける。"
sidebar_position: 20
---

## 目的

高価な全周部品を発注する前に、**実際の黒PA12と1.5mmアルミ、使用する締結材**の組合せを確認する。R9ではC1・C2・C3の試験片CADと未承認ZIPを用意した。現物結果はまだない。

| 試験片の対象 | 見ること | 次に反映する値 |
|---|---|---|
| 本体ガードの短いL断面 | きつさ、端の露出、外れ、アルミへの擦れ | 接触隙間、接着/保持、丸み |
| ガード継ぎ目と角 | 長さ誤差、角の浮き、他物へ当たる箇所 | 継ぎ目、分割位置、端面処理 |
| 蓋の前後差し込み | 2mm厚・12mm代・0.7mm隙間という仮条件が適切か | 差し込み厚/高さ/クリアランス |
| 天板の組立部 | ナットの収まり、締付で樹脂が潰れないか | ポケット寸法、ねじ長、当たり面 |
| 長穴と実ブラケット | 板端を揃えて締結できるか | 調整方向、長穴長、基準穴、座金 |

R7のナット嵌合試験片は、R7ロック用の形状。今回の載せ蓋の試験片としてそのまま使うことはしない。

## 記録テンプレート

```text
試験ID：
使用ファイル／版／SHA-256：
造形材料・染色・注文番号：
アルミ材質・厚さ・表面処理：
使用金具・ネジ：
図の寸法：
実測寸法（測定点・測定器）：
組立操作・結果：
傷・破損・外れ・ガタ：
変更するパラメータ：
写真・動画：
確認者／日付：
```

## 注意する境界

「手で入った」だけでは運搬中に保持できることを証明しない。逆に、短い試験片のきつさを長い全周部品へそのまま適用すると、反りや角の誤差を見落とす。短片で値を絞った後は、１台分の組立で確認する。

この文書では合格に必要な抜去力、締付トルク、許容ガタを新たに設定していない。製品要件と試験手順を決めて、結果と一緒に保存する。

## R9試験の順番

| 順番 | 対象 | 見ること |
|---|---|---|
| C1 | 短い本体ガードとアルミ端 | すきま、接着層、端の露出、保持・抜去 |
| C2 | 上端ガードと蓋段差・天板の局部組合せ | アルマイト後の抜き差し、枠の座、傷、ねじ |
| C3 | 実L字金具と長穴の短い接合 | 曲げ線沿いのずれ、座金受け面、工具と締付アクセス |

試験前に[空欄の記録票](./coupon-record.mdx)へ版とSHA-256、比較する**一つの変数**、許容ガタ・傷・保持力、操作回数、合否条件を書く。具体的な閾値は未決定であり、試験後に都合よく変えない。FDMは形状の予備確認だけとして、PA12-HP黒染めの本判定と分ける。アルミも切断後・アルマイト前と後を分け、材質・実厚・端面・接着材品番と貼付厚を記録する。

C1の寸法を確認してからC2へ進み、実座金候補を決めてC3を判定する。R9の試験片は[候補ZIP](../design/r9-prototype-01.mdx)から選ぶ。短片の合格は長いガードの反り、大きな蓋のたわみ、G04/G11の完了を意味しない。次に7U40一台で組立・実モジュール・バンド・バッグ内運搬を確認する。
