Takazudo/zudo-case/src/content/docs/verification/release.mdx

---
title: "検証記録と製作承認"
description: "既存の幾何検証、今回の文書検査、将来の実機試験を分ける。"
sidebar_position: 40
---

## 既存データに含まれる検証

R6ソースには、形状、STL、配置、ブラウザー操作のチェックJSONやレビュー文書がある。R8には[幾何チェック](/evidence/r8-original-geometry-checks.json)と[ブラウザーチェック](/evidence/r8-original-browser-validation.json)が含まれる。

これは**当時の生成環境での記録**。本資料への整理時に同じCAD検証や同じブラウザー試験を再実行したものではない。元レールに残した重複面、ねじ山の省略、模式頭径、未確定公差などの範囲制限は保存READMEを参照する。

## 文書整理時の検査

この引継ぎセットでは、MDX frontmatter、カテゴリ順序、相対リンク、画像/ダウンロードの実在、主要な寸法の足し算、数量、入力ファイルのSHA-256を検査する。

初期環境ではzudo-doc公式CLIの取得がnpm DNSエラーで停止した。その後、2026-09-24に公式scaffolderによる初期化、lockfileに基づく依存導入、実ビルドとブラウザー確認を完了した。確認範囲は[採用仕様とデータ状態](../overview/status.mdx)に記録する。文書の構造検査はビルドやブラウザー確認とは別であり、いずれもケースの嵌合・強度・運搬や製造承認を検証したものではない。新しいチェックアウトでは[セットアップ](../handoff/setup.mdx)を実行して確認する。

## リリースとして残すもの

承認するCAD版、各ファイルのSHA-256、単位、板厚、色/表面処理、数量、金具品番、実測条件、試験結果、承認者と日付を１つのmanifestへまとめる。変更した部品と変えなかった部品の版も示す。

`engineering/release/`は承認ファイルのみを置く場所。現在はREADMEだけで、`project/release-state.json`の承認リストは空。

`candidate_files`の`id`付き蓋候補を現行指定する場合、`current_lid_manufacturing`は候補ID・機種集合・版を照合する。指定は蓋候補の参照であり、`production_approved`を有効にせず、未承認のまま`engineering/release/`への配置を許可しない。承認には引き続き承認記録、機種別版、G01〜G11の完了根拠、公開ファイル一覧の一致が必要。

先に発注する必要がある試作品には「試作・未承認」を明示し、見積用・試作用・量産用のZIPを分ける。数字が揃っただけでは量産承認にしない。
