Takazudo/zudo-case/src/content/docs/verification/assemble-test.mdx

---
title: "組立・蓋・持ち運びの確認"
description: "実モジュールを入れた完成構成で確認するための計画。"
sidebar_position: 30
---

## 組立時

金属板と金具を仮締めし、板端、直角、対角、底の平面を整える。長穴が想定方向に動き、締結で板を無理に曲げていないか見る。必要な調整量と、締結後にガタが残る箇所を記録する。

レールユニットはfixer/padderを含めて一体で着脱し、８mmスペーサーと金具・ねじ頭が干渉しないかを確認する。元の形状で適合していたネジ頭でも、新しい金具配置による接触は別に見る。

## 蓋とモジュール

実際に入れるモジュールで最も高いノブ・スイッチを測る。パッチを外した状態で真上から閉じ、差し込み部がPCB、レール端、ネジへ当たらないことを確認する。バンドなしでの載り方と、バンド２本を留めた時の天板変形を比較する。

**30mmの蓋高さとノブ25mmは仮定**なので、バンドを強く締めた場合の余裕も含めて最終判断する。蓋を押さえていないのにバンドだけが締まる、枠だけが浮く、といった状態も確認する。

## 運搬と接地

対象のリュック、実際の搭載重量、バンド品番と通し方を明記して試す。底の脚、外側ナット、バックルなども含めて包絡を測り、収納時に傷が付く箇所を確認する。

移動後に蓋のずれ、バンドの横滑り、ガードの脱落、金具の緩み、黒仕上げの擦れ、モジュールへの接触がないか点検する。蓋やバンドを取っ手にして持ち上げない。

## 説明書へ戻すこと

閉じる前にパッチを抜く、バンドの掛け位置、締めすぎないこと、持ち方、点検箇所など、試作で必要だった操作を利用者向けの説明へ反映する。防水、防塵、衝撃保護の等級や重量限界は現時点で裏付けがないため表示しない。

試験回数・荷重・合否条件は未決定。結果が残るまでは[発注前ゲート](./before-order.mdx)を完了にしない。
