Takazudo/zudo-case/src/content/docs/verification/index.mdx

---
title: "現物確認・承認"
description: "計算やプレビューで確認したことと、現物で確認すべきこと。"
sidebar_position: 50
---

計算やプレビューで確認したことと、現物で確認すべきこと。

<CategoryNav category="verification" />
