Takazudo/zudo-case/engineering/order-map/verification/anodizing-c5-left-390.png

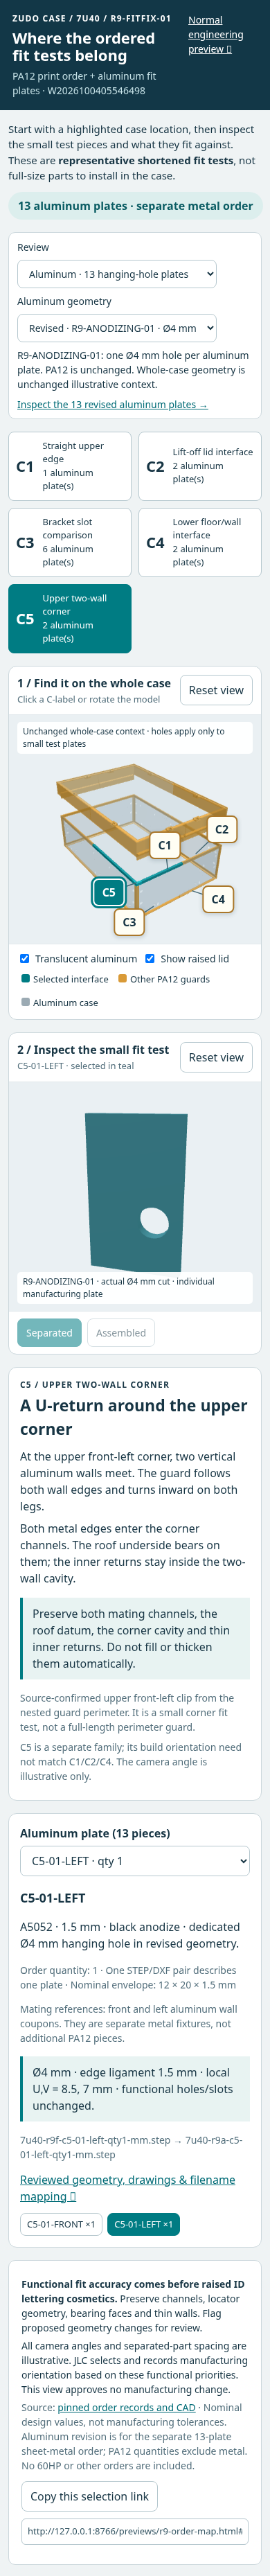
engineering/order-map/verification/anodizing-c5-left-390.png
