Takazudo/zudo-case/engineering/order-map/verification/anodizing-c5-left-1440.png

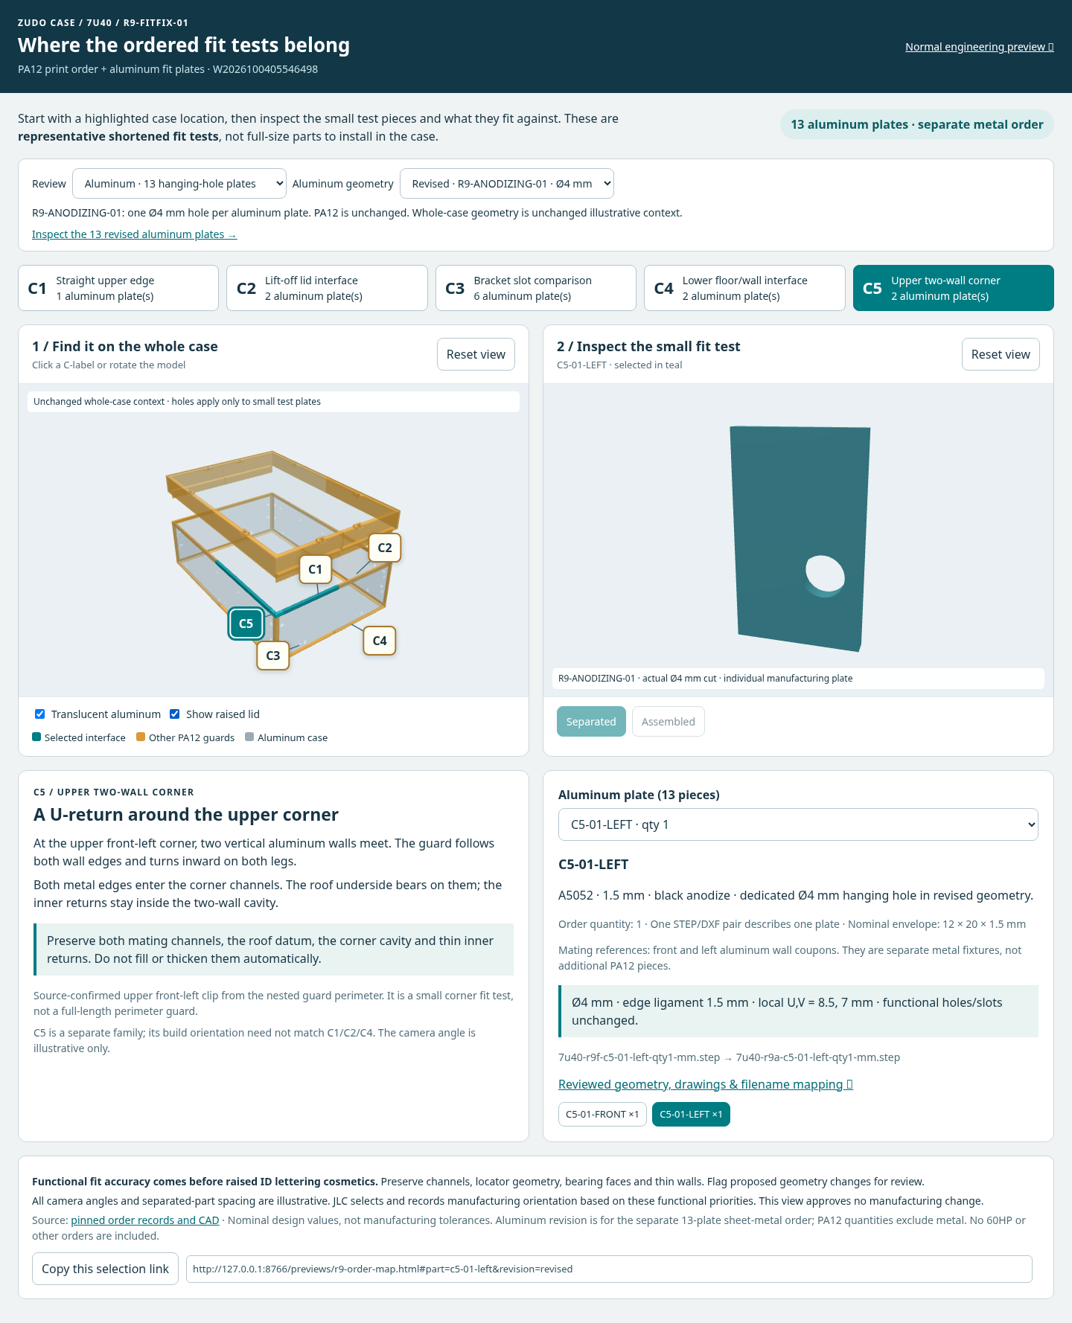
engineering/order-map/verification/anodizing-c5-left-1440.png
