Takazudo/zudo-case/engineering/r9-fitfix-01/verification/preview-390.png

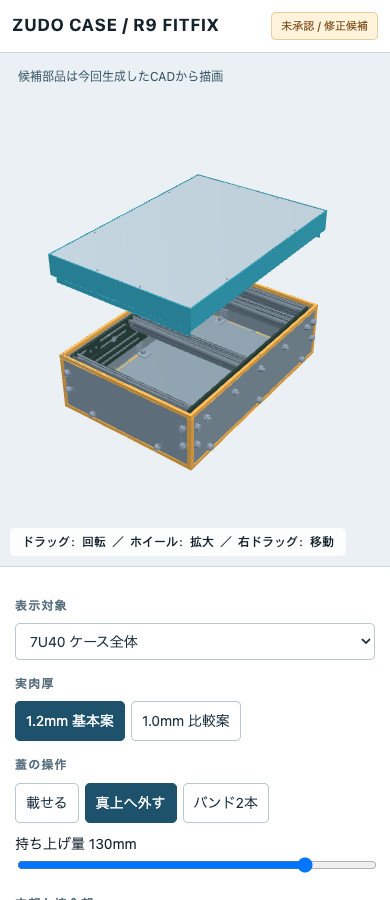
engineering/r9-fitfix-01/verification/preview-390.png
